zynthian/zynthian-case/Lasercut - PiScreen2/connectors/DIN5-rsonline.pdf

### RS Stock number 490-844

# ENGLISH

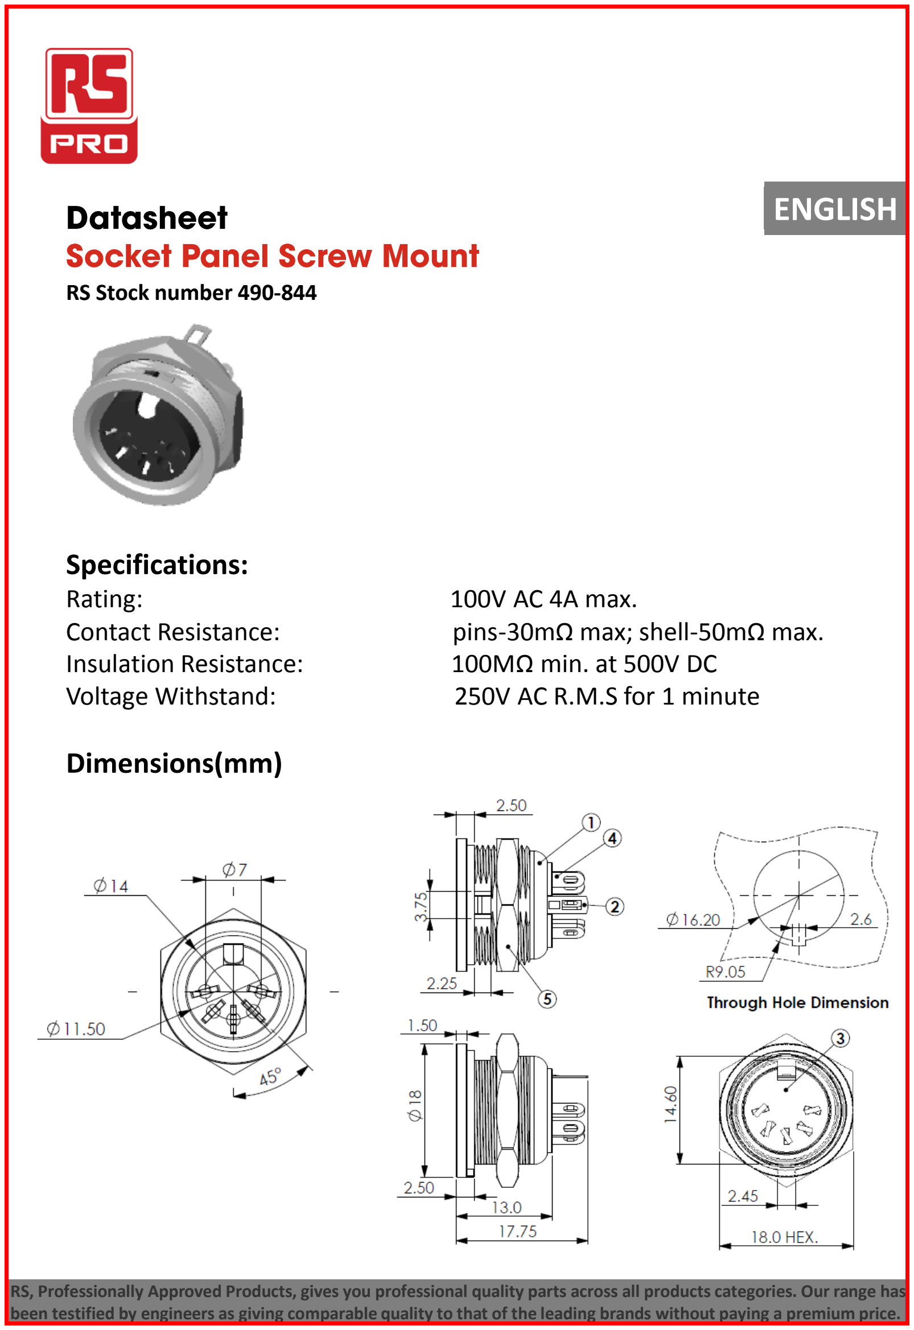
[picture p8: page 1]

## Specifications:

Rating: | 100V AC 4A max.
Contact Resistance: | pins-30mΩ max; shell-50mΩ max.
Insulation Resistance: | 100MΩ min. at 500V DC
Voltage Withstand: | 250V AC R.M.S for 1 minute

## Dimensions(mm)

RS, Professionally Approved Products, gives you professional quality parts across all products categories. Our range has been testified by engineers as giving comparable quality to that of the leading brands without paying a premium price.
