zynthian/zynthian-case/Aluminum - PiTFT28/zynthian_box_aluminum_v03_knobs.pdf

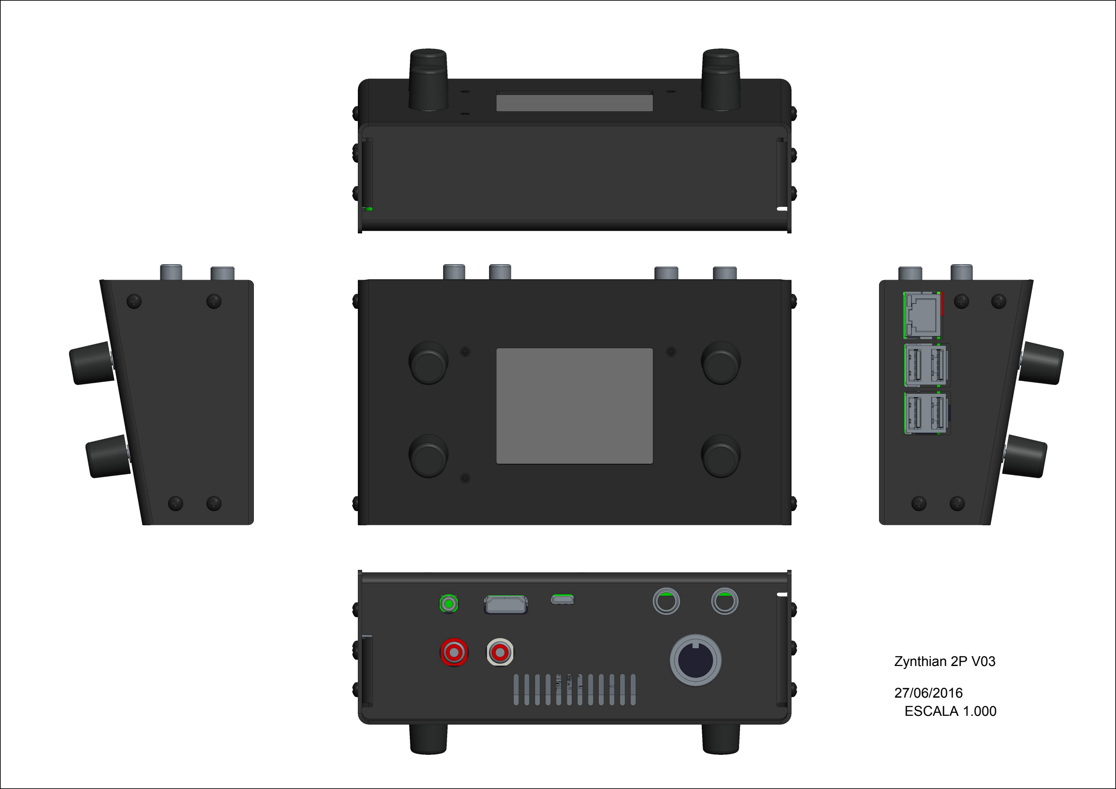
[picture p18: page 1]

Zynthian 2P V03
27/06/2016
ESCALA 1.000

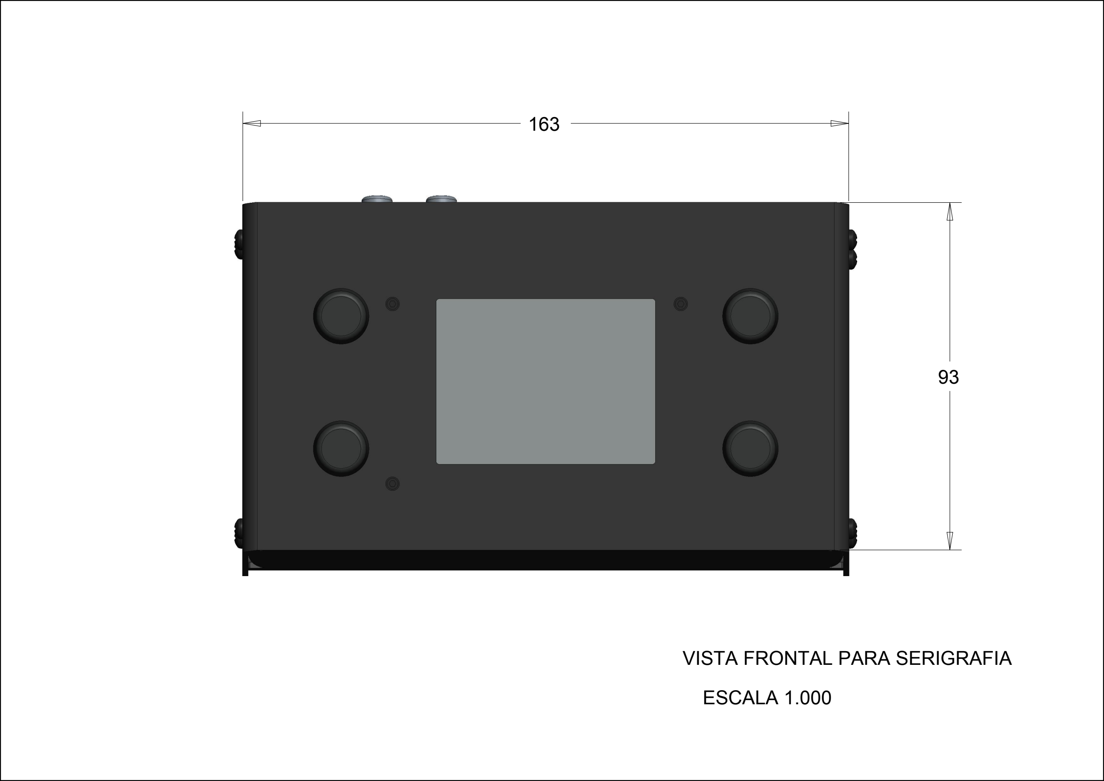
[picture p19: figure]
VISTA FRONTAL PARA SERIGRAFIA; ESCALA 1.000

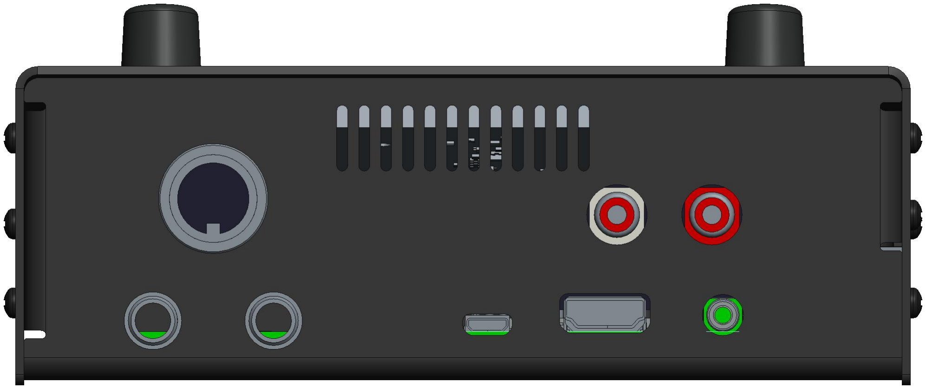
[picture p20: figure]

ESCALA 1.000

ESCALA 1.000

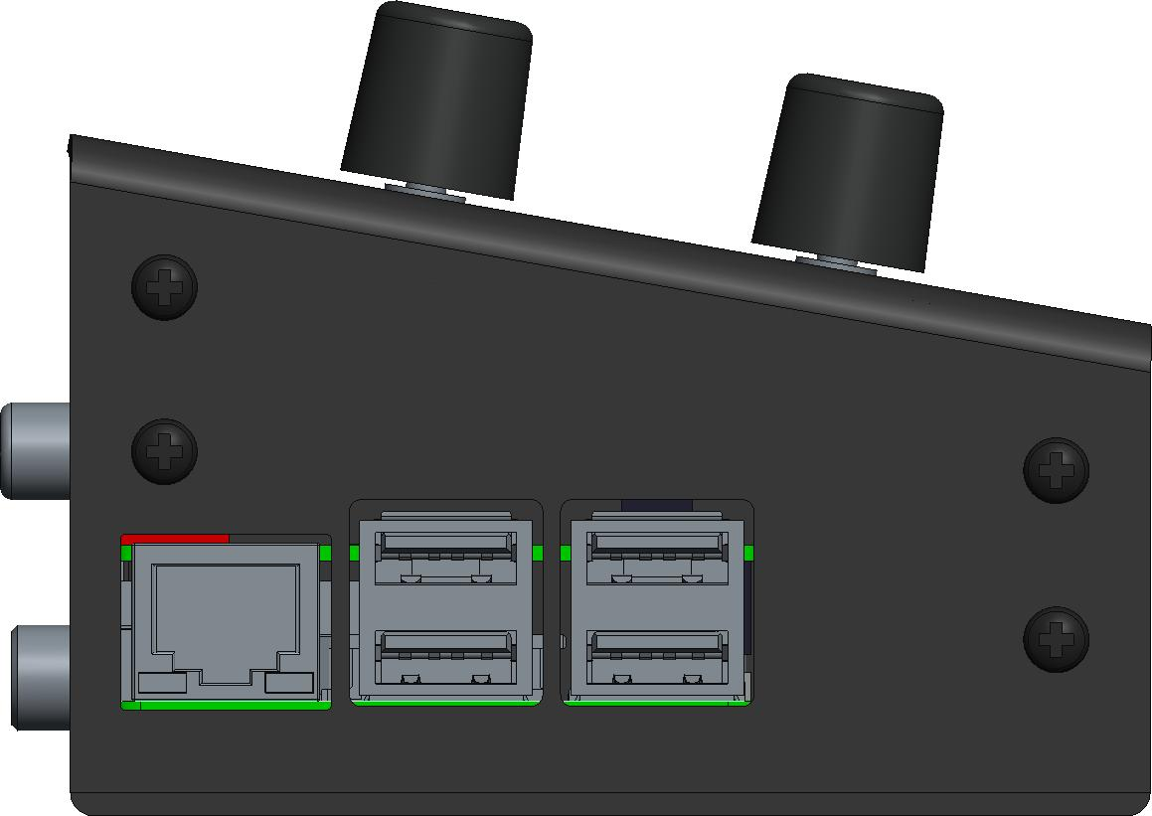
[picture p21: figure]

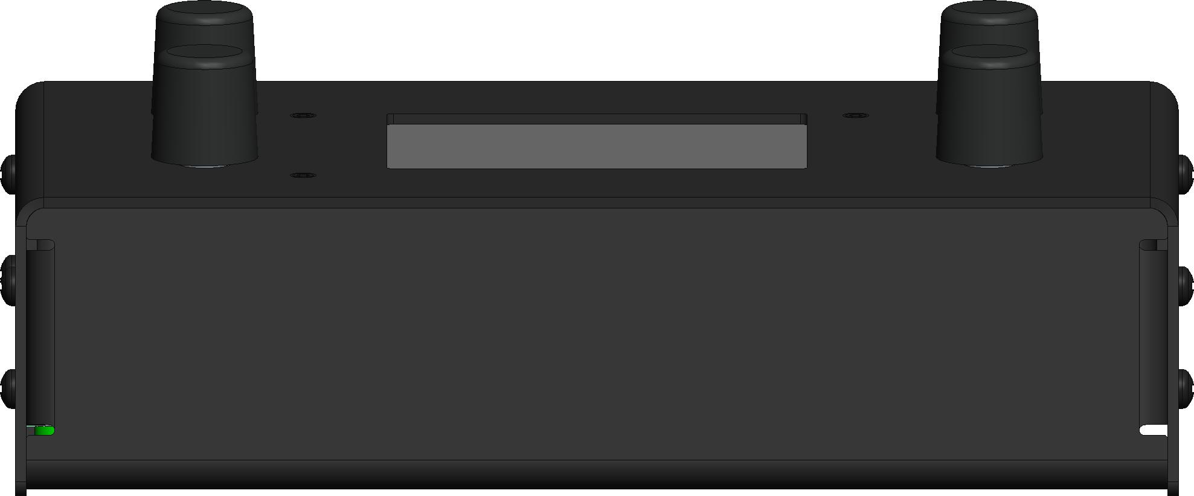
[picture p22: figure]

ESCALA 1.000
