zynthian/zynthian-case/Aluminum - PiTFT28/zynthian_box_aluminum_v03_serig.pdf

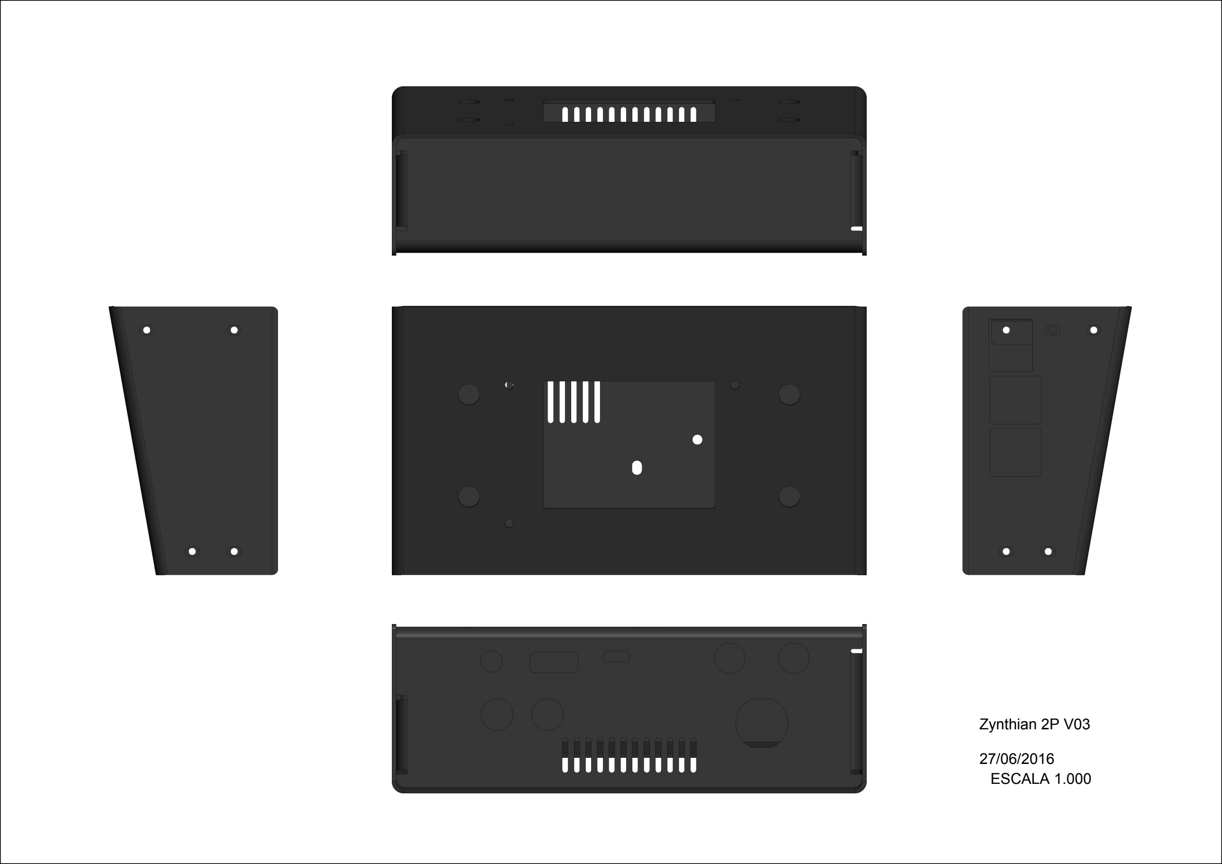
[picture p23: page 1]

Zynthian 2P V03
27/06/2016
ESCALA 1.000

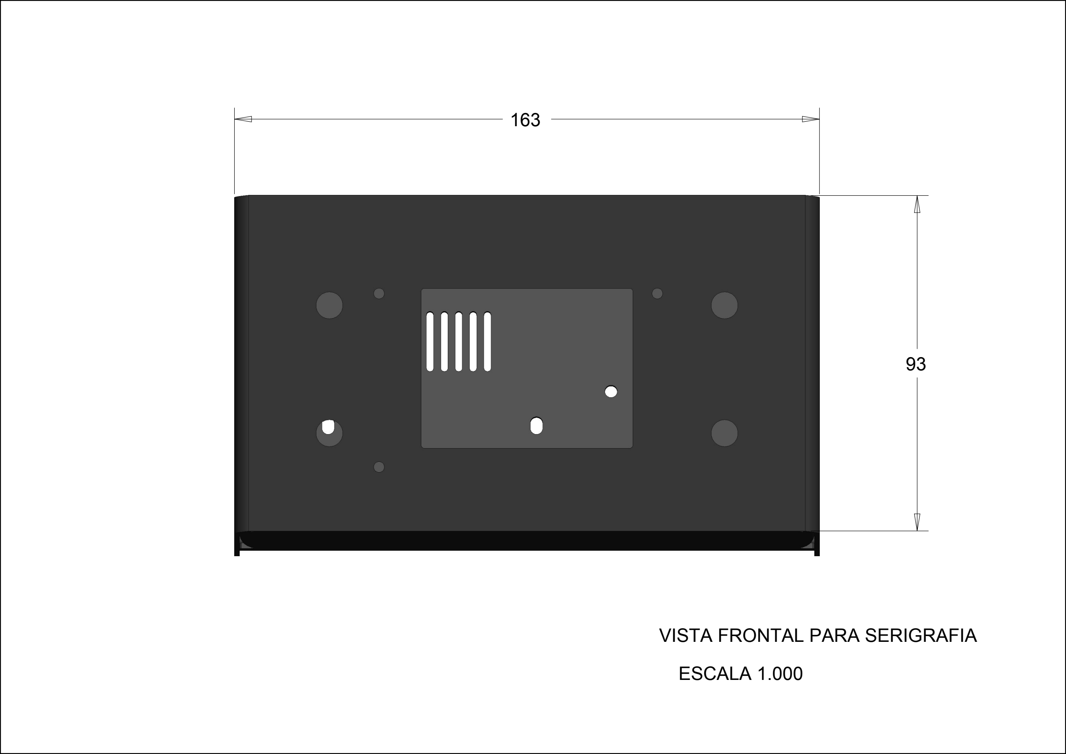
[picture p24: figure]
VISTA FRONTAL PARA SERIGRAFIA; ESCALA 1.000

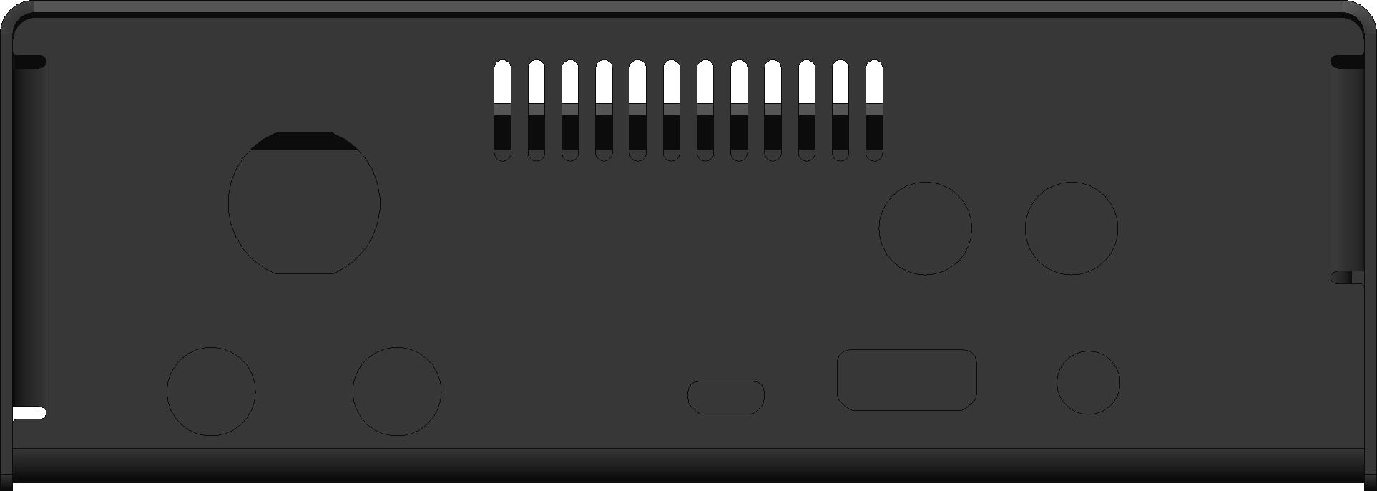
[picture p25: figure]

ESCALA 1.000

ESCALA 1.000

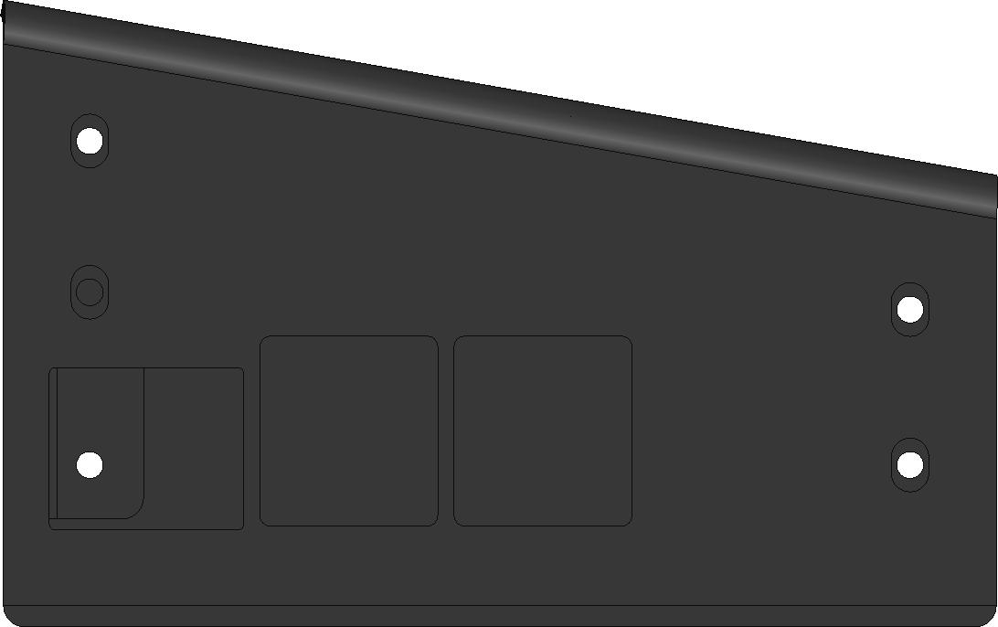
[picture p26: figure]

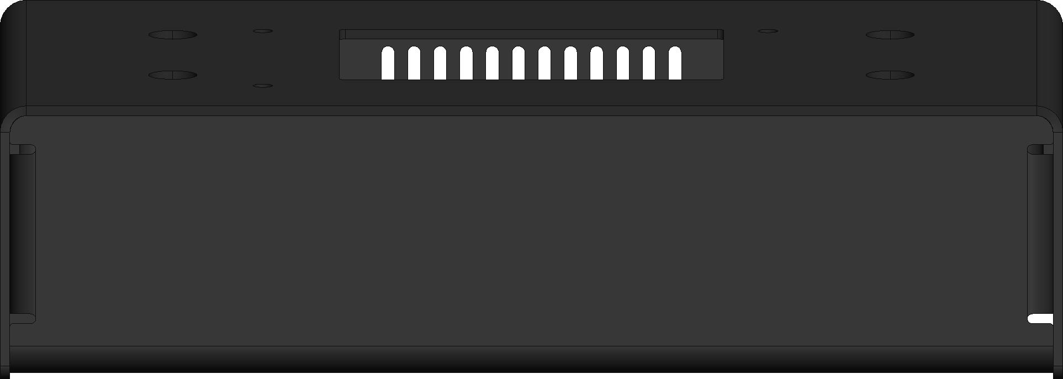
[picture p27: figure]

ESCALA 1.000
