zynthian/zynthian-case/Aluminum - PiTFT28/zynthian_box_aluminum_v04.pdf

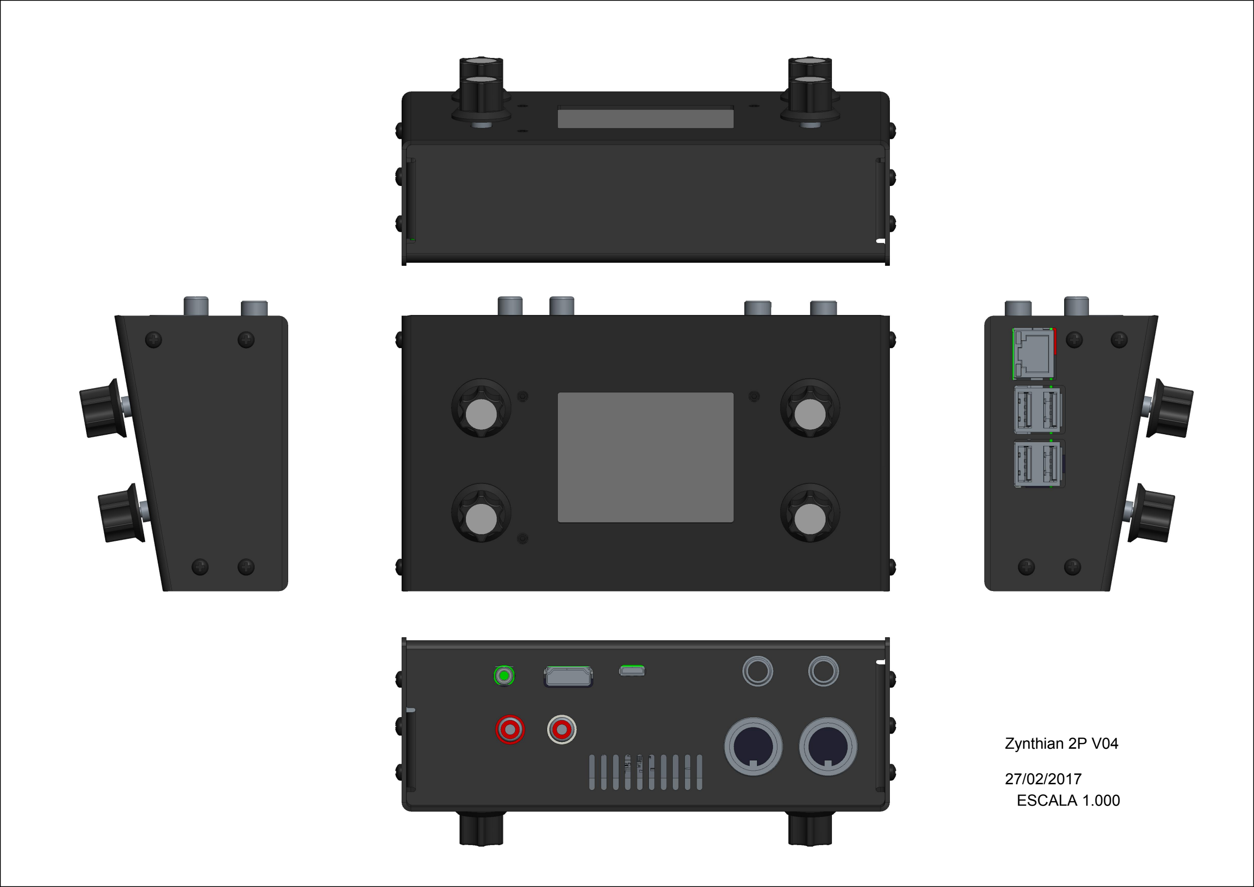
[picture p28: page 1]

Zynthian 2P V04
27/02/2017
ESCALA 1.000

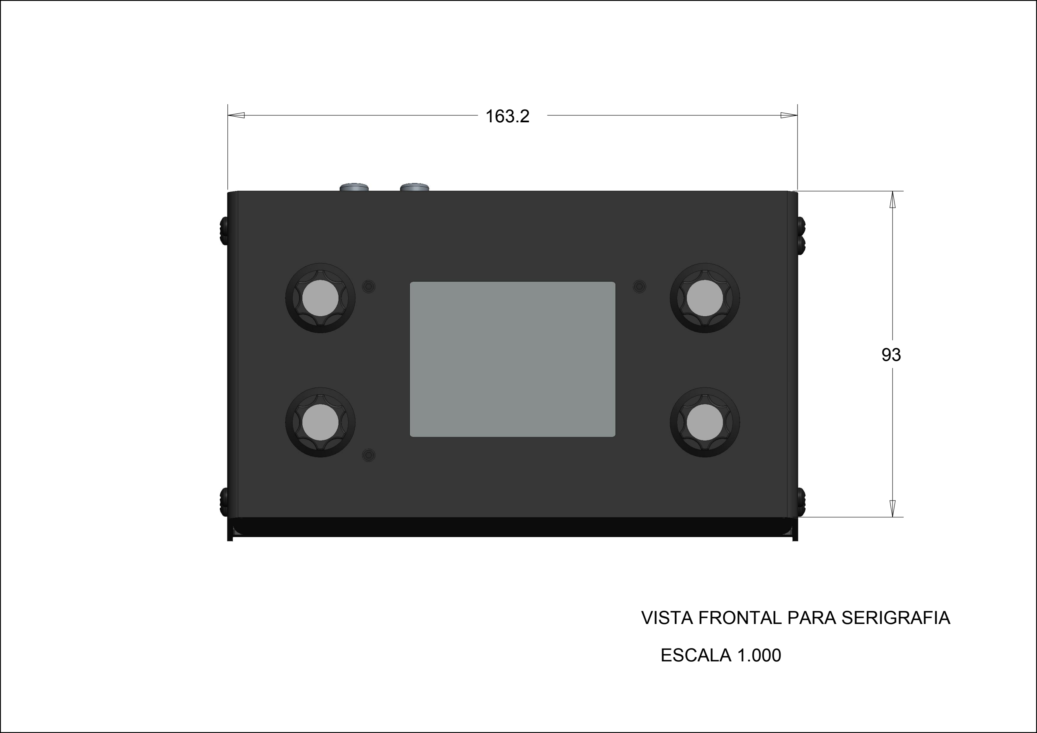
[picture p29: figure]
VISTA FRONTAL PARA SERIGRAFIA; ESCALA 1.000

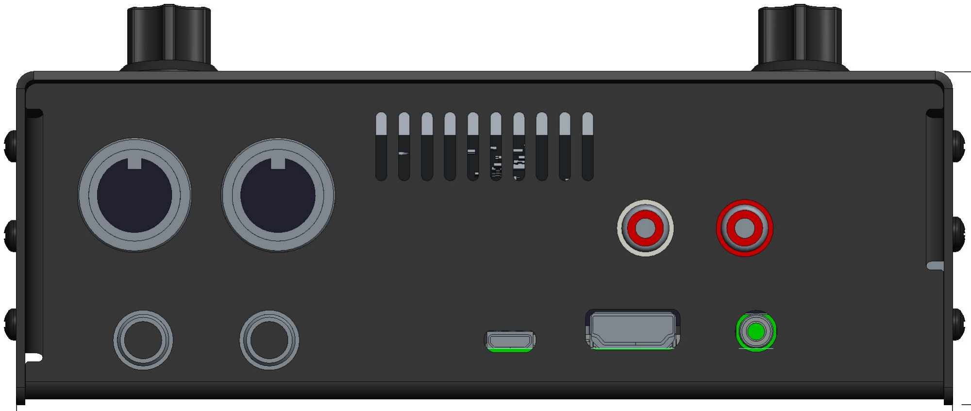
[picture p30: figure]

163.2

58.06

ESCALA 1.000

ESCALA 1.000

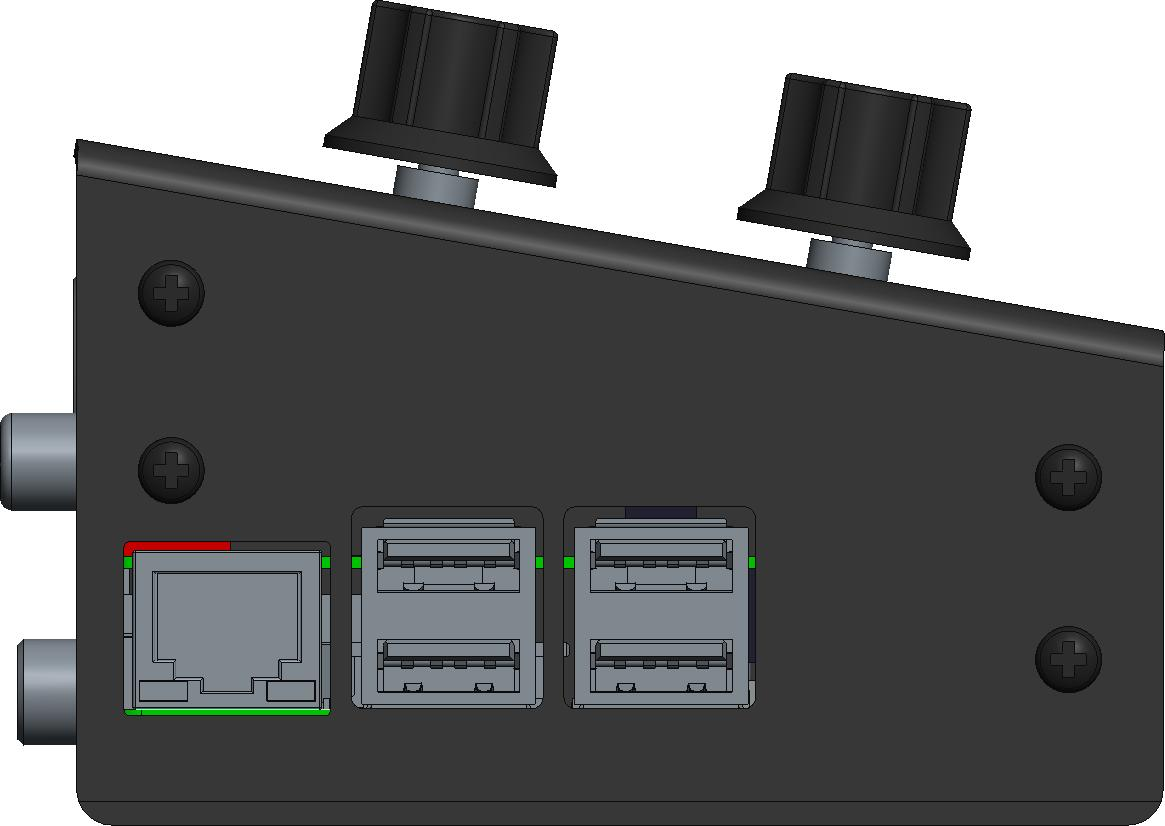
[picture p31: figure]

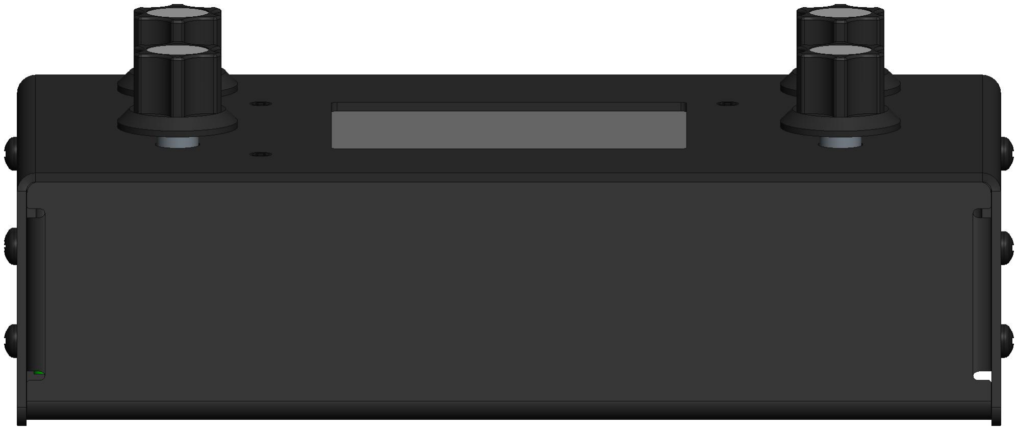
[picture p32: figure]

ESCALA 1.000
