zynthian/zynthian-case/Aluminum - PiTFT28/zynthian_box_aluminum_v04_back.pdf

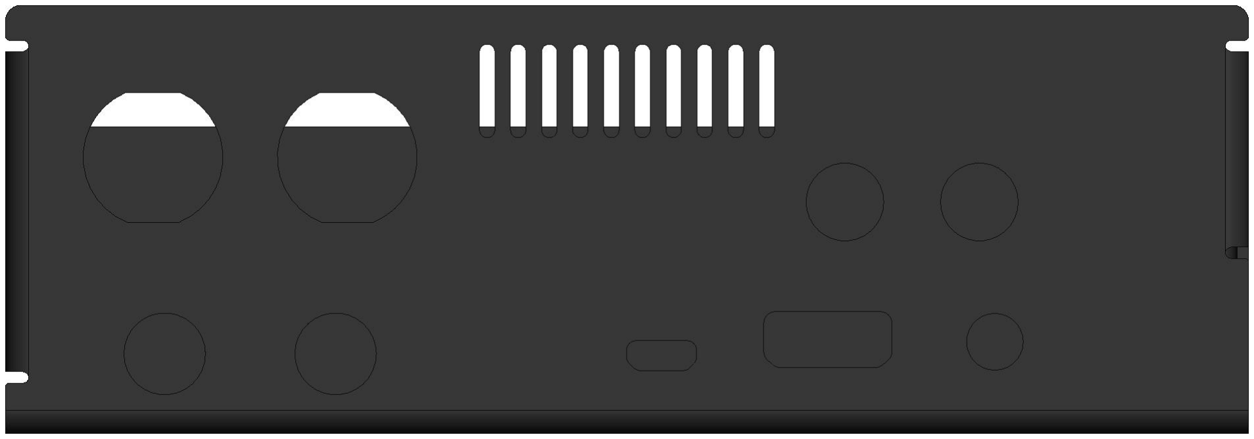
[picture p33: figure]

163.2

58.06

ESCALA 1.000
