zynthian/zynthian-case/Aluminum - PiTFT28/zynthian_box_aluminum_v04_base_desp.pdf

178.21

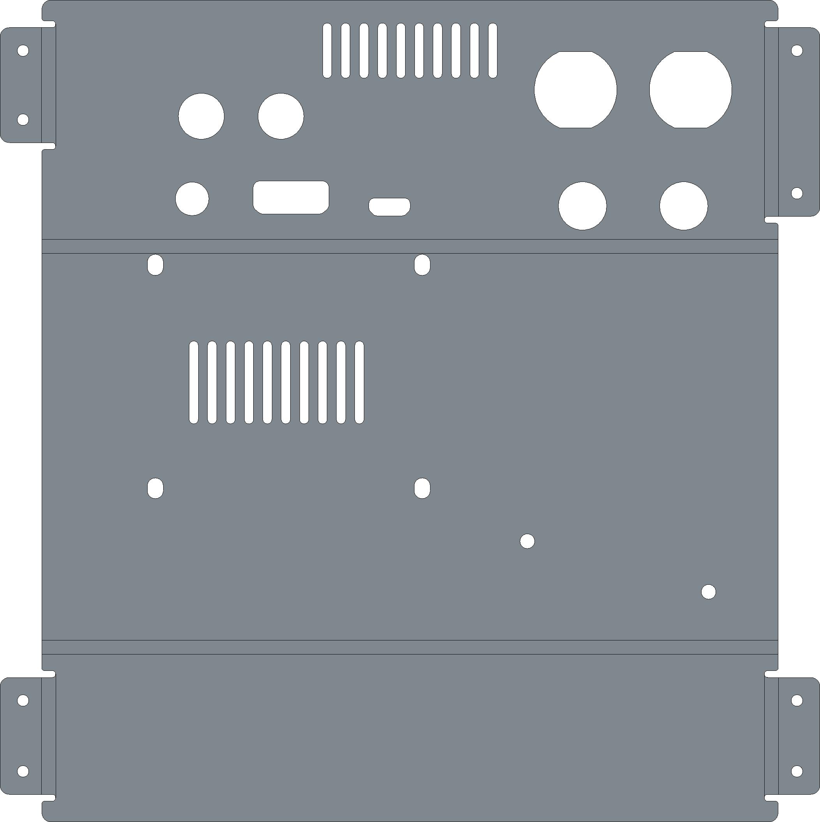
[picture p34: figure]

178.61

ESCALA 1.000
