zynthian/zynthian-case/Aluminum - PiScreen-v2.1/zynthian_box_2p_3midi_v05.pdf

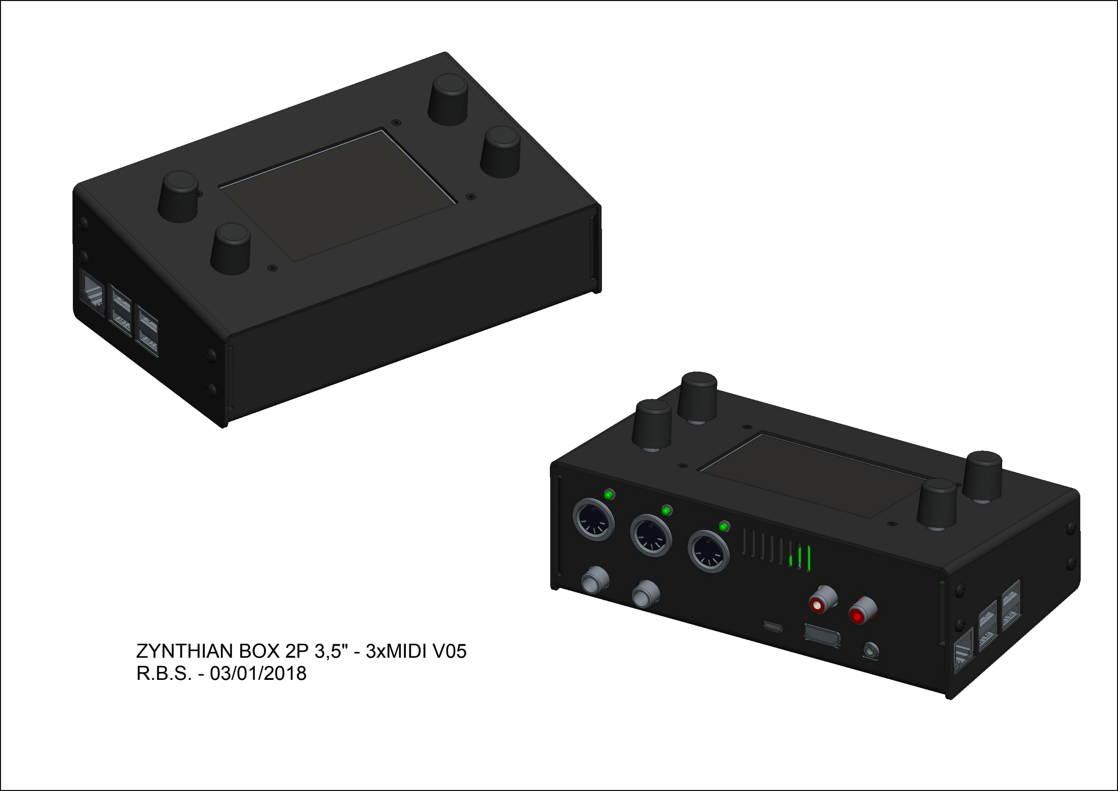
[picture p35: page 1]

ZYNTHIAN BOX 2P 3,5" - 3xMIDI V05 R.B.S. - 03/01/2018

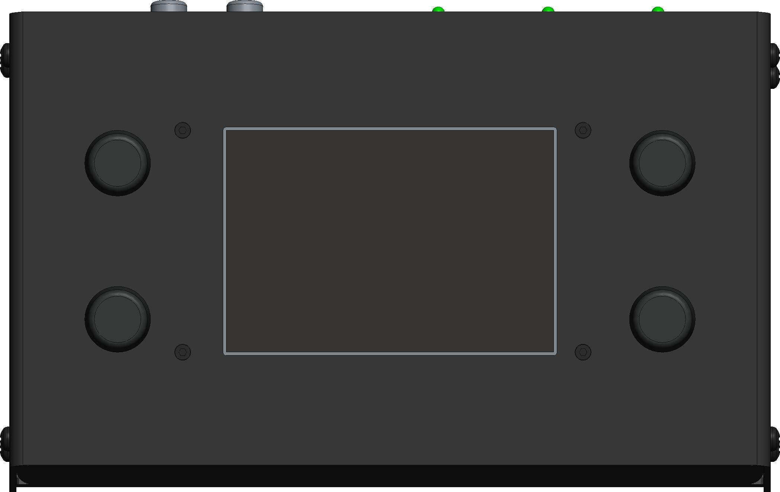
[picture p36: figure]

FRONTAL PARA SERIGRAFIA
ZYNTHIAN BOX 2P 3,5" 3xMIDI V05
ESCALA 1.000 | R.B.S - 03/01/2018

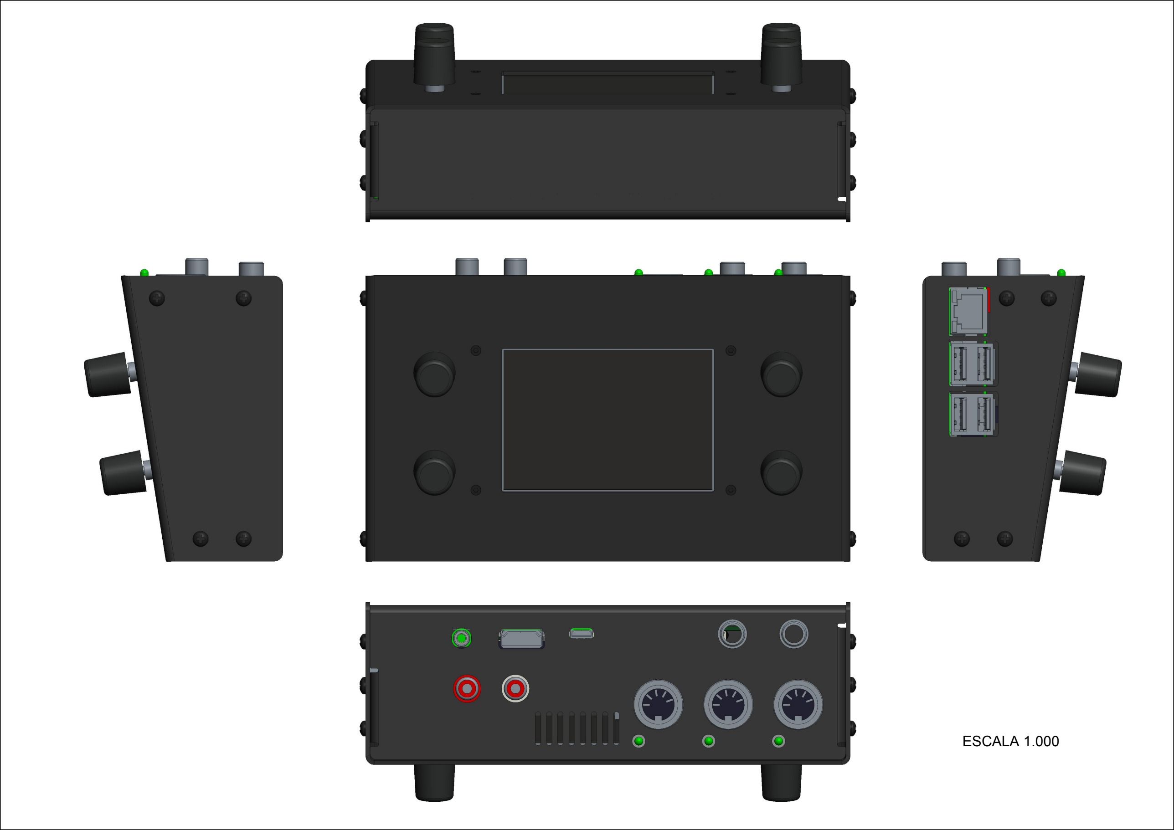
[picture p37: page 3]

ESCALA 1.000

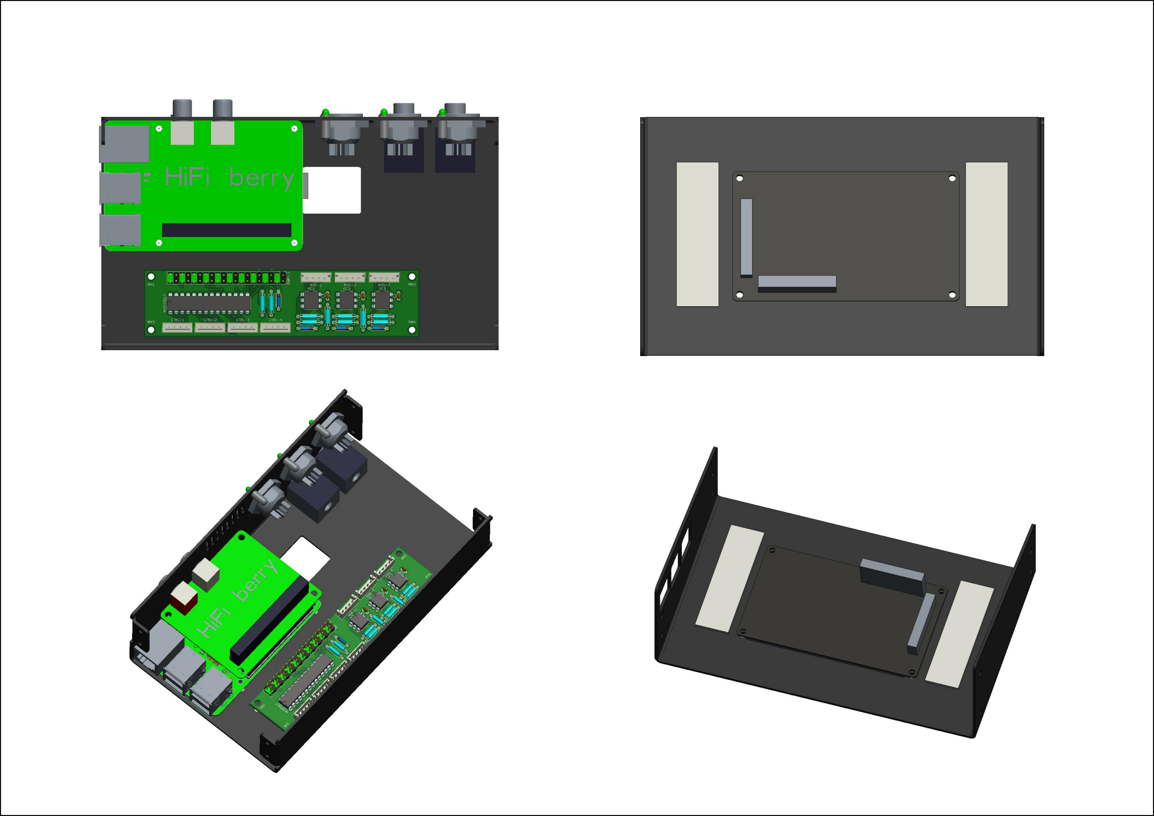
[picture p38: page 4]

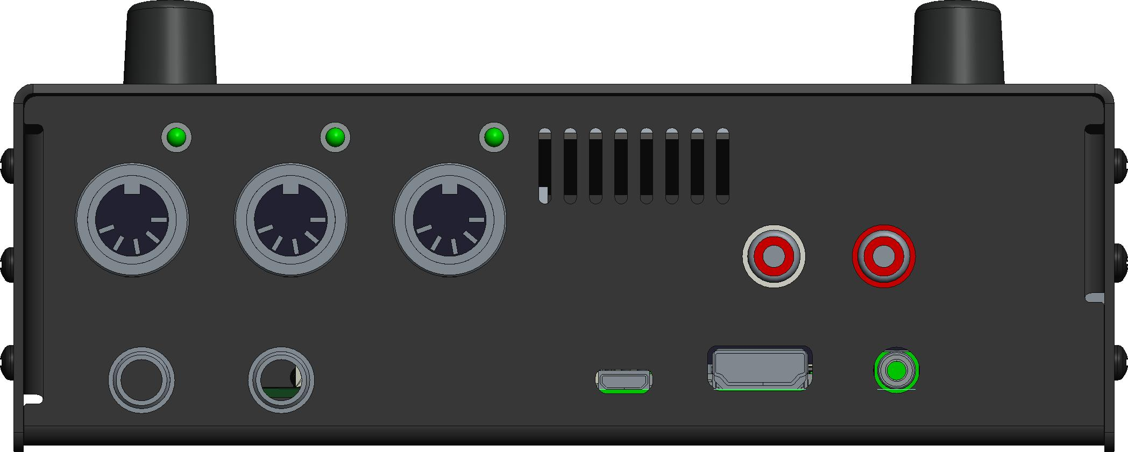
[picture p39: figure]

ESCALA 1.000
