zynthian/zynthian-case/Aluminum - PiScreen-v2/zynthian_box_2p_3_5_v04.pdf

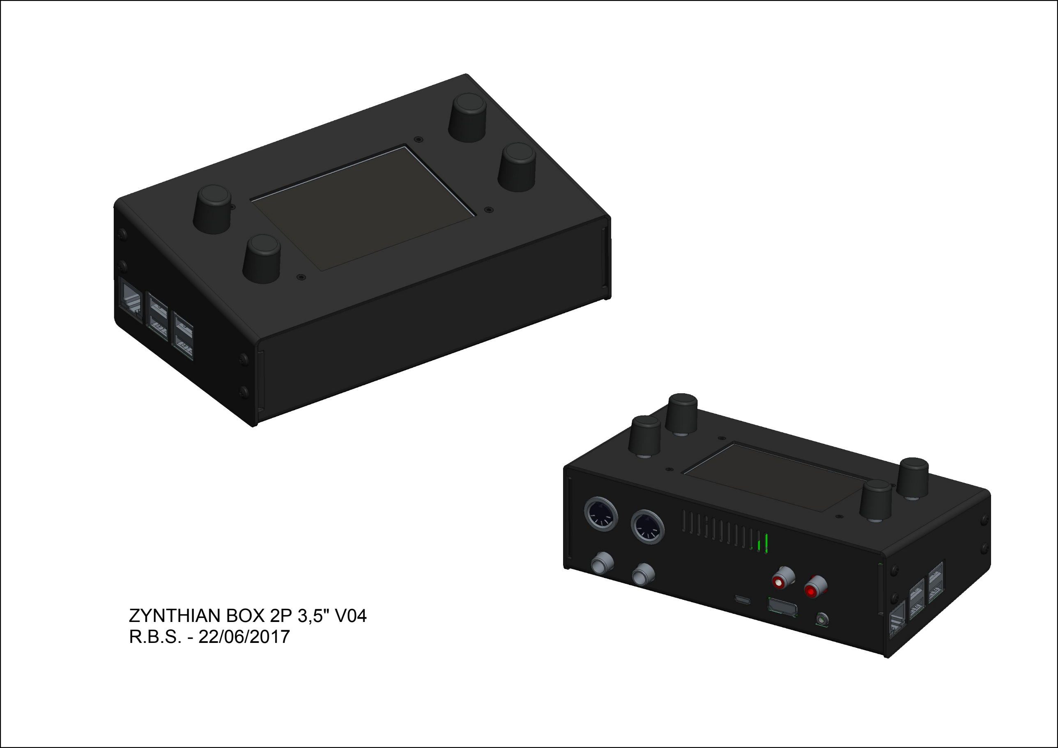
[picture p40: page 1]

ZYNTHIAN BOX 2P 3,5" V04
R.B.S. - 22/06/2017

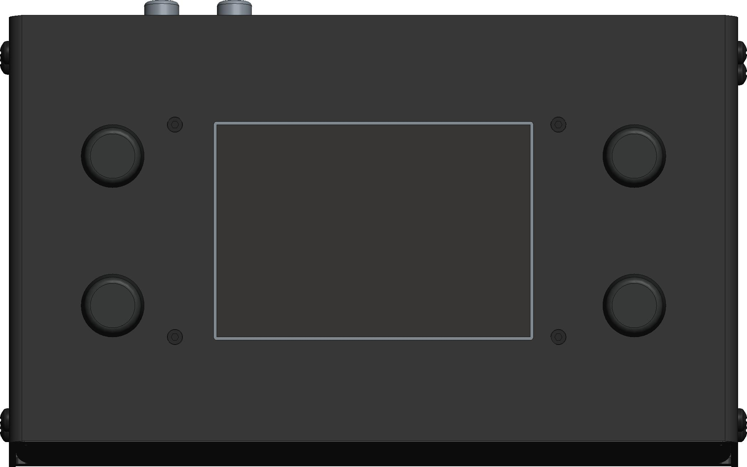
[picture p41: figure]

FRONTAL PARA SERIGRAFIA
ZYNTHIAN BOX 2P 3,5" V04
ESCALA 1.000 | R.B.S - 23/05/2017

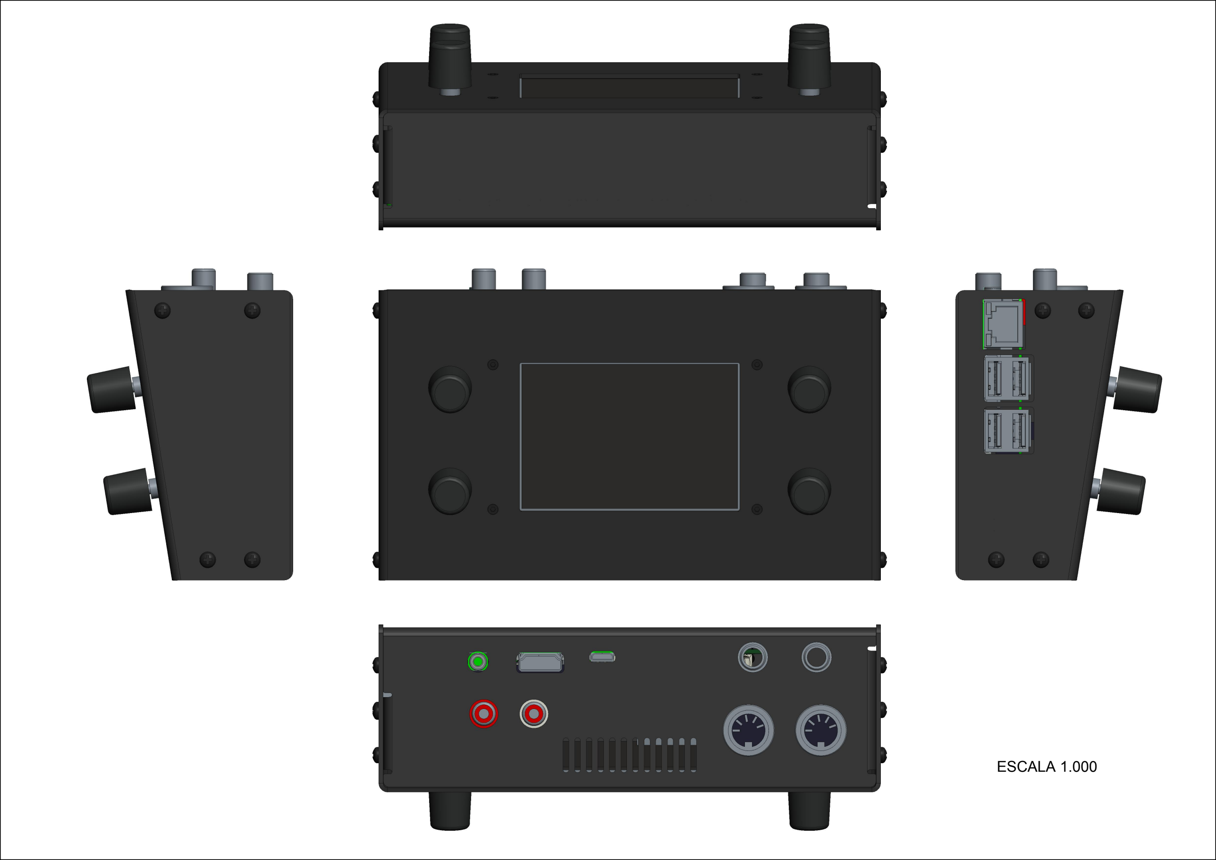
[picture p42: page 3]

ESCALA 1.000

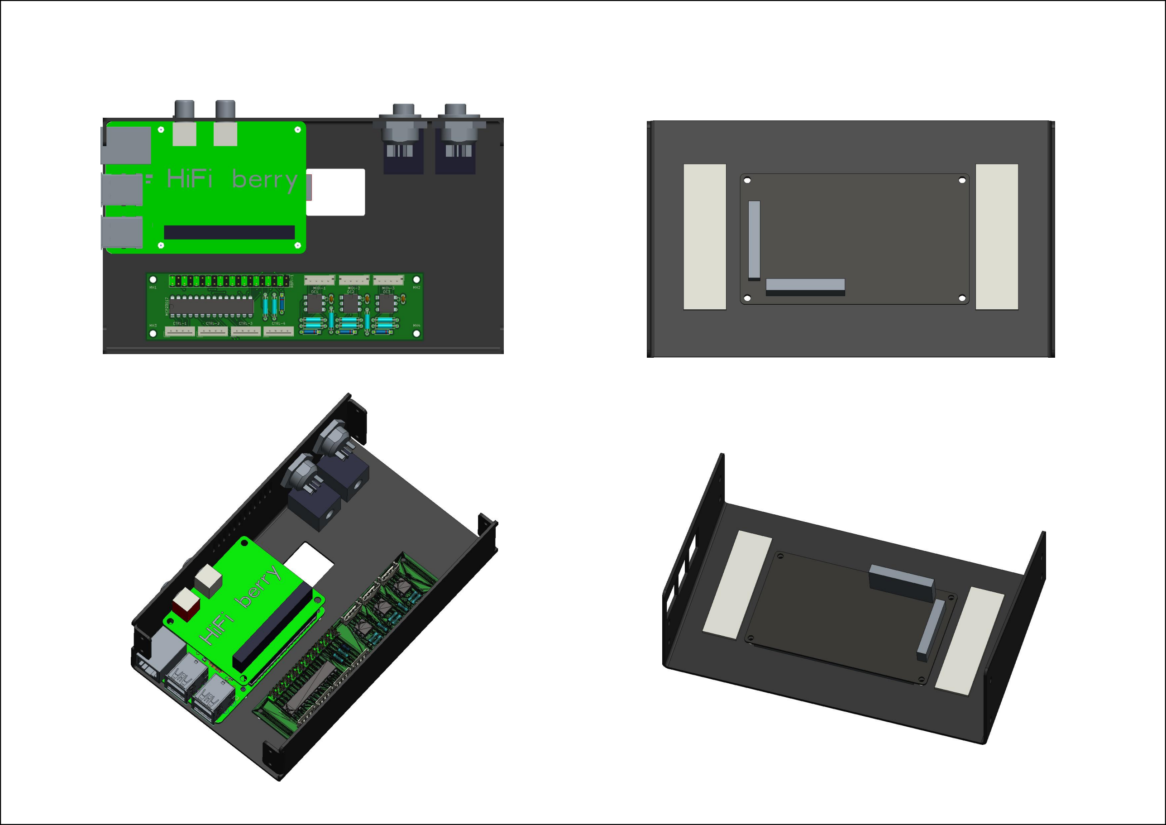
[picture p43: page 4]
