zynthian/zynthian-case/Aluminum - PiScreen-v2.2/old/zynthian_box_2p_v06_mjack.pdf

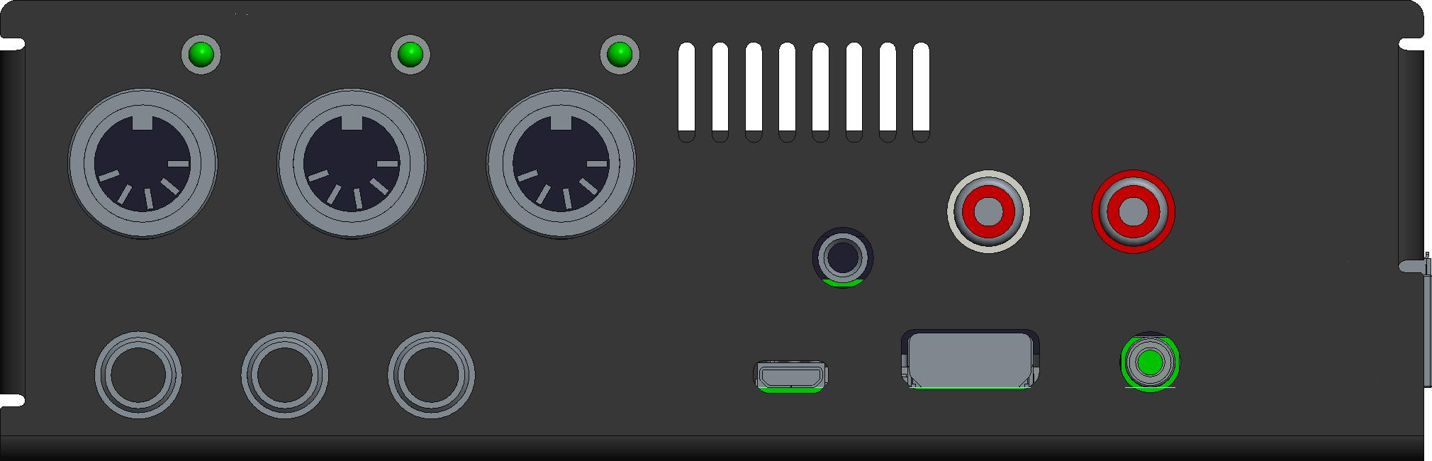
[picture p44: figure]

ESCALA 1.000
