zynthian/zynthian-case/Steel - PiTFT28/old/zynthian_box_V01_29_7_15.pdf

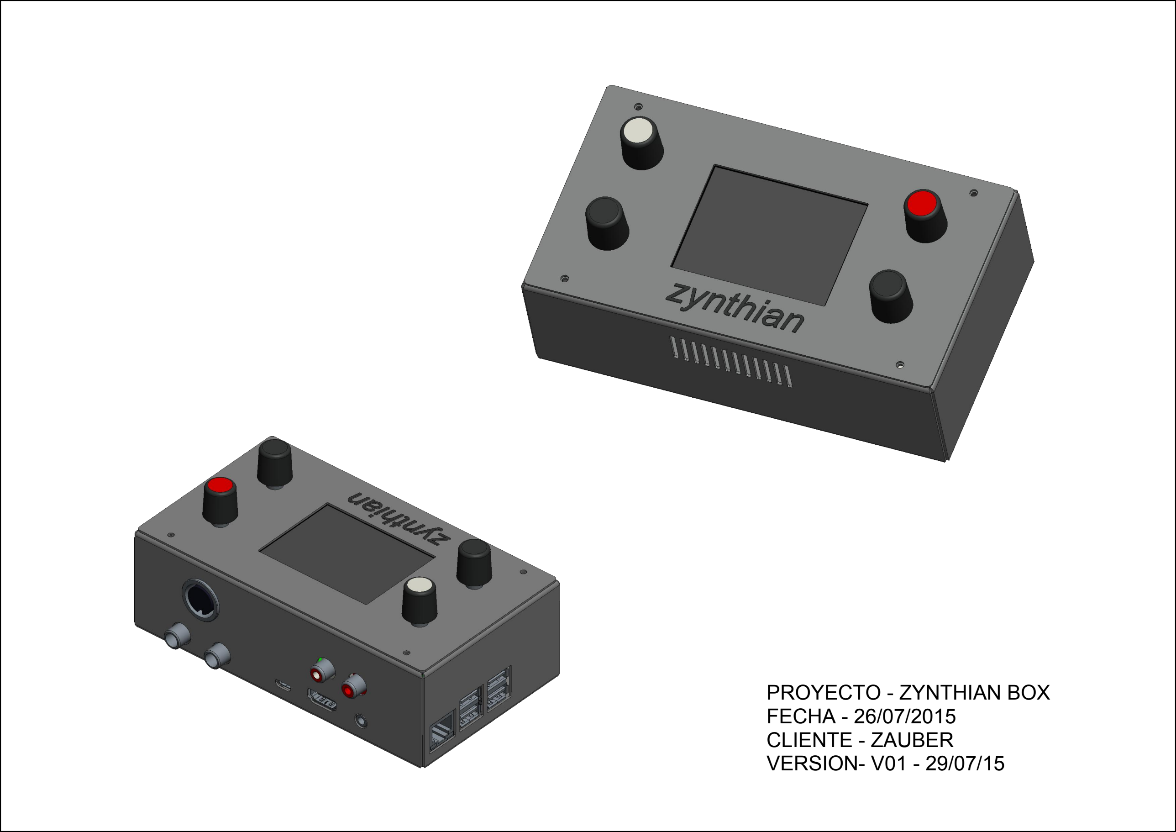
[picture p45: page 1]

PROYECTO - ZYNTHIAN BOX
FECHA - 26/07/2015
CLIENTE - ZAUBER
VERSION- V01 - 29/07/15

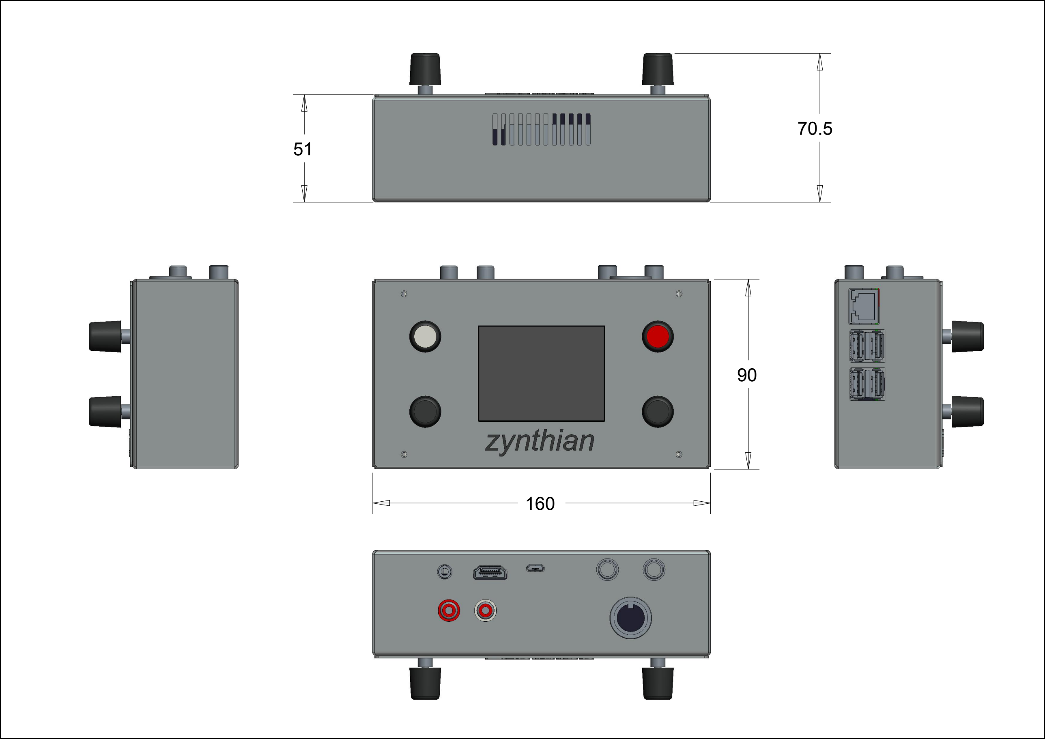
[picture p46: figure]
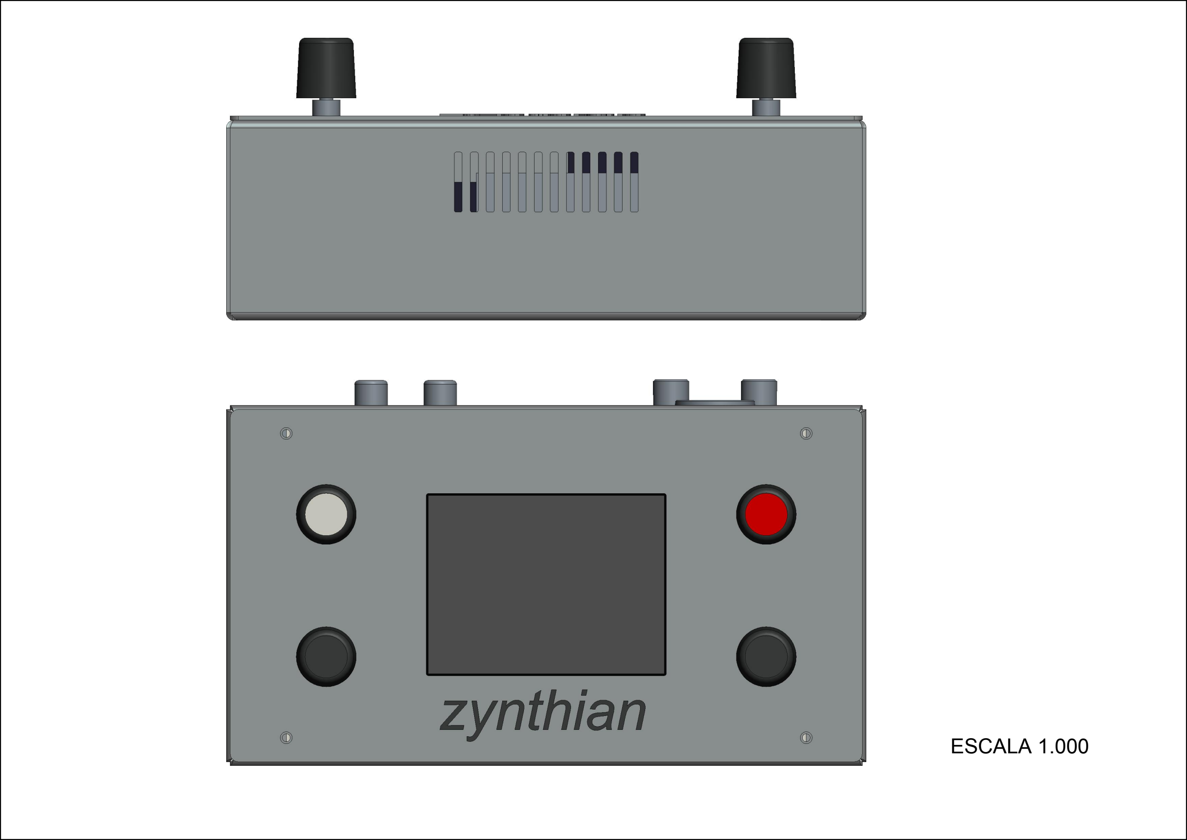
[picture p47: page 3]

ESCALA 1.000

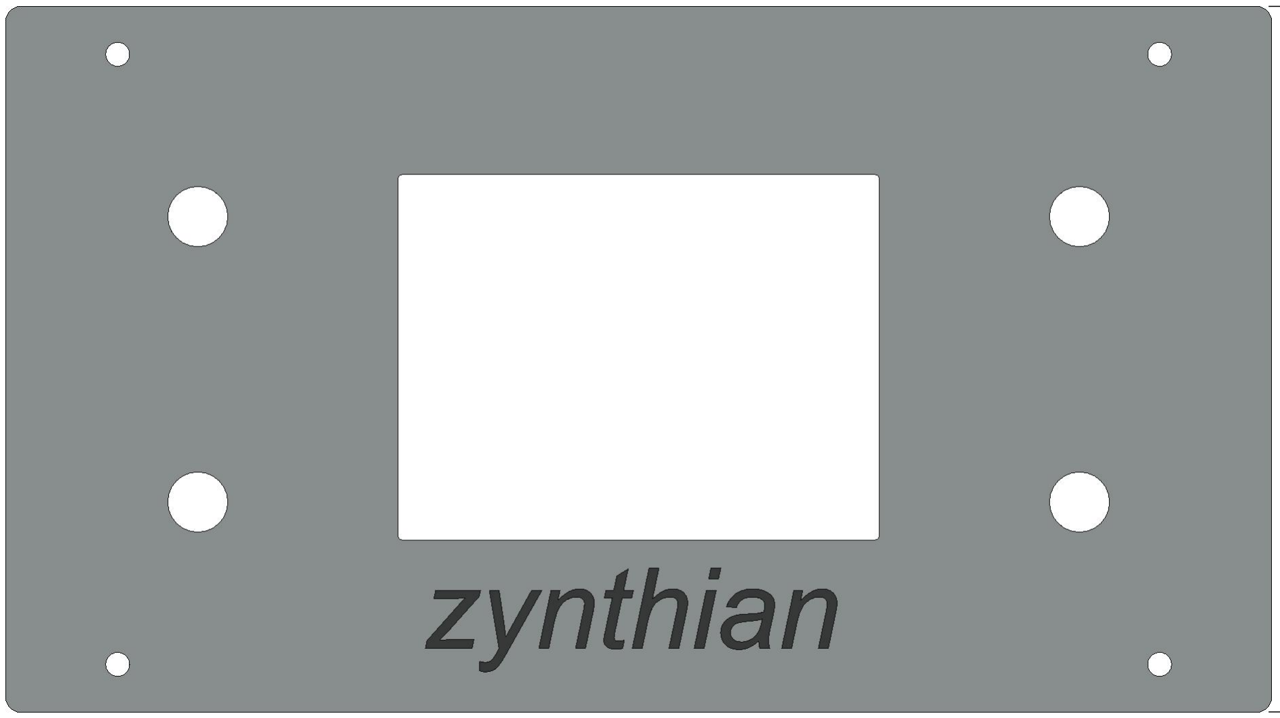
[picture p48: figure]

88

ESCALA 1.000

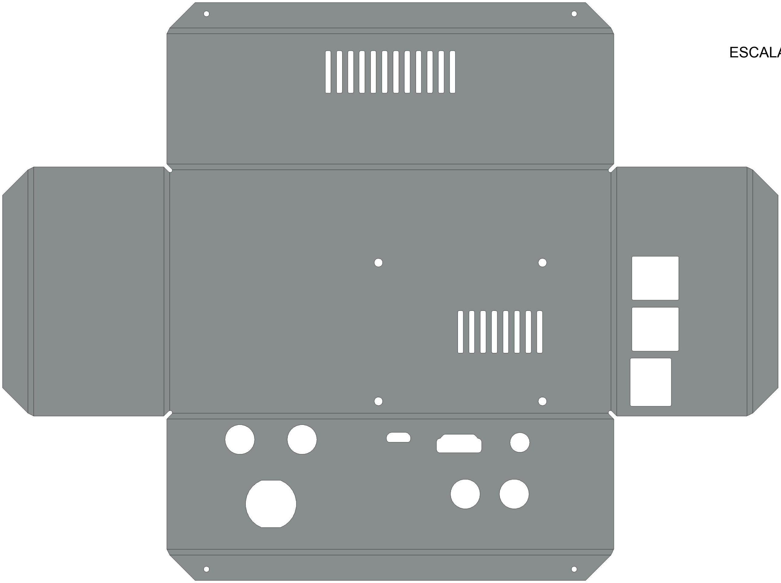
[picture p49: figure]

204.28

274.28

ESCALA 1.000

88

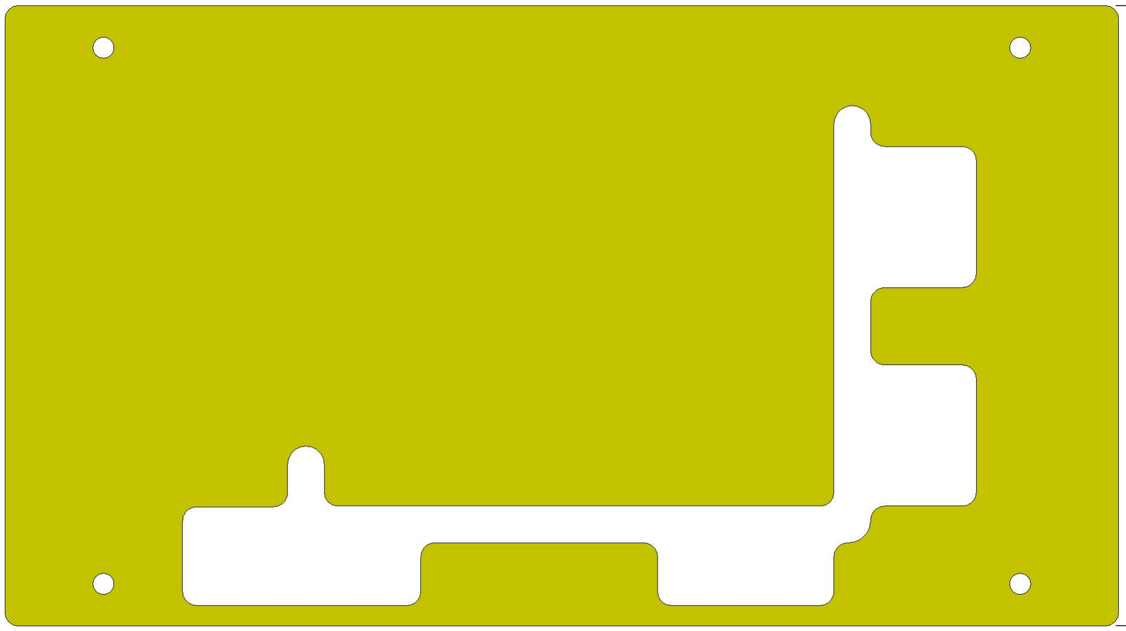
[picture p50: figure]

ESCALA 1.000

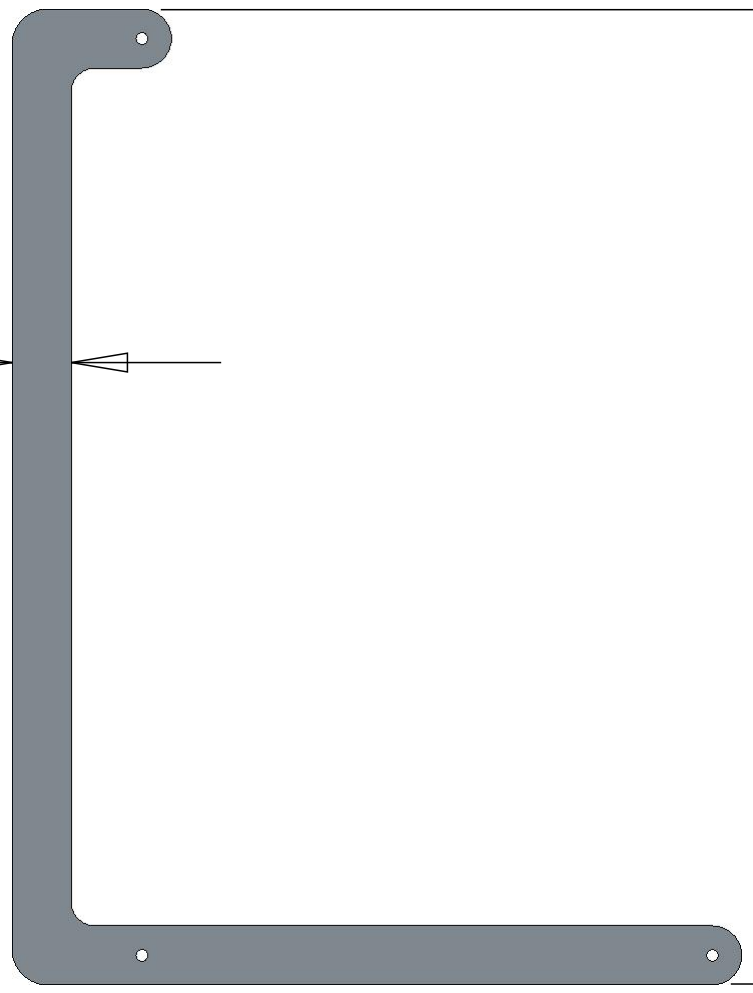
[picture p51: figure]

82.47

5

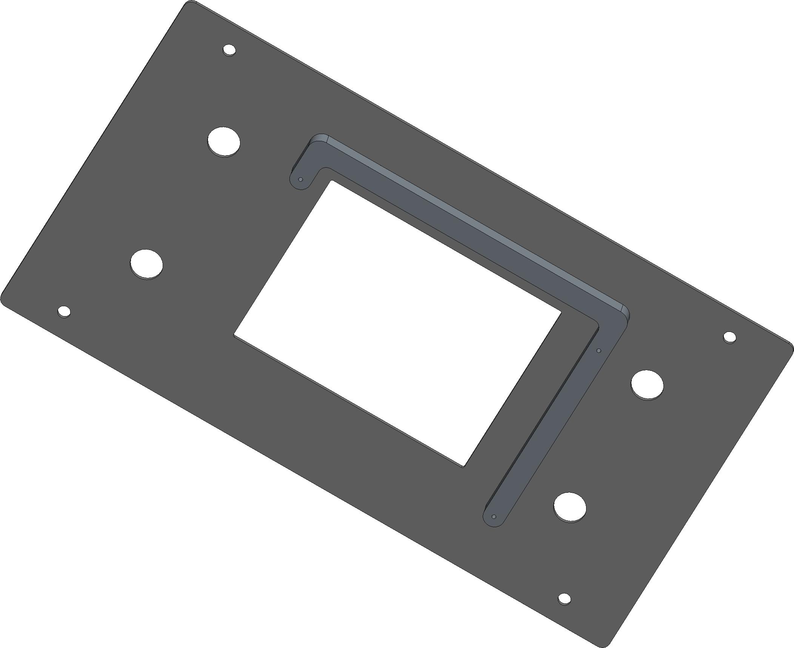
[picture p52: figure]

ESCALA 1.000
