zynthian/zynthian-case/3DPrint - Waveshare35/back_view.jpg

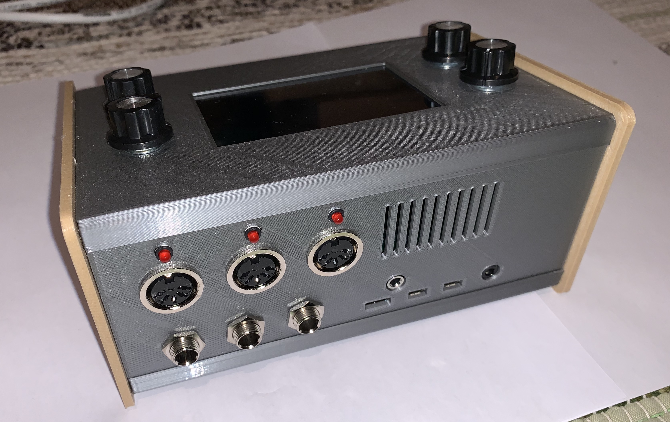
3DPrint - Waveshare35/back_view.jpg
