zynthian/zynthian-case/3DPrint - Waveshare35/boards_mounting.jpg

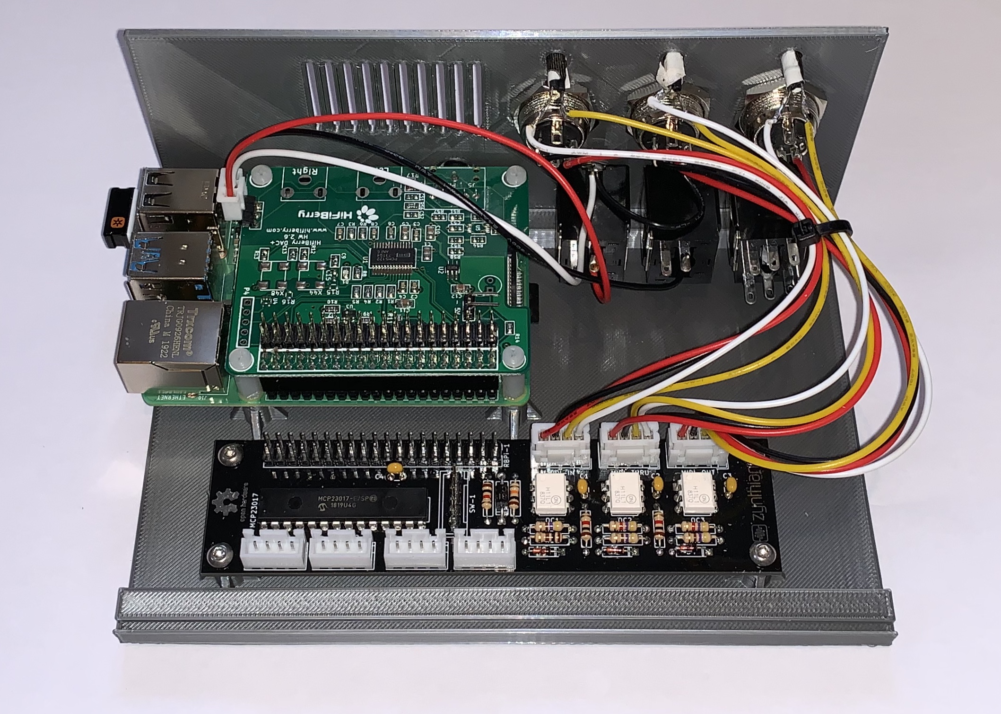
3DPrint - Waveshare35/boards_mounting.jpg
