zynthian/zynthian-case/3DPrint - Waveshare35/display_mounting.jpg

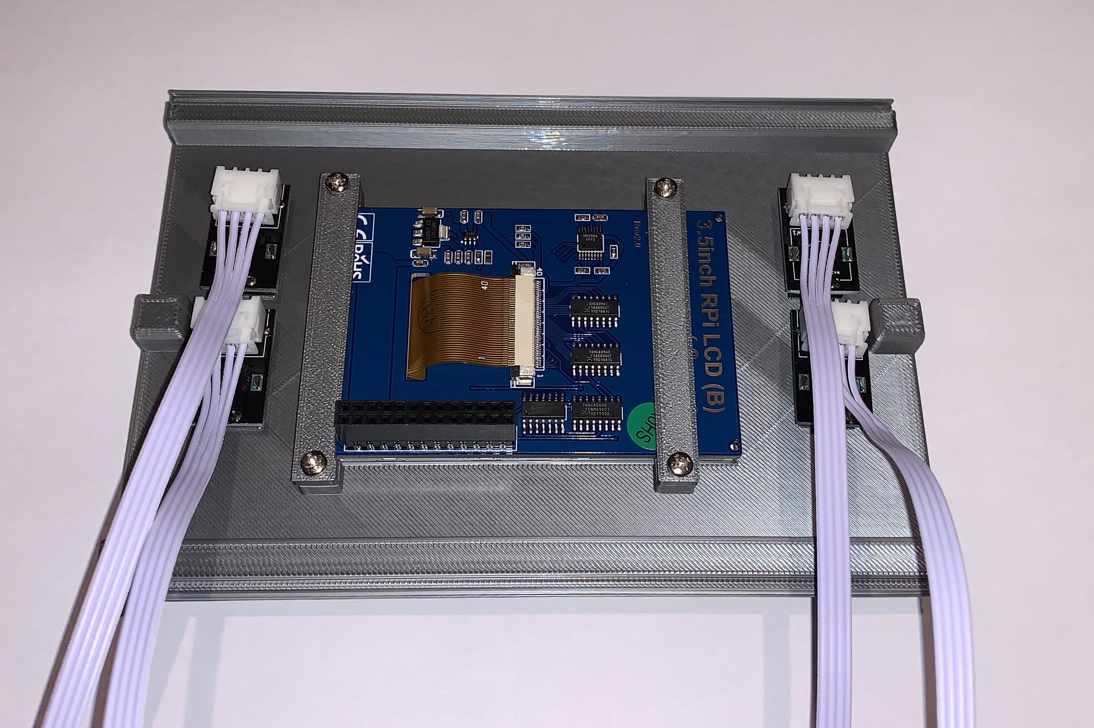
3DPrint - Waveshare35/display_mounting.jpg
