zynthian/zynthian-case/3DPrint - Waveshare35/front_view.jpg

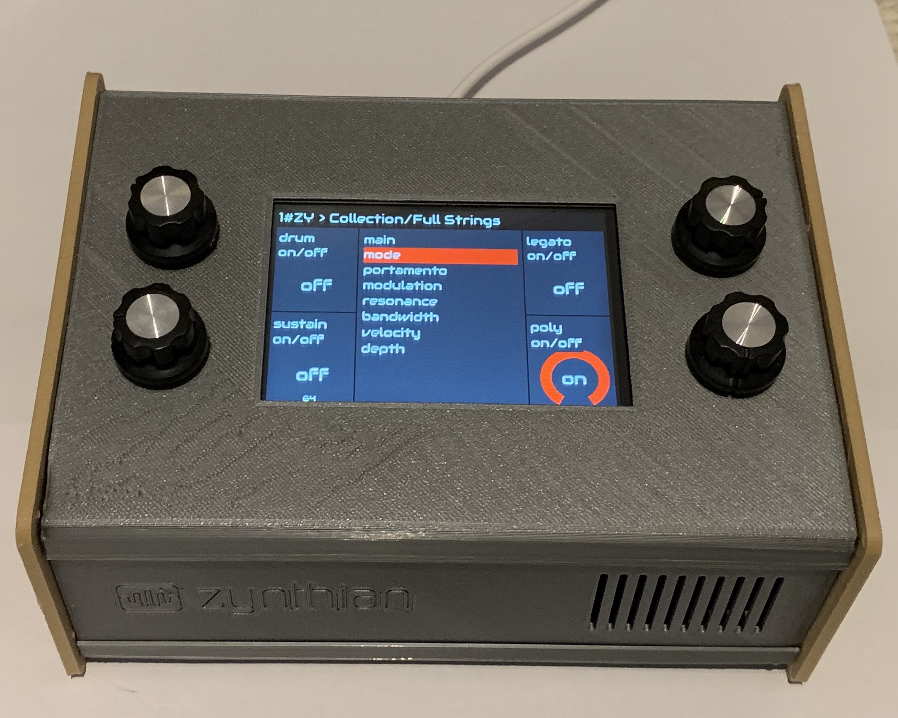
3DPrint - Waveshare35/front_view.jpg
