zynthian/zynthian-case/Aluminum - PiScreen-v2.2/g1220.png

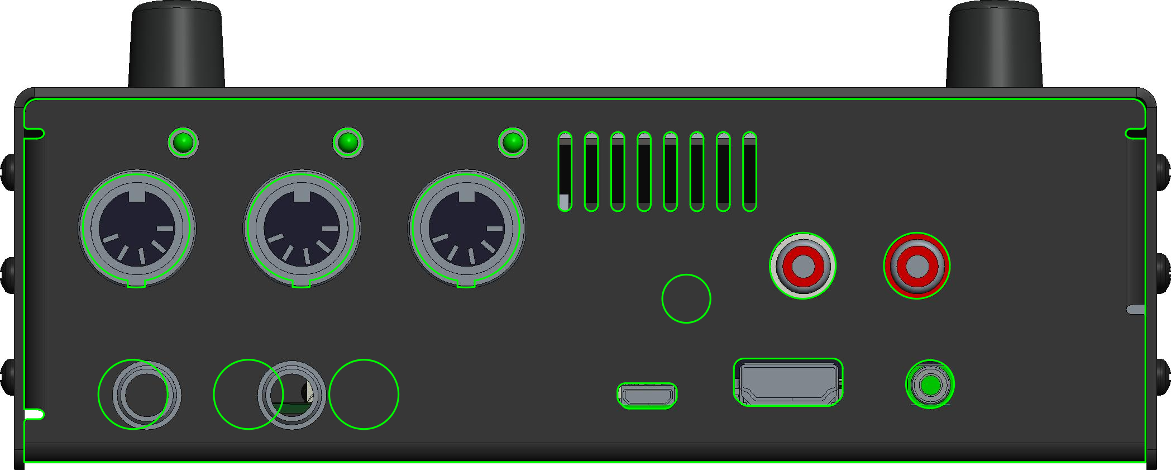
Aluminum - PiScreen-v2.2/g1220.png
