zynthian/zynthian-case/Aluminum - PiScreen-v2.2/image002.jpg

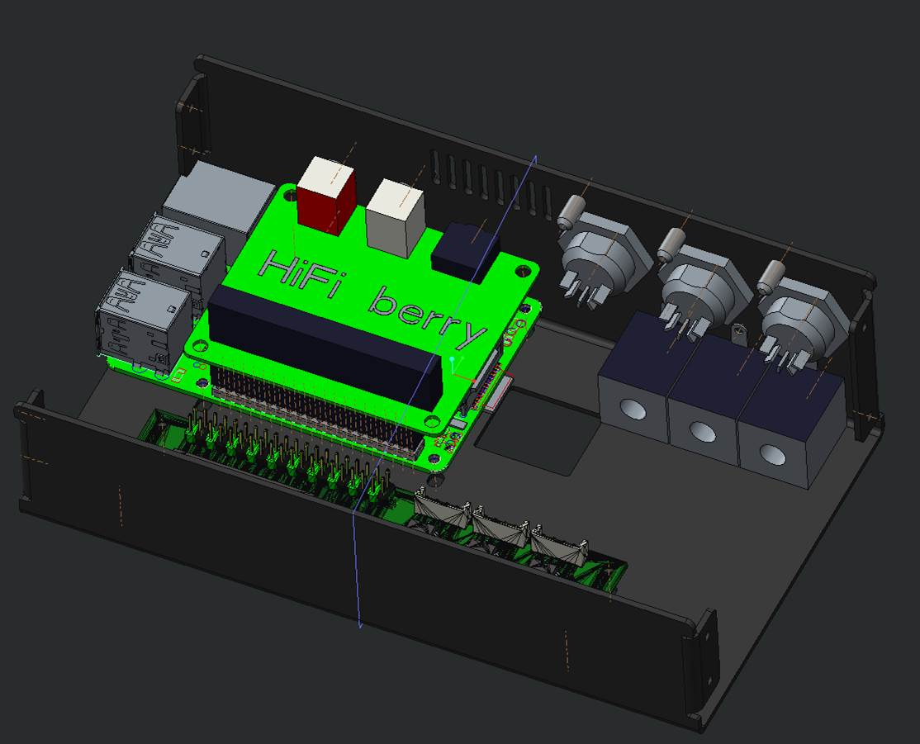
Aluminum - PiScreen-v2.2/image002.jpg
