zynthian/zynthian-case/Aluminum - PiScreen-v2.2/image007.jpg

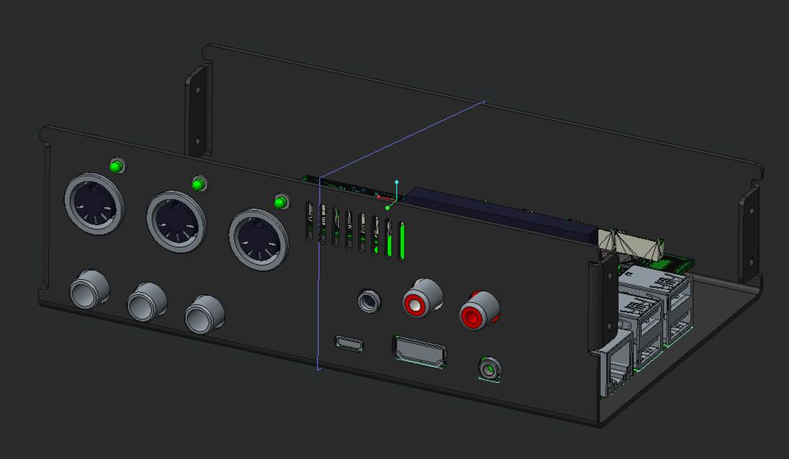
Aluminum - PiScreen-v2.2/image007.jpg
