zynthian/zynthian-case/Aluminum - PiTFT28/zynthian_aluminum_case_kit.jpg

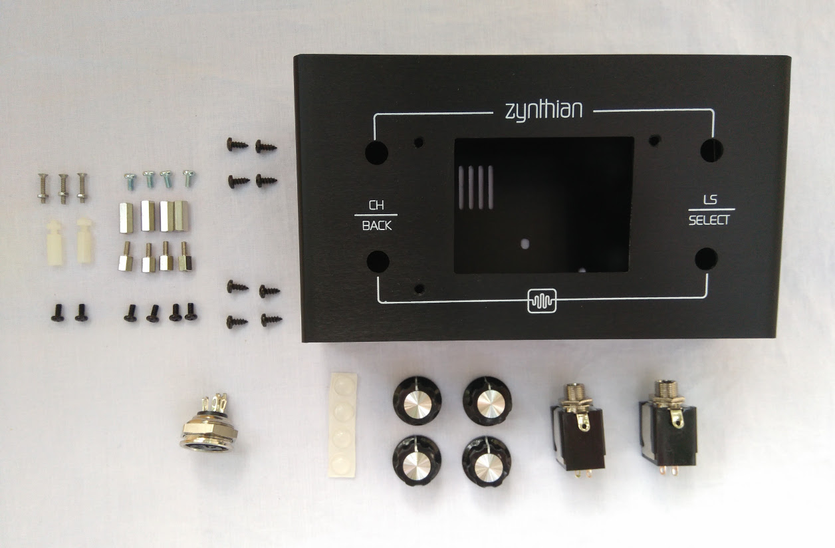
Aluminum - PiTFT28/zynthian_aluminum_case_kit.jpg
