zynthian/zynthian-case/Aluminum - PiTFT28/zynthian_box_alucase_02.jpg

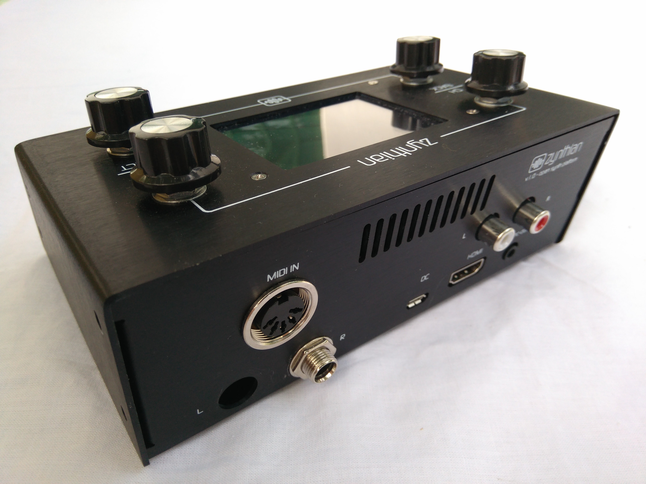
Aluminum - PiTFT28/zynthian_box_alucase_02.jpg
