zynthian/zynthian-case/Aluminum - Zynscreen-v4/knob_a01.png

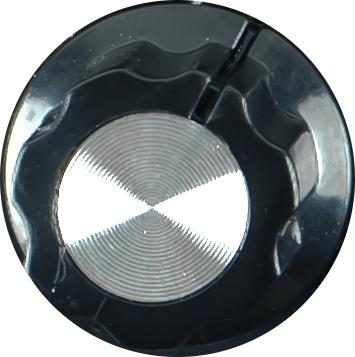
Aluminum - Zynscreen-v4/knob_a01.png
