zynthian/zynthian-case/Aluminum - Zynscreen-v4/knob_a01_txapita.png

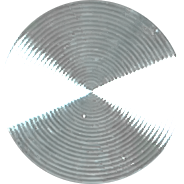
Aluminum - Zynscreen-v4/knob_a01_txapita.png
