zynthian/zynthian-case/Aluminum - Zynscreen-v4/rubber_buttons/zynthian_v4_rubber_buttons.jpg

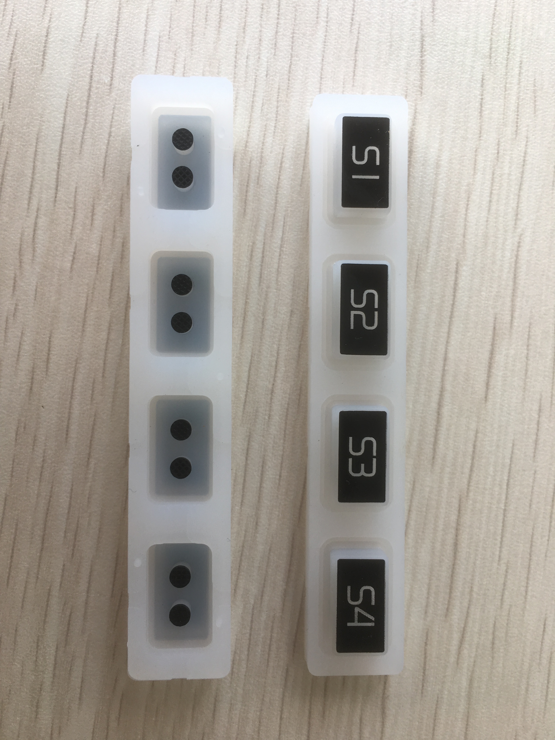
Aluminum - Zynscreen-v4/rubber_buttons/zynthian_v4_rubber_buttons.jpg
