zynthian/zynthian-case/Aluminum - Zynscreen-v4/rubber_buttons/zynthian_v4_rubber_buttons_clean_lr.png

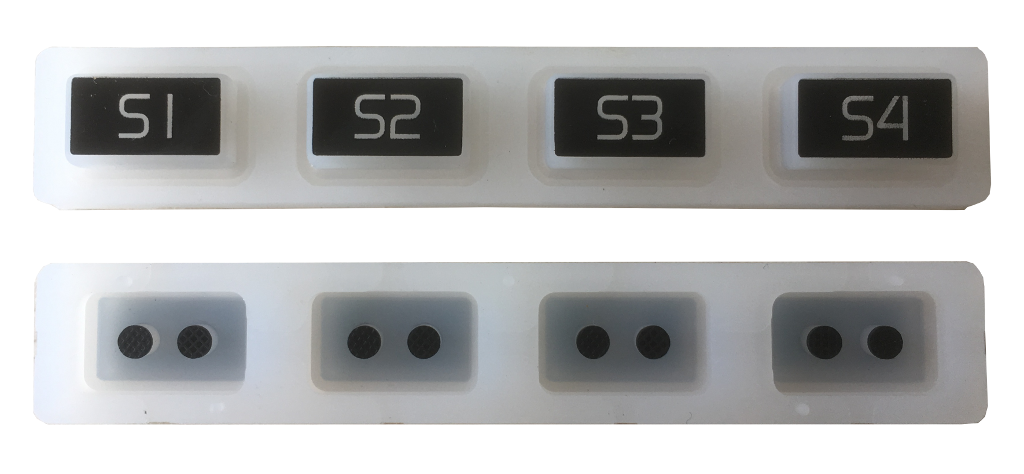
Aluminum - Zynscreen-v4/rubber_buttons/zynthian_v4_rubber_buttons_clean_lr.png
