zynthian/zynthian-case/Aluminum - Zynscreen-v4/v4_render_zenital_mixer_tide.jpg

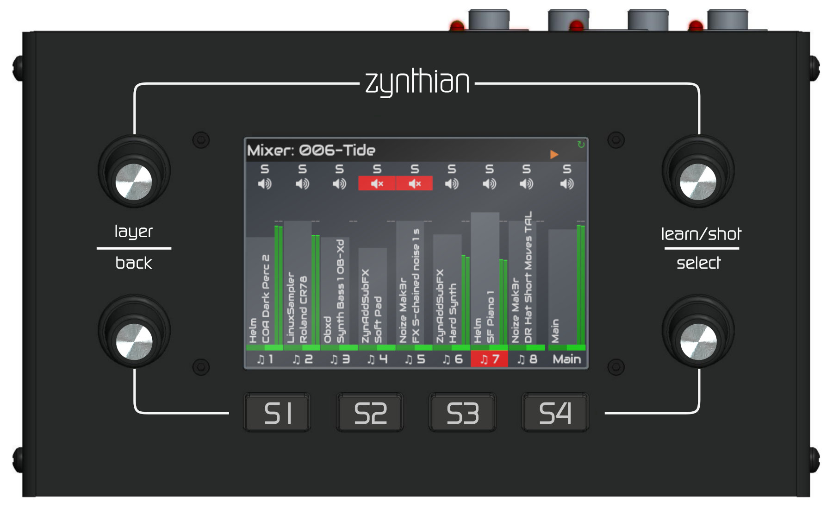
Aluminum - Zynscreen-v4/v4_render_zenital_mixer_tide.jpg
