zynthian/zynthian-case/Aluminum - Zynscreen-v4/zynthian_box_botones.png

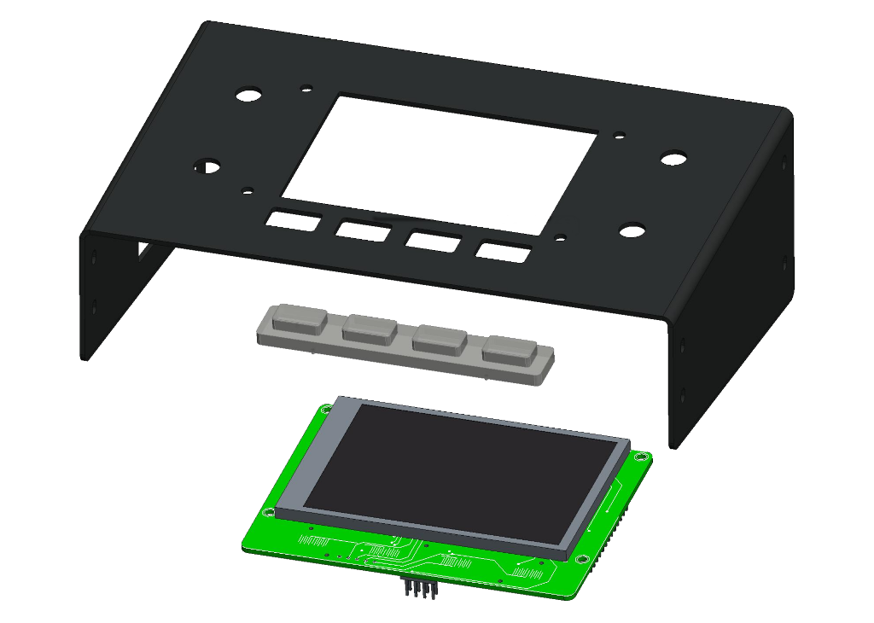
Aluminum - Zynscreen-v4/zynthian_box_botones.png
