zynthian/zynthian-case/Aluminum - Zynscreen-v4/zynthian_v4_alzado_planta_hr.png

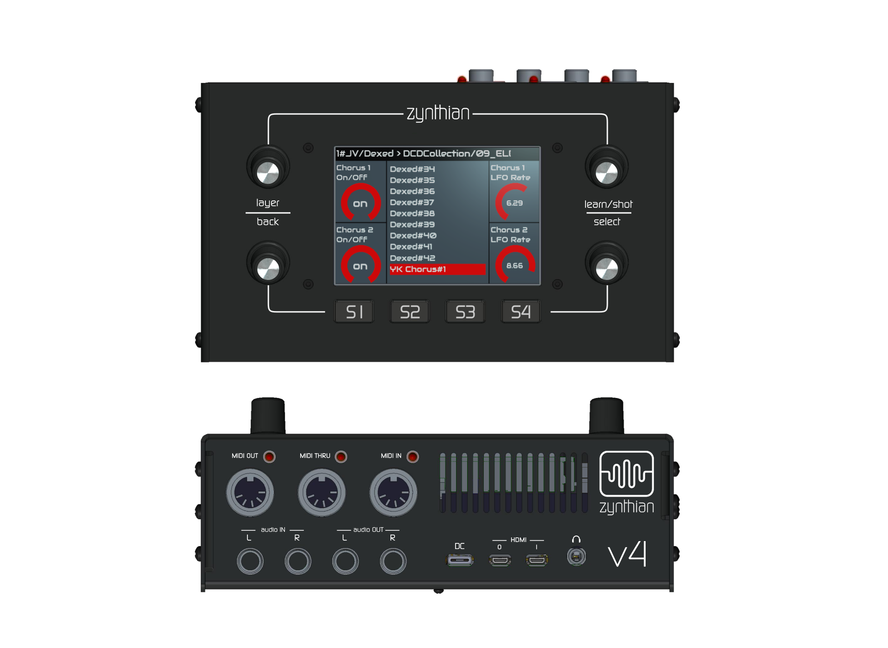
Aluminum - Zynscreen-v4/zynthian_v4_alzado_planta_hr.png
