zynthian/zynthian-case/Aluminum - Zynscreen-v4/zynthian_v4_desarrollo.png

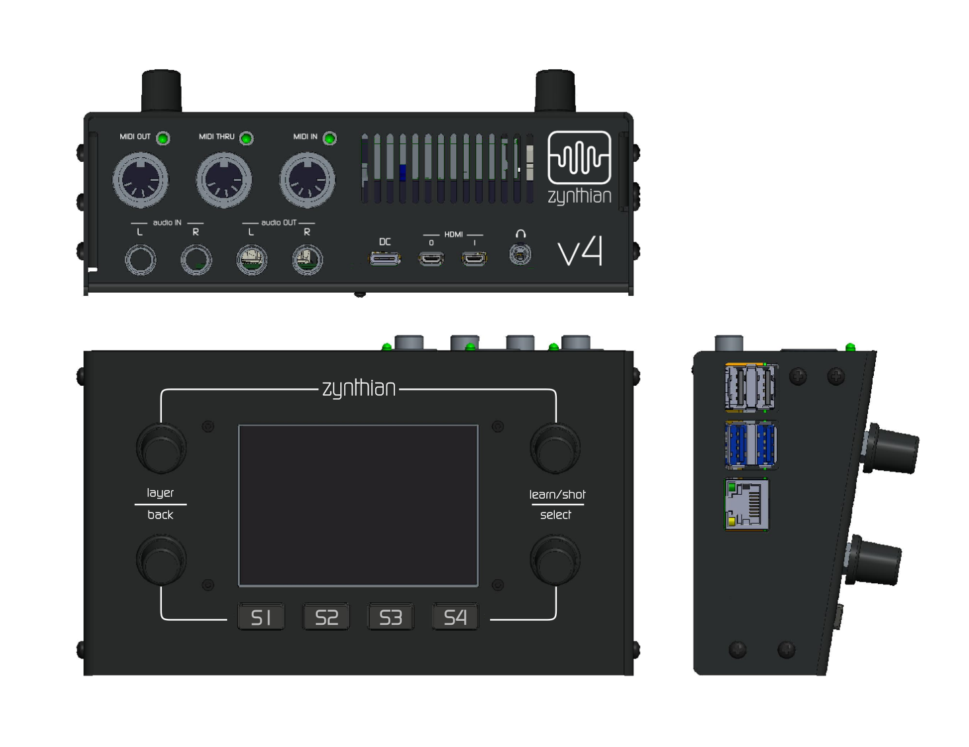
Aluminum - Zynscreen-v4/zynthian_v4_desarrollo.png
