zynthian/zynthian-case/Aluminum - Zynscreen-v4/zynthian_v4_desarrollo_hr.png

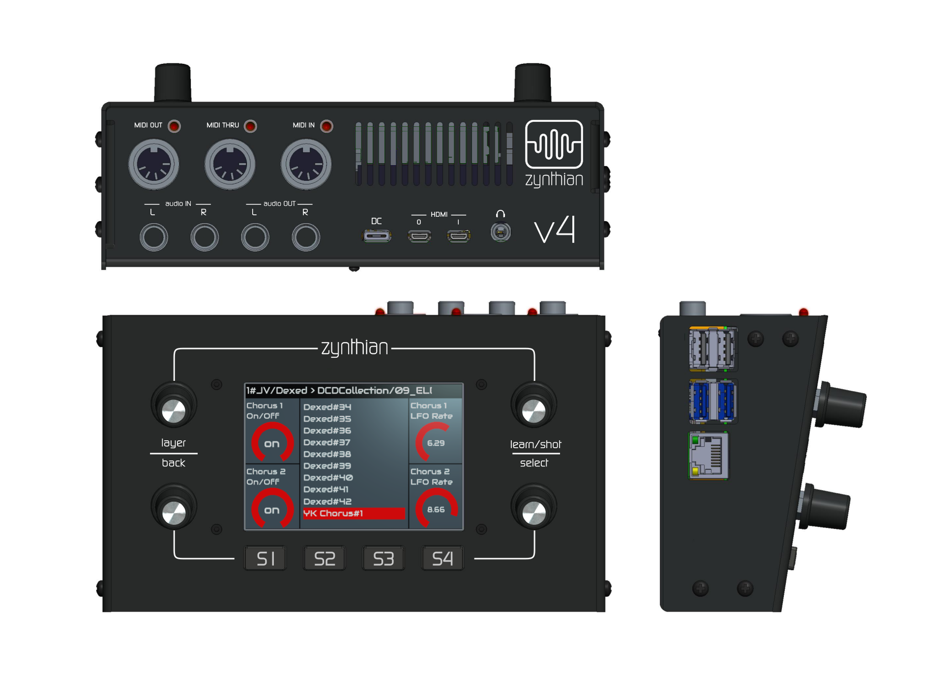
Aluminum - Zynscreen-v4/zynthian_v4_desarrollo_hr.png
