zynthian/zynthian-case/V5 - Aluminum/img/v5_aluminum_case_bottom.jpg

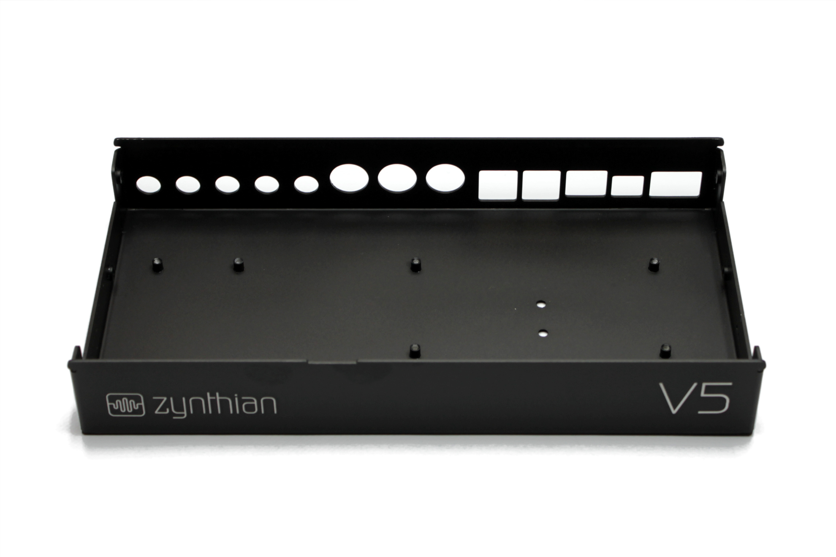
V5 - Aluminum/img/v5_aluminum_case_bottom.jpg
