zynthian/zynthian-case/V5 - Aluminum/img/v5_aluminum_case_top.jpg

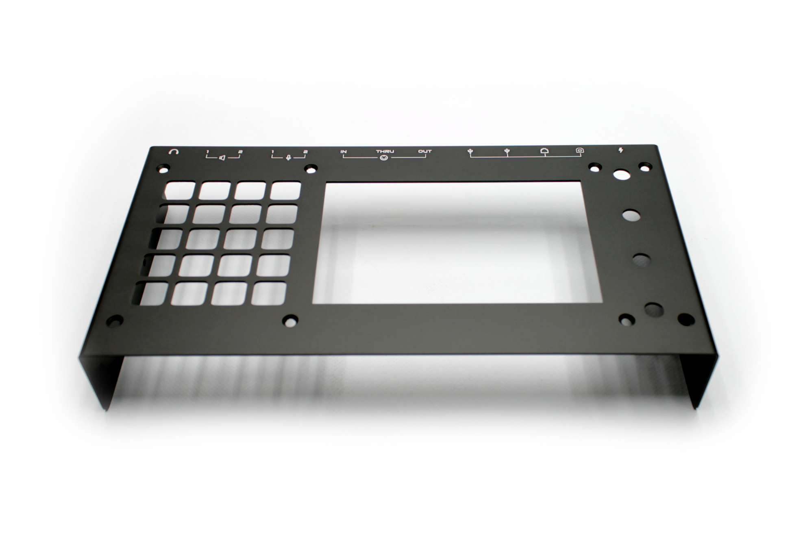
V5 - Aluminum/img/v5_aluminum_case_top.jpg
