zynthian/zynthian-case/V5 - Aluminum/img/V5_internals.png

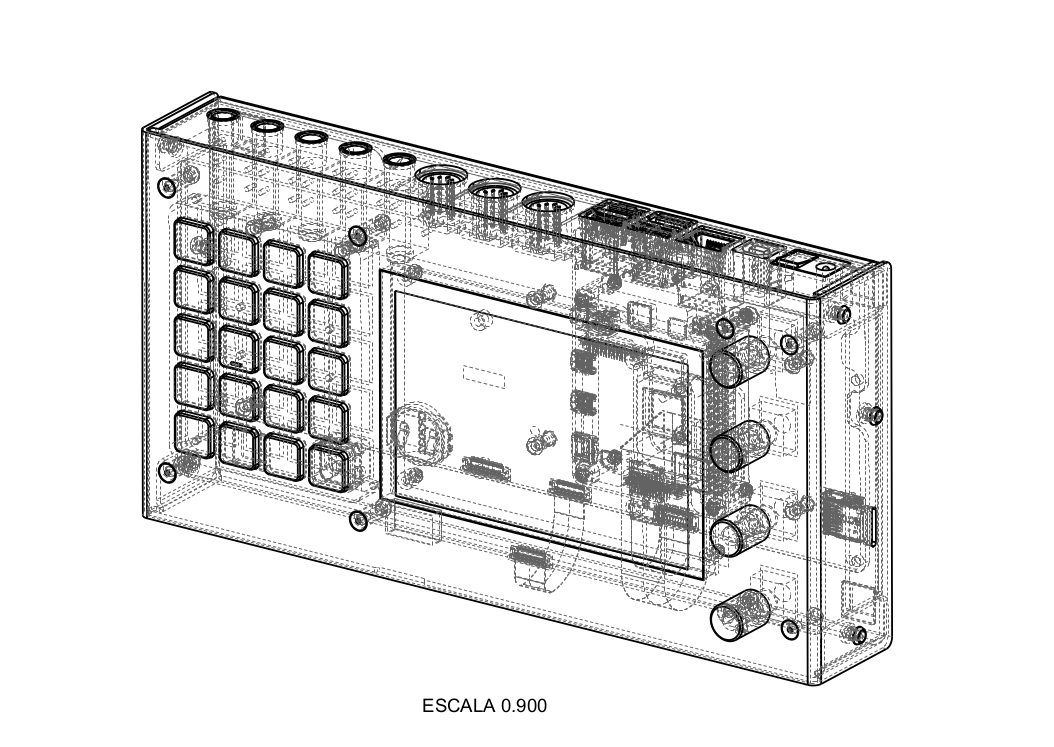
V5 - Aluminum/img/V5_internals.png
