zynthian/zynthian-case/V5 - Aluminum/img/v5_render_dramatico_mixer_leds_medium.jpg

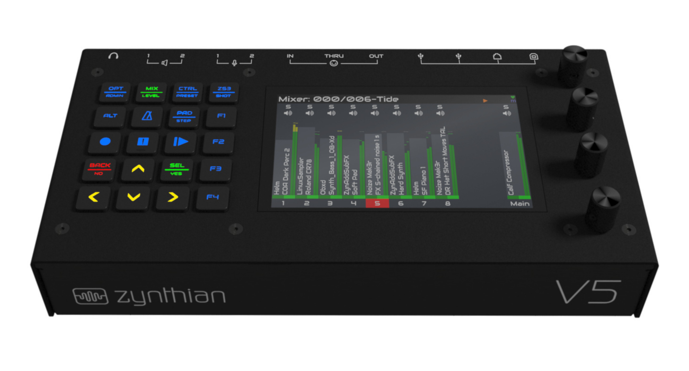
V5 - Aluminum/img/v5_render_dramatico_mixer_leds_medium.jpg
