zynthian/zynthian-case/V5 - Aluminum/img/v5_render_zenital_zynstep_leds_medium.jpg

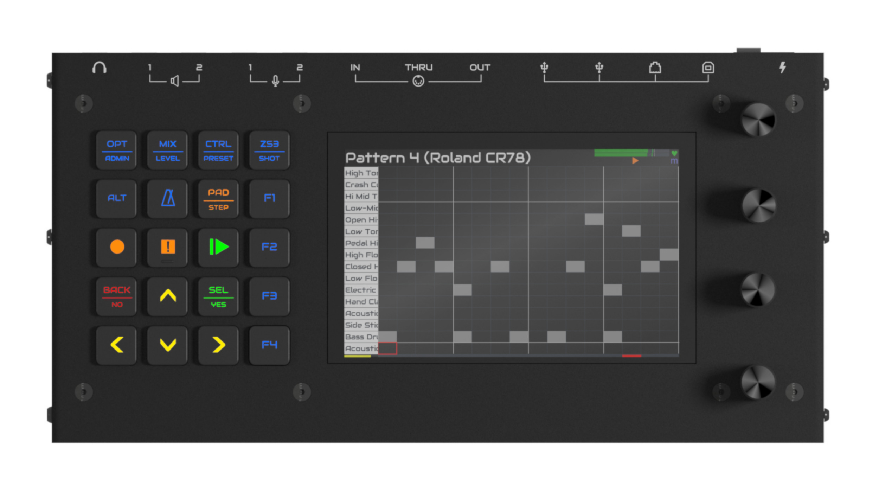
V5 - Aluminum/img/v5_render_zenital_zynstep_leds_medium.jpg
