zynthian/zynthian-case/3D Print - Mini V2/resources/case-assembly-parts.png

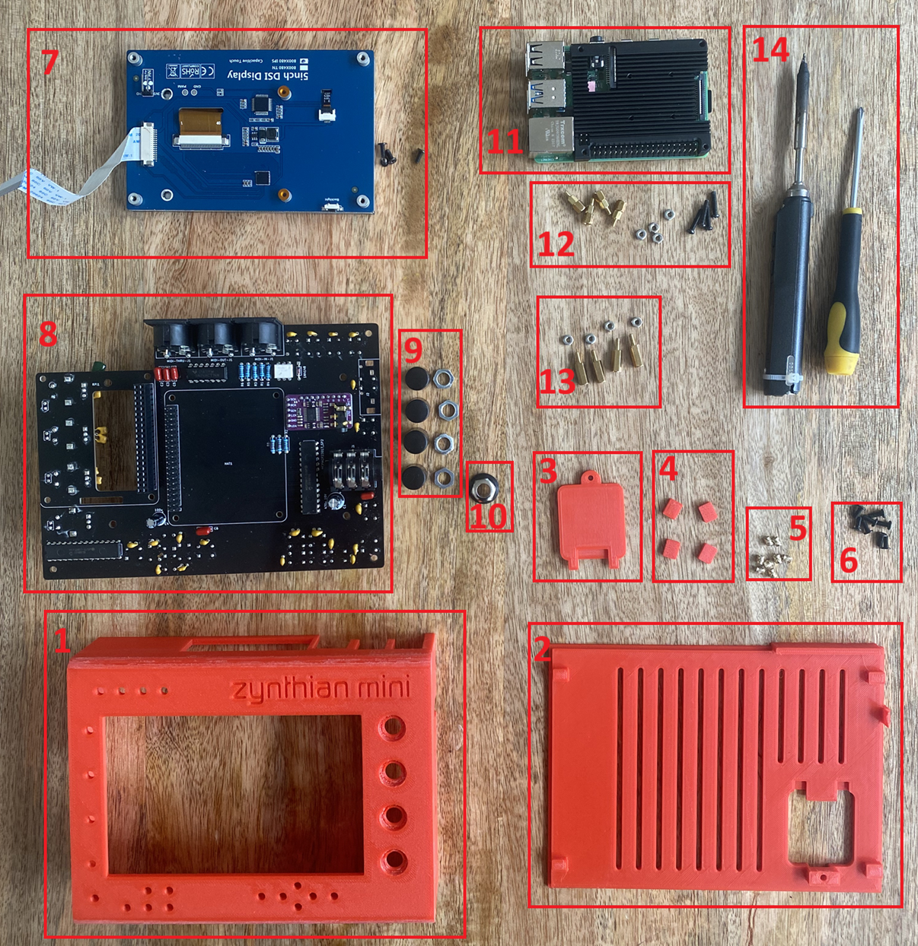
3D Print - Mini V2/resources/case-assembly-parts.png
