zynthian/zynthian-case/3D Print - Parts models/hifiberry-dac-1.snapshot.1/Hifiberry_DAC+_04.png

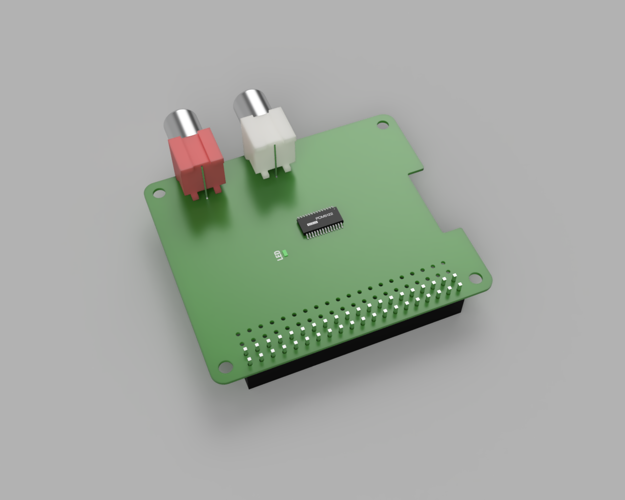
3D Print - Parts models/hifiberry-dac-1.snapshot.1/Hifiberry_DAC+_04.png
