zynthian/zynthian-case/Aluminum - Zynscreen-v4/rubber_buttons/ZYNT3.IGS

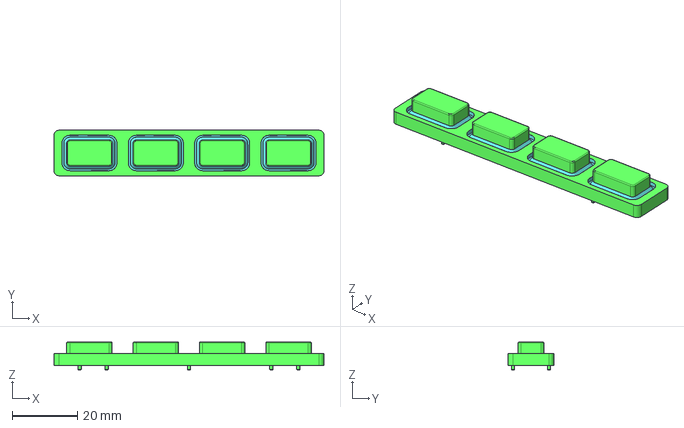
[picture p99: CAD file, 2020-08-05]
Aluminum - Zynscreen-v4/rubber_buttons/ZYNT3.IGS
83.0 x 14.0 x 8.60 mm
