zynthian/zynthian-case/laser-cutter-audioinjector/slopes/zynthian_box_lasser_cutter_all.dxf

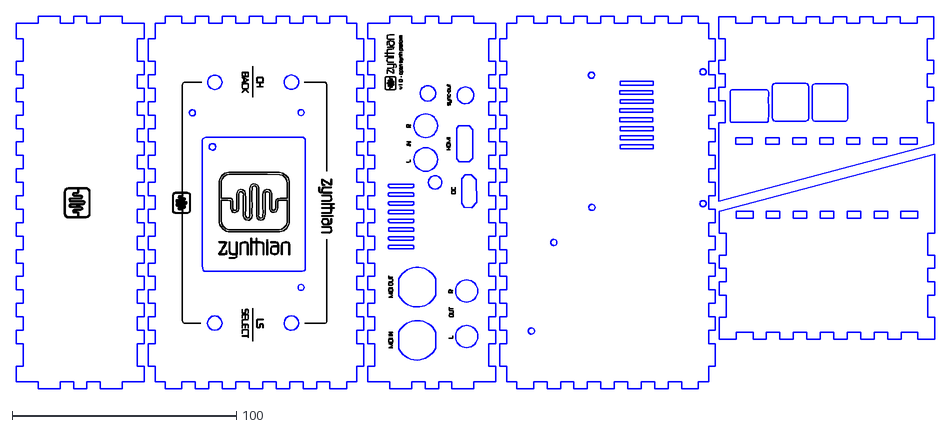
[picture p100: CAD file, 2017-05-02]
laser-cutter-audioinjector/slopes/zynthian_box_lasser_cutter_all.dxf
409.5 x 166.0
