zynthian/zynthian-case/laser-cutter-audioinjector/zynthian_box_lasser_cutter_all.dxf

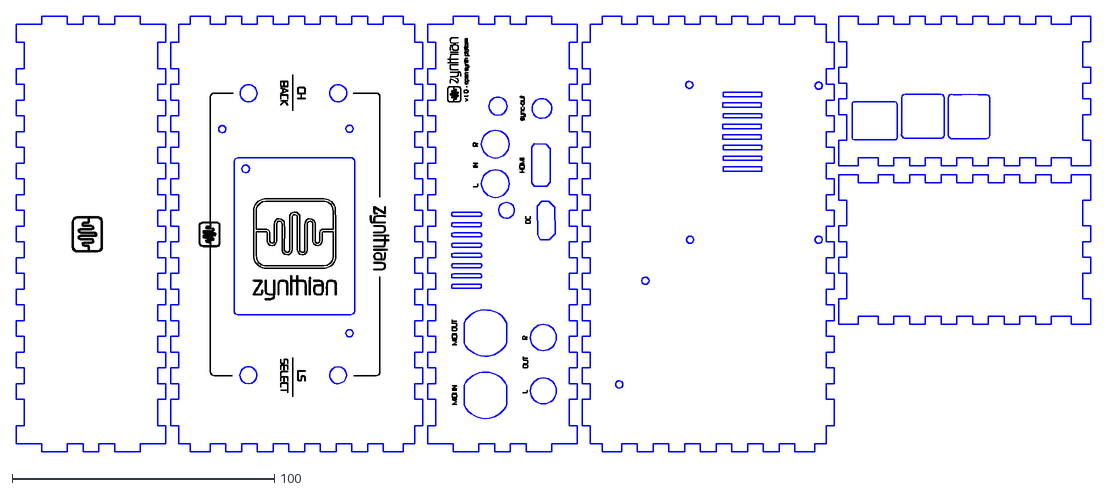
[picture p101: CAD file, 2017-04-04]
laser-cutter-audioinjector/zynthian_box_lasser_cutter_all.dxf
409.4 x 166.0
