zynthian/zynthian-case/laser-cutter/slopes/zynthian_box_lasser_cutter_all.dxf

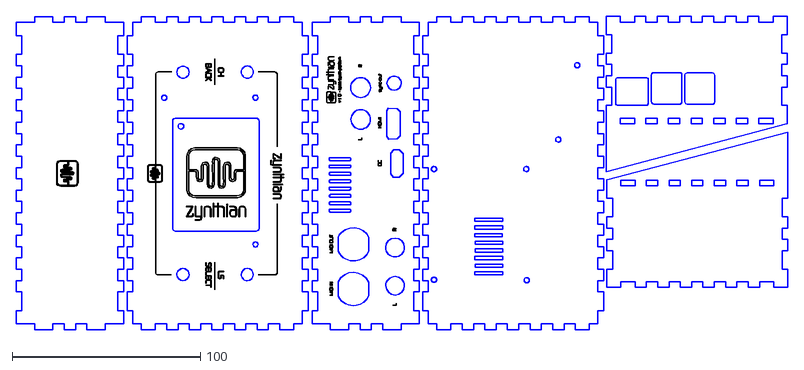
[picture p102: CAD file, 2017-05-02]
laser-cutter/slopes/zynthian_box_lasser_cutter_all.dxf
409.4 x 166.2
