zynthian/zynthian-case/Lasercut - Custom RBPi4 + Zynscreen/Pi4_case_face.dxf

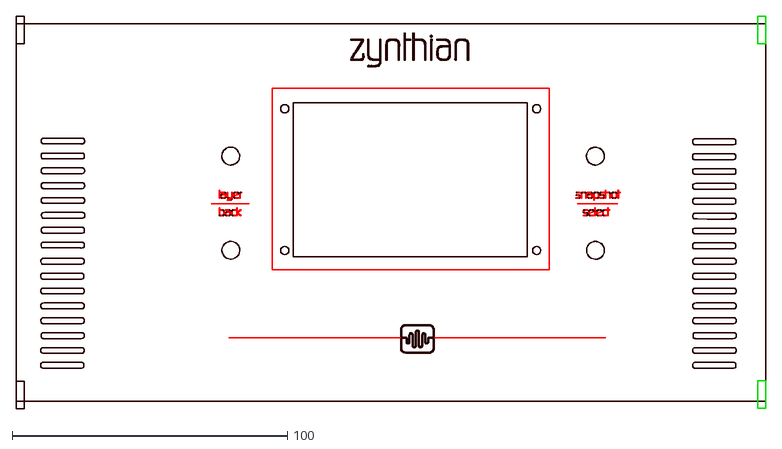
[picture p103: CAD file, 2020-01-10]
Lasercut - Custom RBPi4 + Zynscreen/Pi4_case_face.dxf
272.4 x 142.7
