zynthian/zynthian-case/Lasercut - PiTFT28/new_MIDI_connector/connectors/MIDI-hole2.dxf

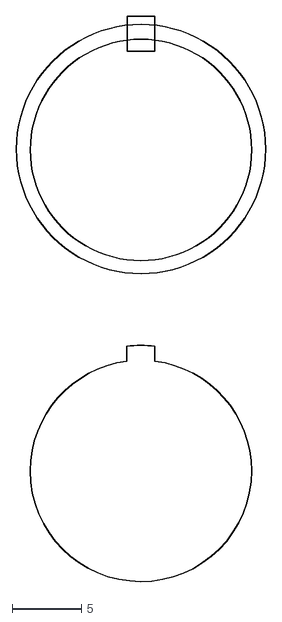
[picture p104: CAD file, 2017-09-29]
Lasercut - PiTFT28/new_MIDI_connector/connectors/MIDI-hole2.dxf
18.0 x 40.8
