zynthian/zynthian-case/Lasercut - PiTFT28/new_MIDI_connector/zynthian_box_hifiberry.dxf

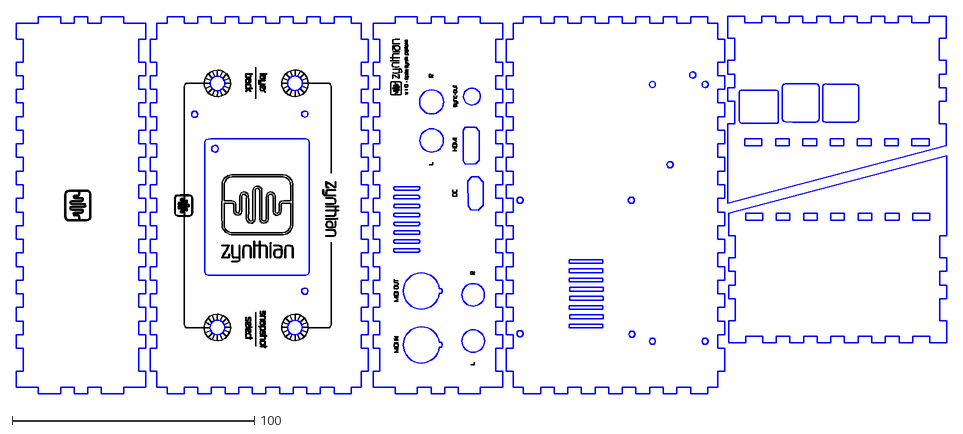
[picture p105: CAD file, 2019-09-04]
Lasercut - PiTFT28/new_MIDI_connector/zynthian_box_hifiberry.dxf
383.8 x 155.8
