zynthian/zynthian-case/Steel - PiTFT28/PaulFaldutoBox-CNC-rev.1.dxf

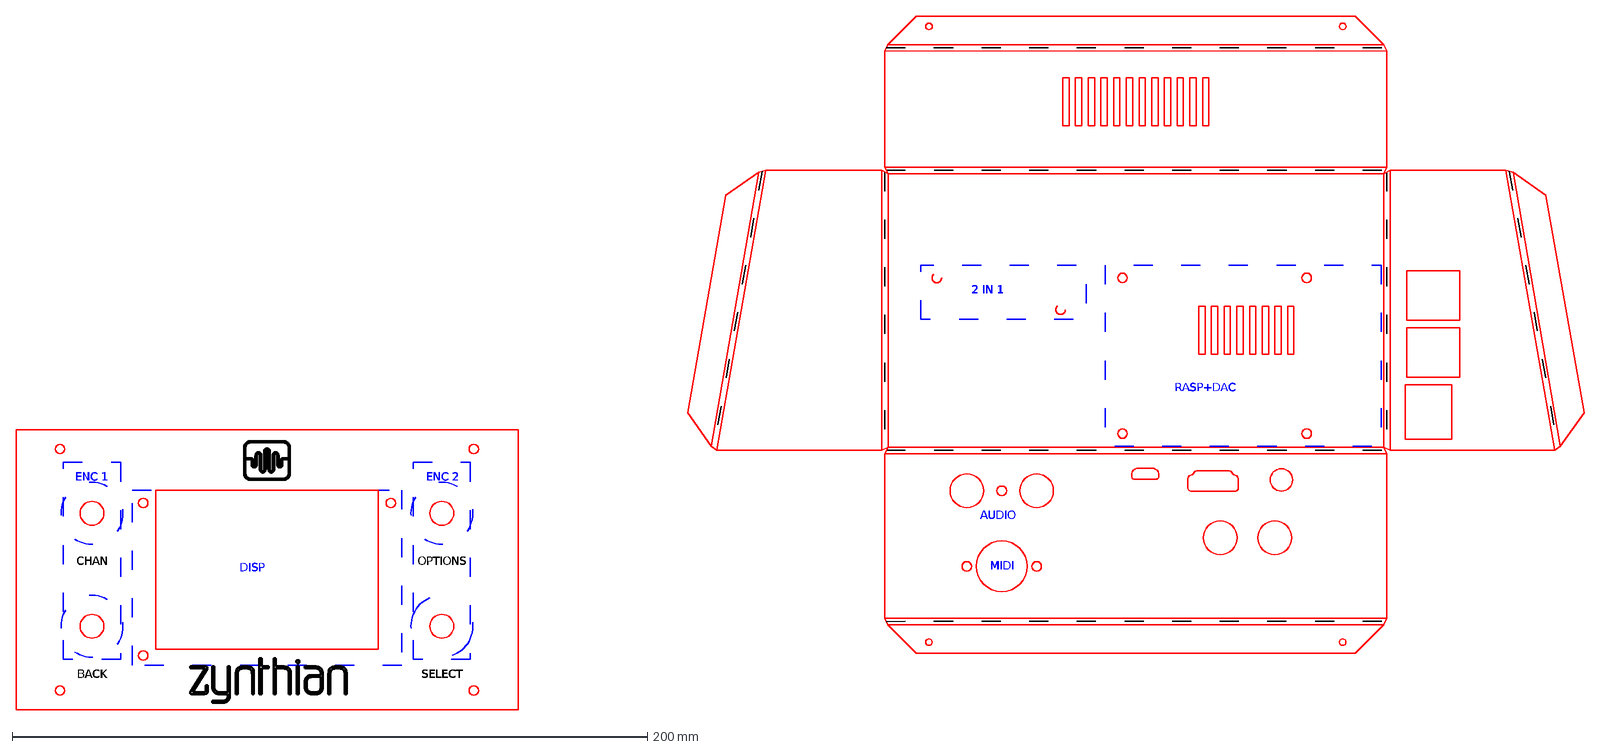
[picture p106: CAD file, 2016-09-21]
Steel - PiTFT28/PaulFaldutoBox-CNC-rev.1.dxf
ENC 1
ENC 2
DISP
RASP+DAC
2 IN 1
CHAN
BACK
OPTIONS
SELECT
AUDIO
MIDI
