zynthian/zynthian-case/Suitcase/suitcase.foam/ZynthianTop.stl

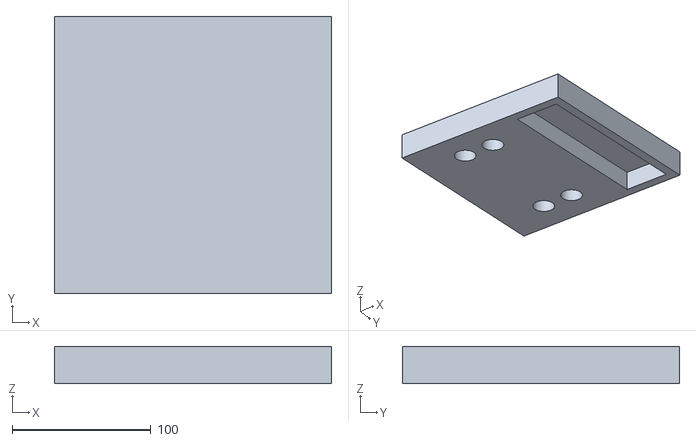
[picture p107: CAD file, 2019-09-04]
Suitcase/suitcase.foam/ZynthianTop.stl
200.0 x 200.0 x 27.0
