zynthian/zynthian-case/Suitcase/zynthianbottom.stl

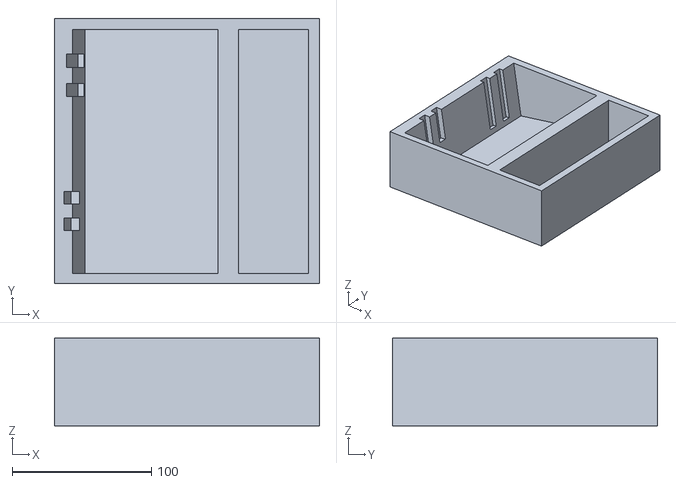
[picture p108: CAD file, 2020-08-05]
Suitcase/zynthianbottom.stl
190.0 x 190.0 x 63.0
