zynthian/zynthian-case/V5 - Aluminum/Zynthian_V5_BENDED_TOP_INSERTS-230508.stp

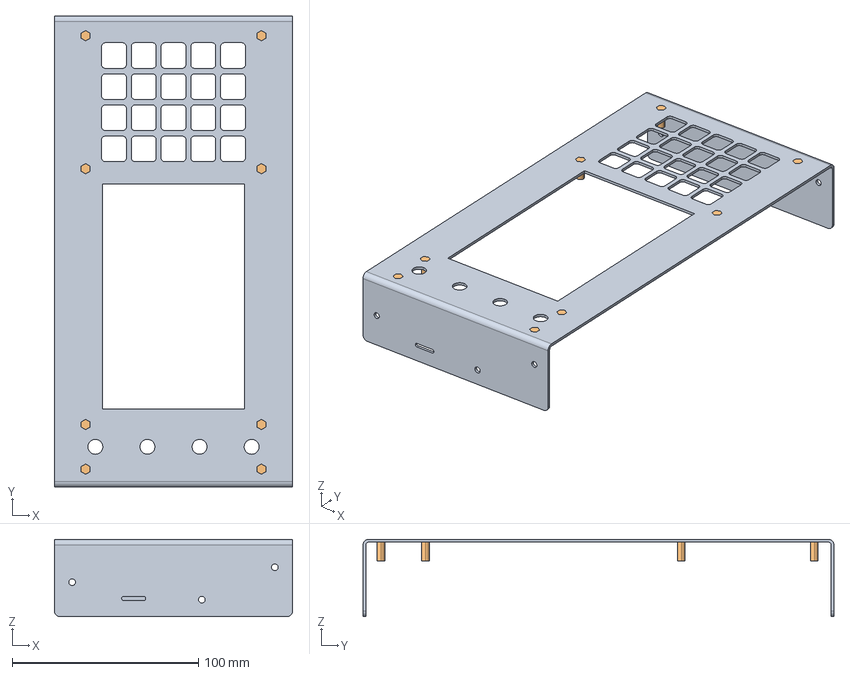
[picture p109: CAD file, 2023-07-19]
V5 - Aluminum/Zynthian_V5_BENDED_TOP_INSERTS-230508.stp
128.0 x 253.2 x 41.5 mm
Z2_LITTLECASE_BEND_COV_INSERTOS
FIXI_15CFBSOSM3_11_5 x 8
