zynthian/zynthian-case/3D Print - Big/Rpi SUPPORT.stl

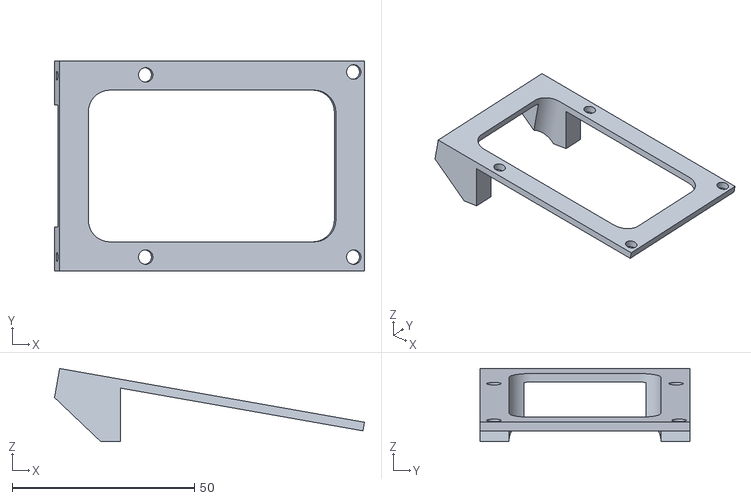
[picture p110: CAD file, 2017-04-04]
3D Print - Big/Rpi SUPPORT.stl
85.1 x 57.6 x 20.0
