zynthian/zynthian-case/3D Print - Lafranco/Fianco SX.stl

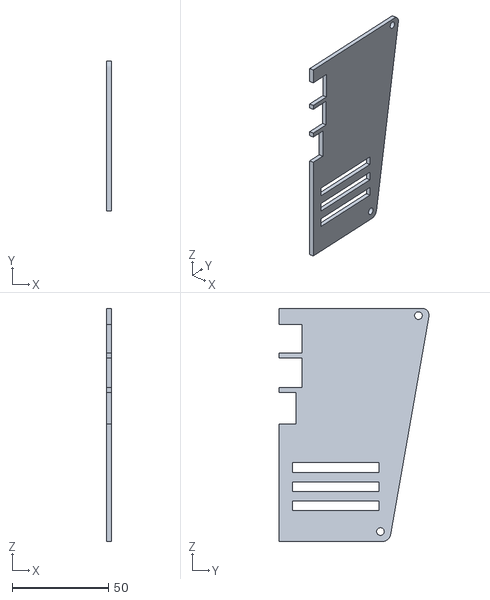
[picture p111: CAD file, 2023-07-19]
3D Print - Lafranco/Fianco SX.stl
2.60 x 78.0 x 121.2
