zynthian/zynthian-case/3D Print - Mini V2/leg.stl

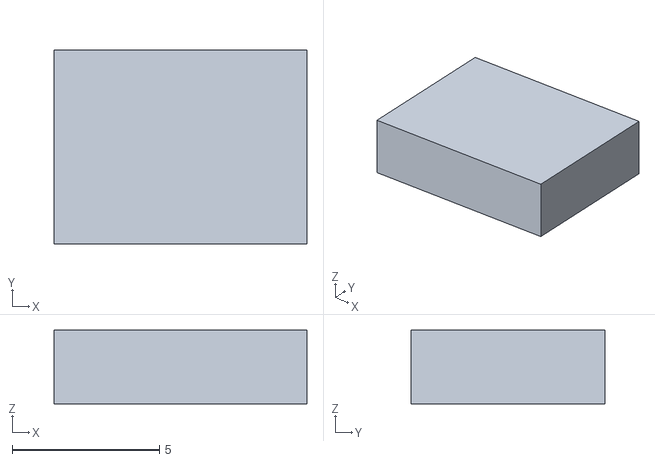
[picture p112: CAD file, 2024-05-14]
3D Print - Mini V2/leg.stl
8.60 x 6.60 x 2.50
