zynthian/zynthian-case/3D Print - Parts models/raspberry-pi-4-model-b-1.snapshot.3/Female USB Type C Connector, RPi4ModelB.SLDPRT

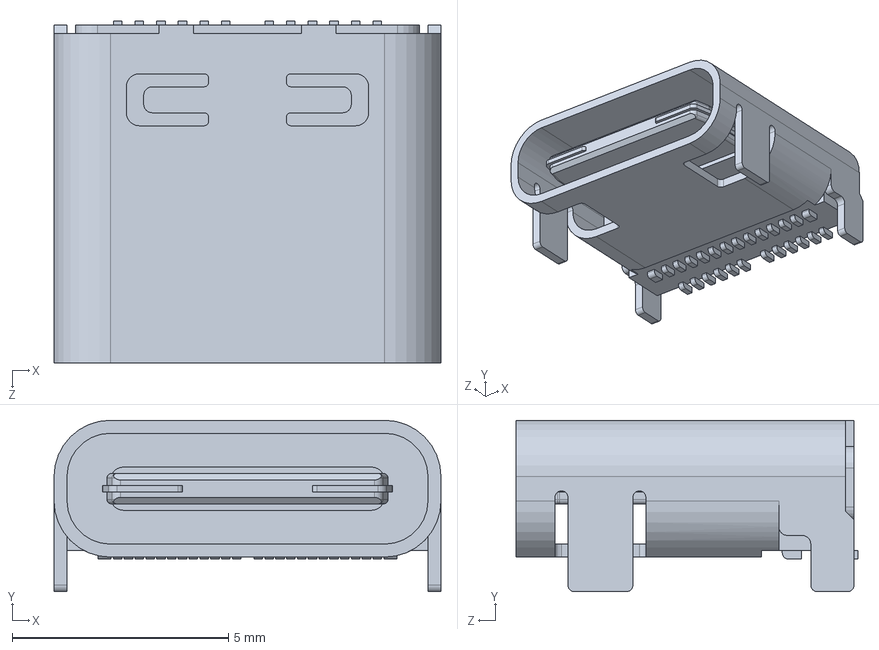
[picture p113: CAD file, 2019-09-04]
3D Print - Parts models/raspberry-pi-4-model-b-1.snapshot.3/Female USB Type C Connector, RPi4ModelB.SLDPRT
8.94 x 3.96 x 7.90 mm
