zynthian/zynthian-case/3D Print - PiScreen2 + 3xMIDI/zynthian_case_botton.FCStd

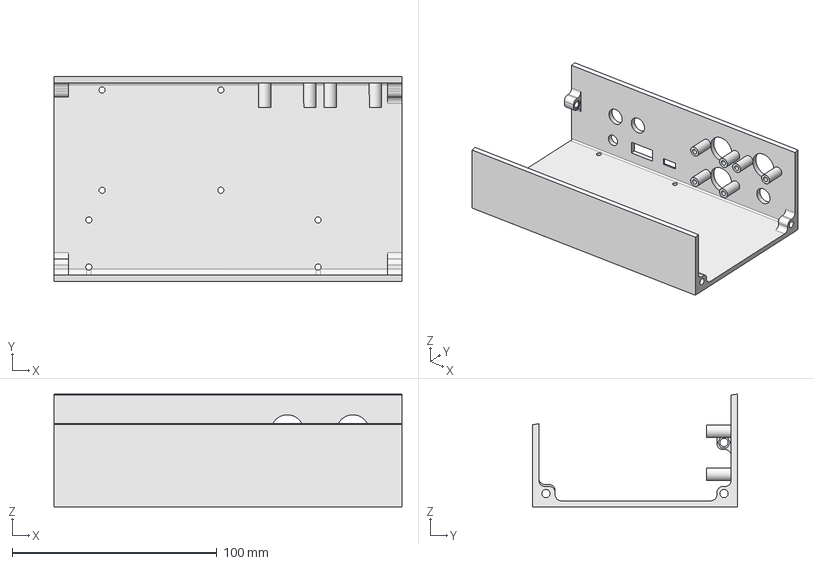
[picture p114: CAD file, 2019-09-04]
3D Print - PiScreen2 + 3xMIDI/zynthian_case_botton.FCStd
170.0 x 100.0 x 55.1 mm
