zynthian/zynthian-case/3D Print - Zynscreen 1.5 (V4)/STL files/Zynthian case back RPI4 HFB DAC+ADC.stl

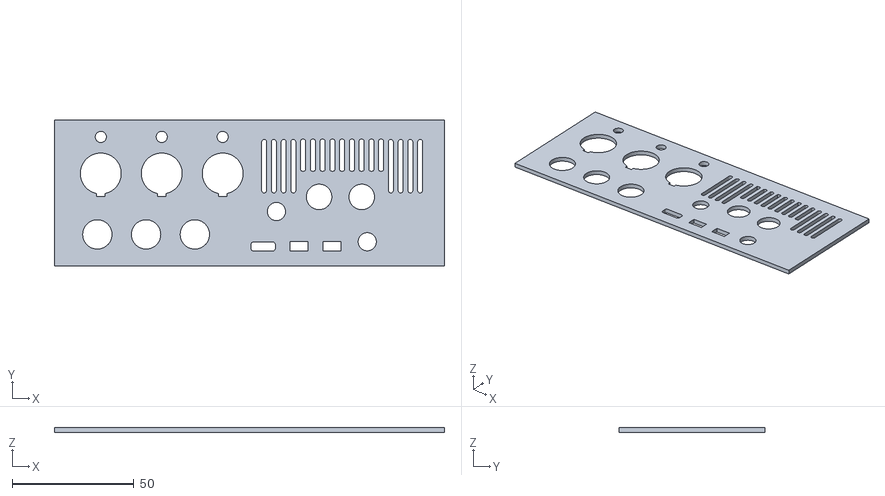
[picture p115: CAD file, 2023-07-19]
3D Print - Zynscreen 1.5 (V4)/STL files/Zynthian case back RPI4 HFB DAC+ADC.stl
160.0 x 60.0 x 2.00
