zynthian/zynthian-case/3D Print - Zynthian 4.3/File stl Case Zynthian/Fondo.stl

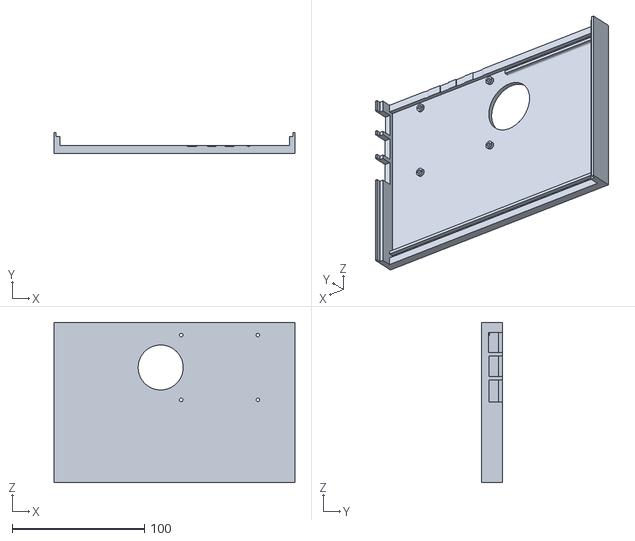
[picture p116: CAD file, 2023-07-19]
3D Print - Zynthian 4.3/File stl Case Zynthian/Fondo.stl
182.1 x 16.0 x 120.9
