zynthian/zynthian-case/3DPrint - PiScreen2/top-box.stl

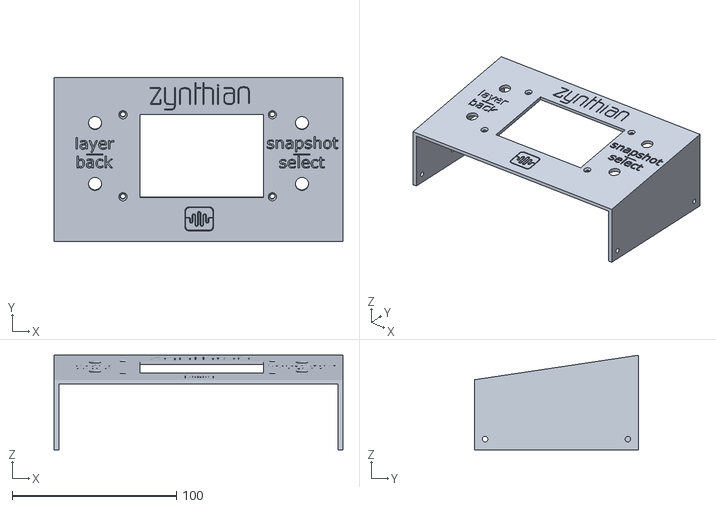
[picture p117: CAD file, 2018-02-07]
3DPrint - PiScreen2/top-box.stl
176.0 x 100.0 x 57.6
