zynthian/zynthian-case/3DPrint - Waveshare35/Zynthian_Front_v1.stl

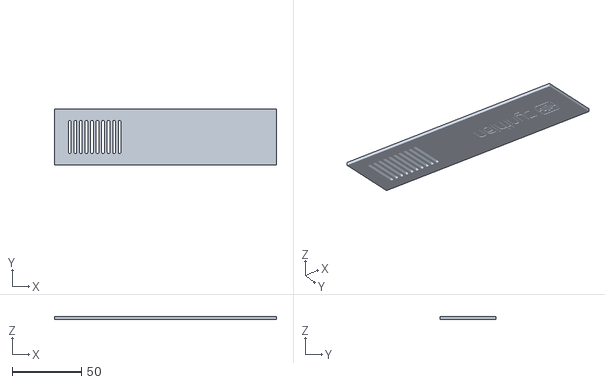
[picture p118: CAD file, 2020-08-05]
3DPrint - Waveshare35/Zynthian_Front_v1.stl
160.0 x 40.0 x 2.00
