zynthian/zynthian-case/3DPrint/zyn_box_down.stl

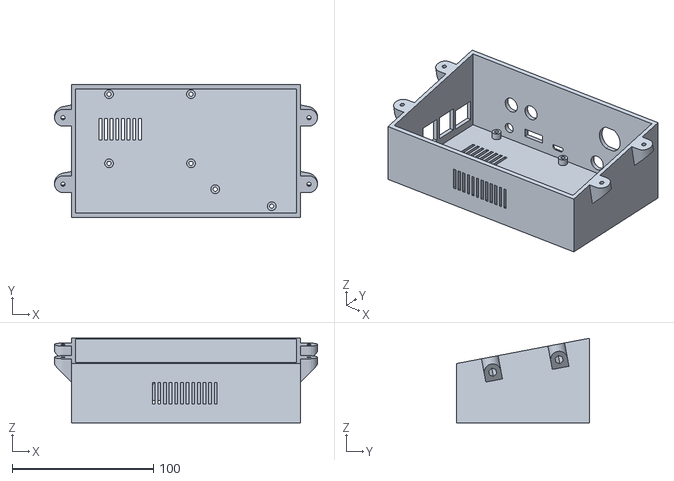
[picture p119: CAD file, 2016-10-03]
3DPrint/zyn_box_down.stl
186.3 x 94.2 x 59.9
