zynthian/zynthian-case/Aluminum - PiScreen-v2.2/zynthian_box_2p_v06.2_back_cutter.dxf

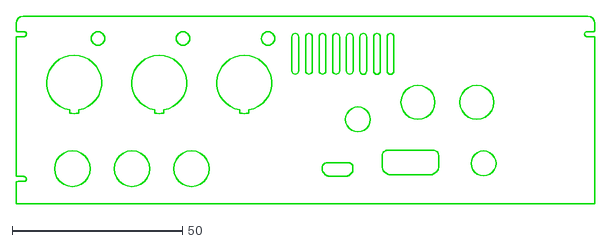
[picture p120: CAD file, 2019-09-04]
Aluminum - PiScreen-v2.2/zynthian_box_2p_v06.2_back_cutter.dxf
170.0 x 55.0
