zynthian/zynthian-case/Aluminum - Zynscreen-v4/rubber_buttons/zintian_box_FRONTAL_BOTONES_110520.stp

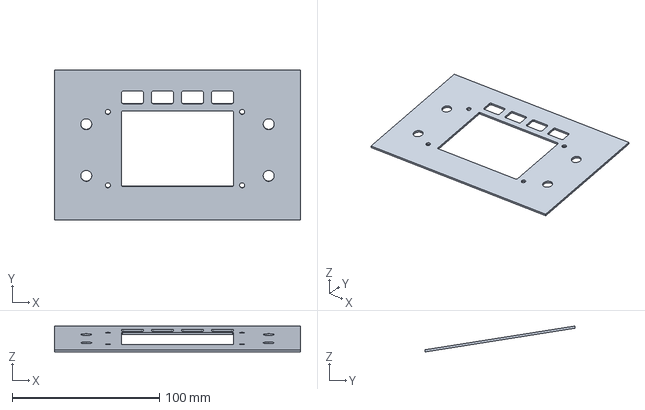
[picture p121: CAD file, 2020-08-05]
Aluminum - Zynscreen-v4/rubber_buttons/zintian_box_FRONTAL_BOTONES_110520.stp
167.2 x 102.2 x 17.6 mm
