zynthian/zynthian-case/laser-cutter-audioinjector/zynthian_box_lasser_cutter_partial1.dxf

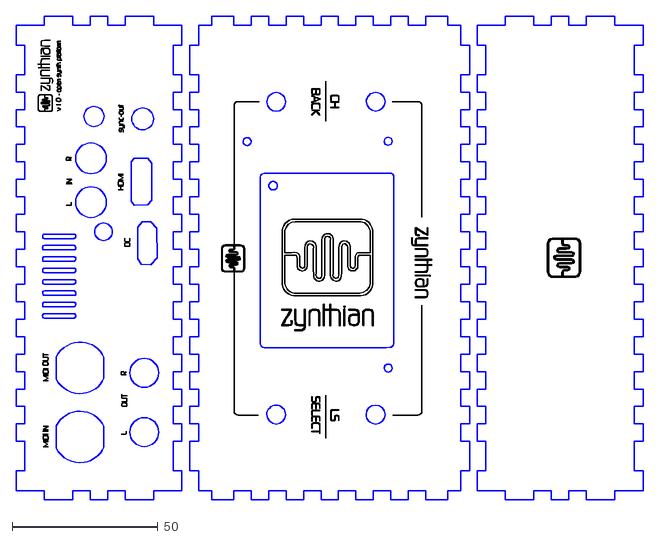
[picture p122: CAD file, 2017-04-04]
laser-cutter-audioinjector/zynthian_box_lasser_cutter_partial1.dxf
215.3 x 166.0
