zynthian/zynthian-case/laser-cutter/slopes/slopes.dxf

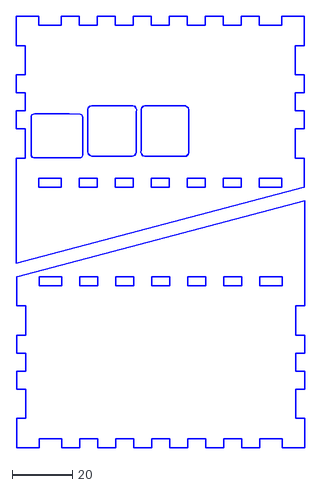
[picture p123: CAD file, 2017-05-02]
laser-cutter/slopes/slopes.dxf
96.3 x 143.8
