zynthian/zynthian-case/Lasercut - Custom RBPi4 + Zynscreen/Pi4_case_magnet_holders.stl

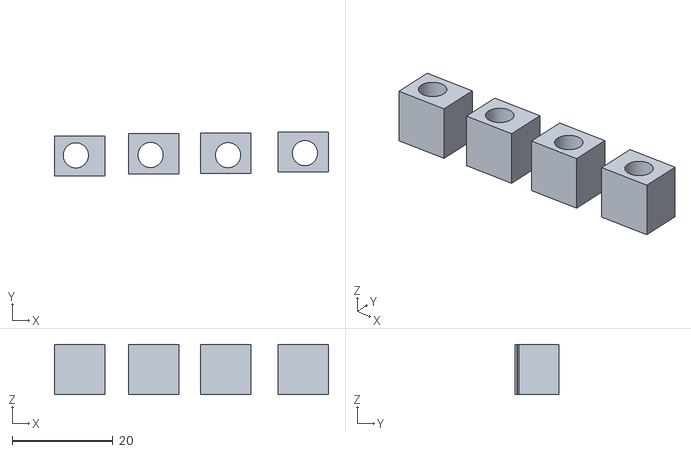
[picture p124: CAD file, 2020-01-10]
Lasercut - Custom RBPi4 + Zynscreen/Pi4_case_magnet_holders.stl
54.4 x 8.78 x 10.0
