zynthian/zynthian-case/Lasercut - PiTFT28/new_MIDI_connector/connectors/MIDI-hole.dxf

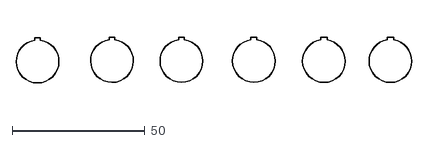
[picture p125: CAD file, 2017-09-29]
Lasercut - PiTFT28/new_MIDI_connector/connectors/MIDI-hole.dxf
149.0 x 17.3
