zynthian/zynthian-case/Lasercut - PiTFT28/new_MIDI_connector/zynthian_box_audioinjector.dxf

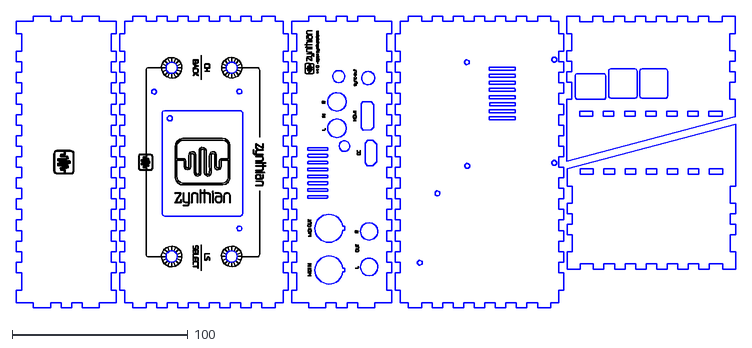
[picture p126: CAD file, 2017-12-11]
Lasercut - PiTFT28/new_MIDI_connector/zynthian_box_audioinjector.dxf
409.3 x 165.9
