zynthian/zynthian-case/Suitcase/suitcase.foam/ZynthianBottom.stl

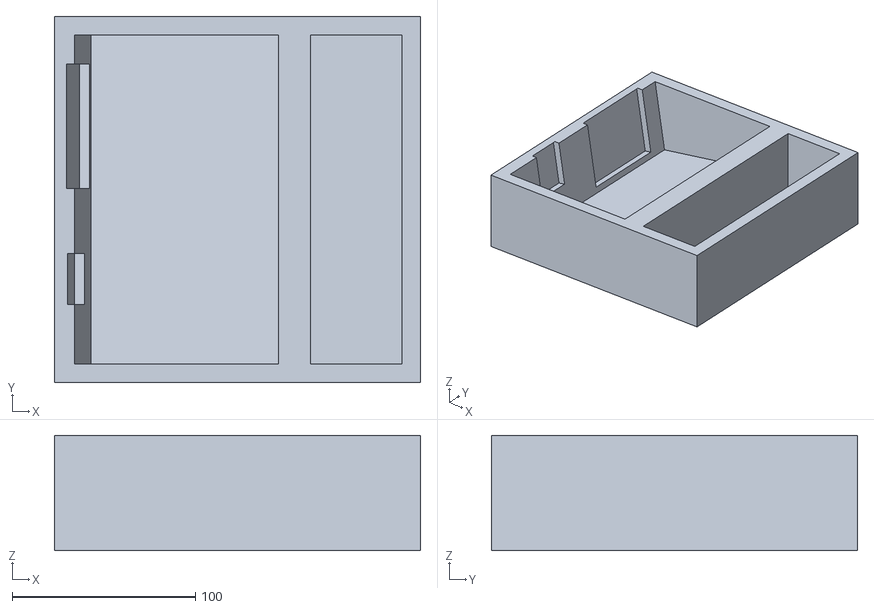
[picture p127: CAD file, 2019-09-04]
Suitcase/suitcase.foam/ZynthianBottom.stl
200.0 x 200.0 x 63.0
