zynthian/zynthian-case/Suitcase/ZynthianFOAM - Final.fcstd

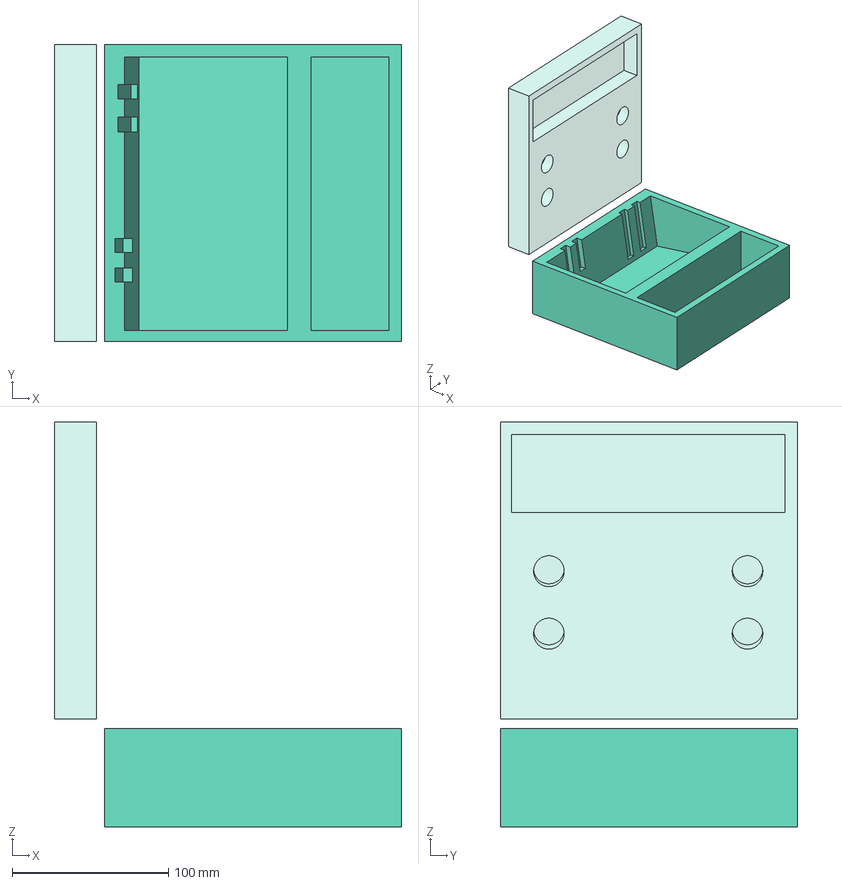
[picture p128: CAD file, 2020-08-05]
Suitcase/ZynthianFOAM - Final.fcstd
222.0 x 190.0 x 259.0 mm
FoamTOP
FoamBOTTOM001
DWire
