zynthian/zynthian-case/V5 - Aluminum/Zynthian_V5_BENDED_CASE-230313.stp

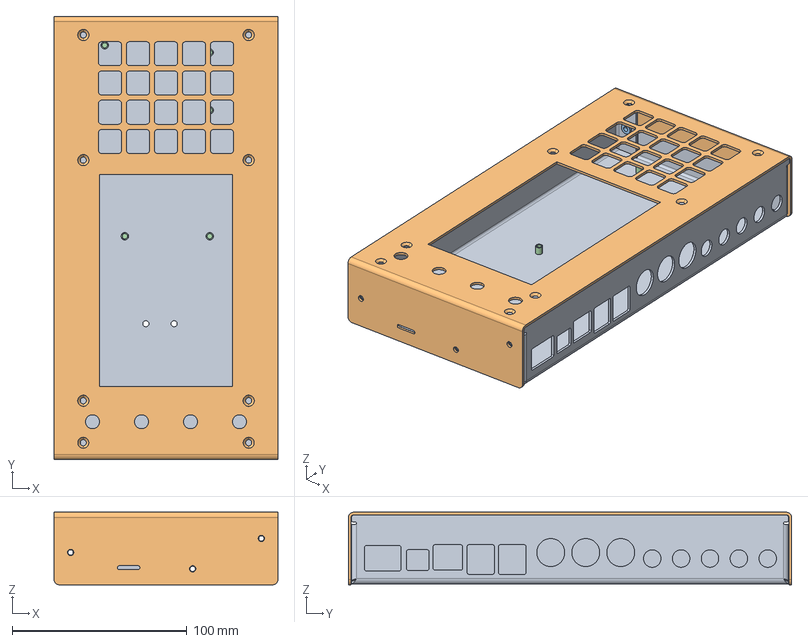
[picture p129: CAD file, 2023-07-19]
V5 - Aluminum/Zynthian_V5_BENDED_CASE-230313.stp
128.0 x 253.2 x 41.5 mm
Z2_LITTLECASE_BEND_BASE
Z2_LITTLECASE_BEND_COVER
BOLLHOFF_562_33_330_201 x 6
FIXI_15CFBSOSM3_06 x 7
