zynthian/zynthian-case/3D Print - Big/Foot L.stl

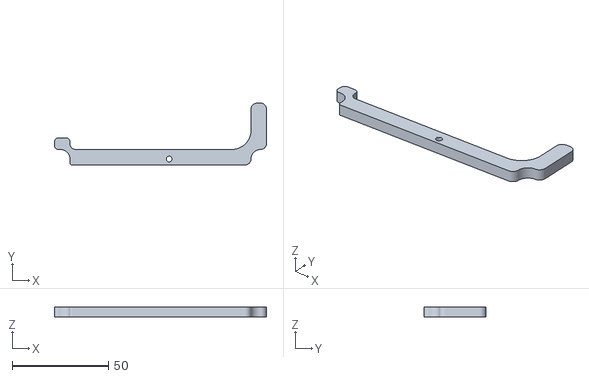
[picture p130: CAD file, 2017-04-04]
3D Print - Big/Foot L.stl
109.9 x 32.0 x 5.00
