zynthian/zynthian-case/3D Print - Lafranco/Frontale 4.3.stl

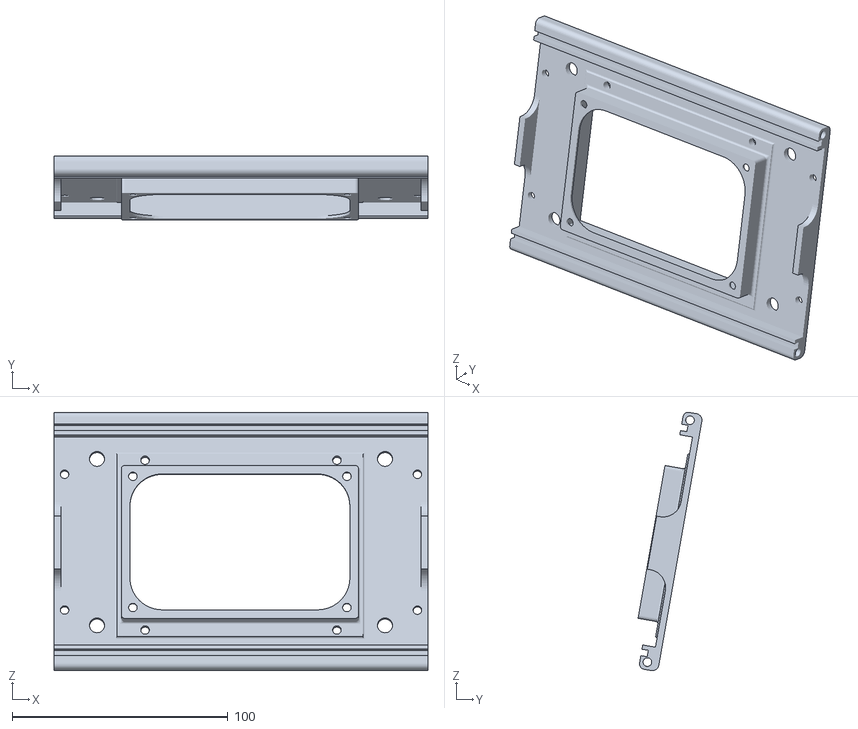
[picture p131: CAD file, 2023-07-19]
3D Print - Lafranco/Frontale 4.3.stl
173.5 x 29.7 x 119.8
