zynthian/zynthian-case/3D Print - Mini V2/bottom.stl

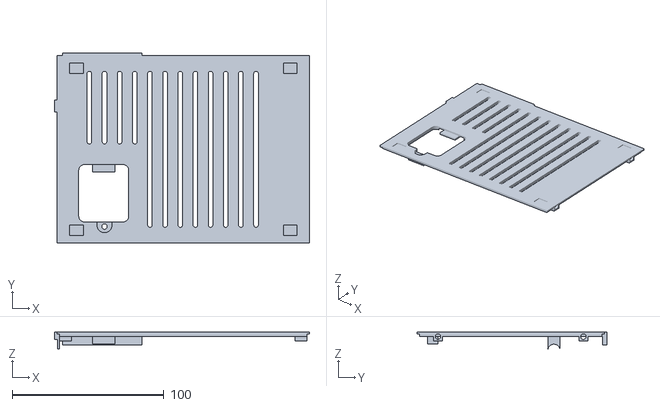
[picture p132: CAD file, 2024-05-14]
3D Print - Mini V2/bottom.stl
168.3 x 125.3 x 11.1
