zynthian/zynthian-case/3D Print - Parts models/raspberry-pi-4-model-b-1.snapshot.3/2.54 mm DUPONT MALE PIN HEADER, POE, 2X2, RPi4ModelB.SLDPRT

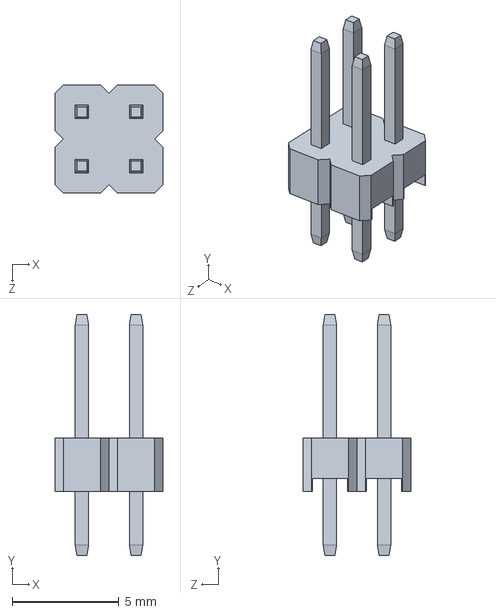
[picture p133: CAD file, 2019-09-04]
3D Print - Parts models/raspberry-pi-4-model-b-1.snapshot.3/2.54 mm DUPONT MALE PIN HEADER, POE, 2X2, RPi4ModelB.SLDPRT
5.08 x 11.3 x 5.08 mm
