zynthian/zynthian-case/3DPrint - Waveshare35/Zynthian_Bottom_v1.stl

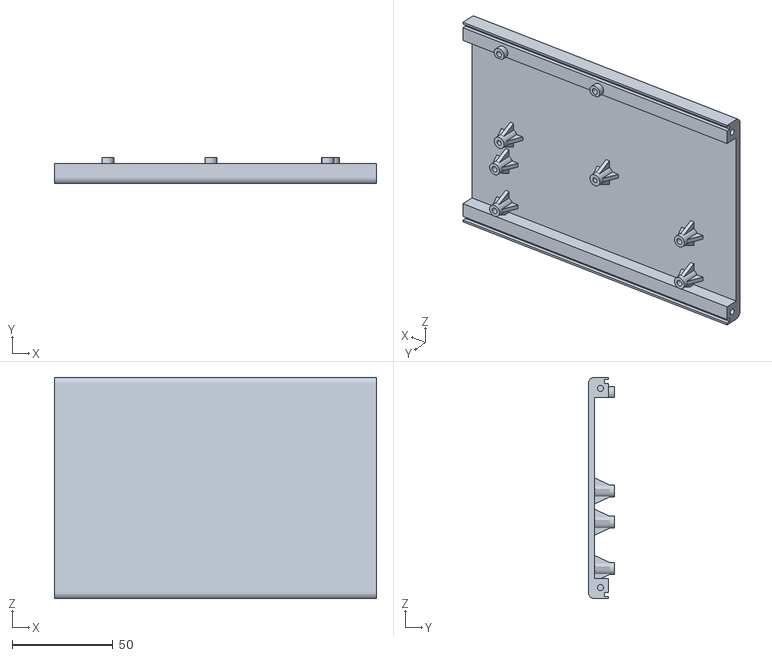
[picture p134: CAD file, 2020-08-05]
3DPrint - Waveshare35/Zynthian_Bottom_v1.stl
160.0 x 13.0 x 110.0
