zynthian/zynthian-case/3DPrint/moog_style_knob.stl

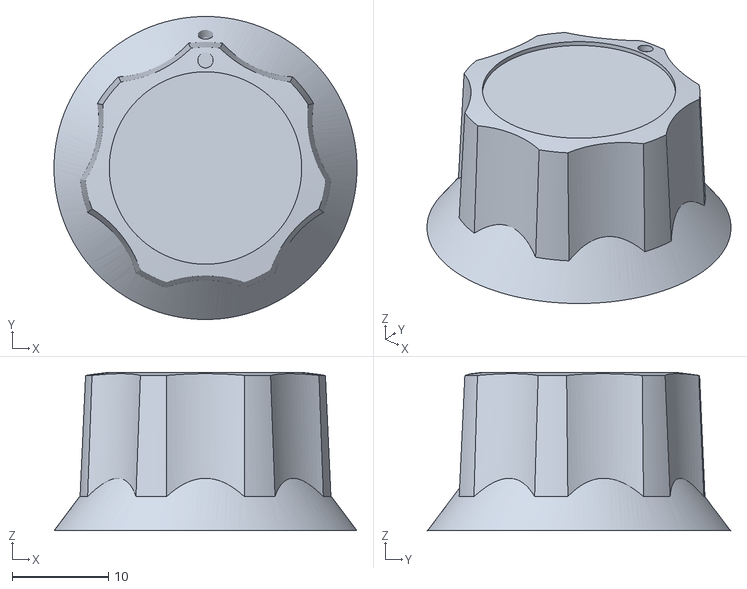
[picture p135: CAD file, 2016-09-21]
3DPrint/moog_style_knob.stl
31.5 x 31.5 x 16.5
