zynthian/zynthian-case/Aluminum - PiScreen-v2.2/zintian_box_base_v6.2.stl

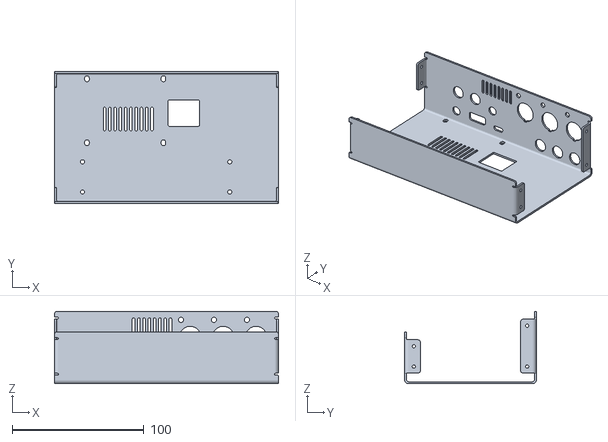
[picture p136: CAD file, 2019-09-04]
Aluminum - PiScreen-v2.2/zintian_box_base_v6.2.stl
170.0 x 100.0 x 55.0
