zynthian/zynthian-case/Aluminum - Zynscreen-v4/rubber_buttons/zynscreen_v1_5_110520.stp

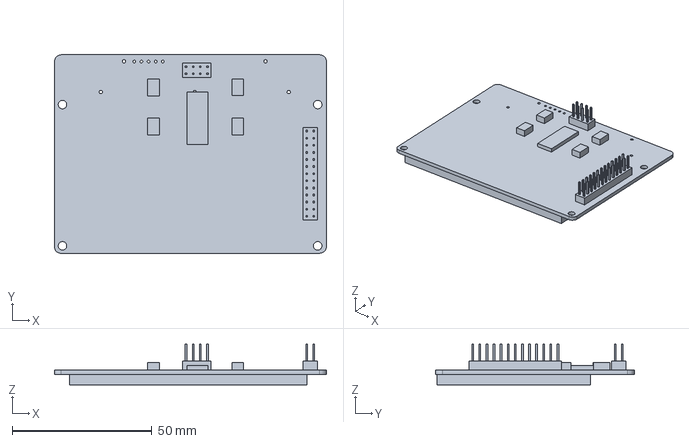
[picture p137: CAD file, 2020-08-05]
Aluminum - Zynscreen-v4/rubber_buttons/zynscreen_v1_5_110520.stp
97.2 x 71.0 x 14.7 mm
