zynthian/zynthian-case/laser-cutter-audioinjector/zynthian_box_lasser_back.dxf

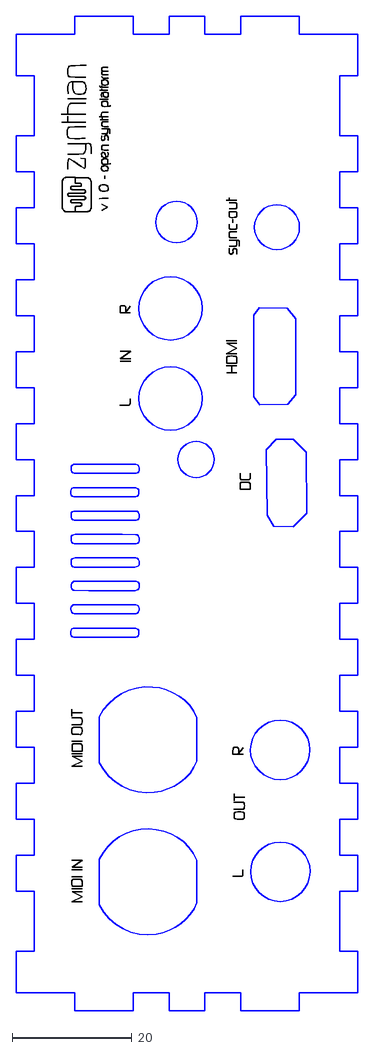
[picture p138: CAD file, 2017-04-04]
laser-cutter-audioinjector/zynthian_box_lasser_back.dxf
57.0 x 166.0
