zynthian/zynthian-case/Lasercut - Custom RBPi4 + Zynscreen/Pi4_side_right_outer.dxf

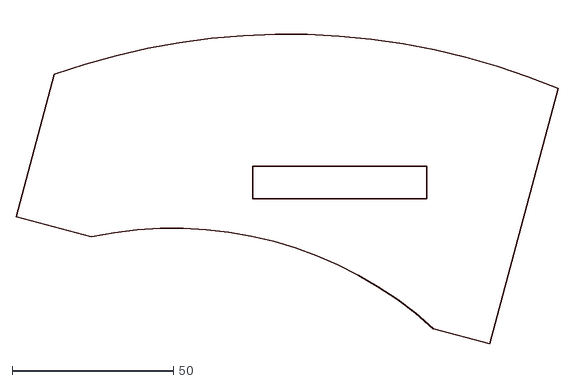
[picture p139: CAD file, 2020-01-10]
Lasercut - Custom RBPi4 + Zynscreen/Pi4_side_right_outer.dxf
168.0 x 101.5
