zynthian/zynthian-case/Suitcase/zynthiantop.stl

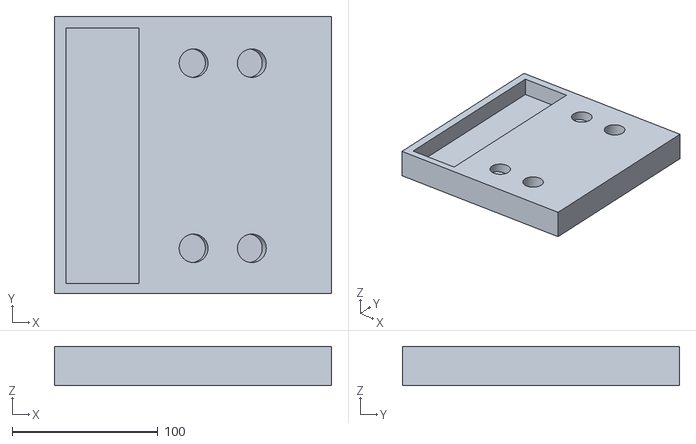
[picture p140: CAD file, 2020-08-05]
Suitcase/zynthiantop.stl
190.0 x 190.0 x 27.0
