zynthian/zynthian-case/V5 - Aluminum/Zynthian_V5_BENDED_BOTTOM-230313.stp

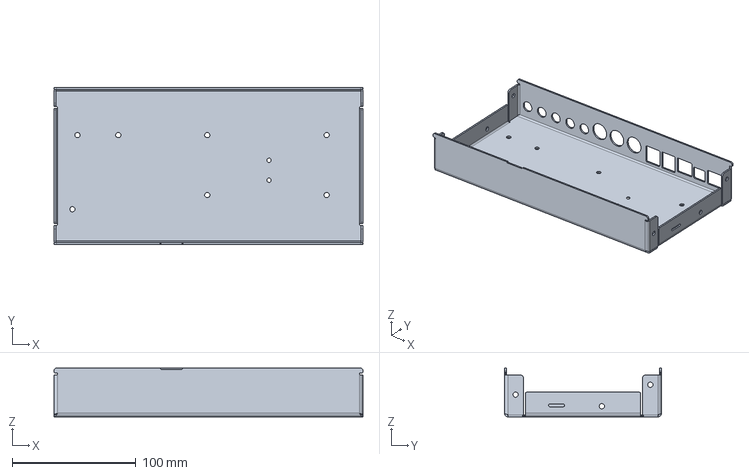
[picture p141: CAD file, 2023-07-19]
V5 - Aluminum/Zynthian_V5_BENDED_BOTTOM-230313.stp
250.0 x 127.0 x 39.5 mm
