zynthian/zynthian-case/3D Print - Big/Button.stl

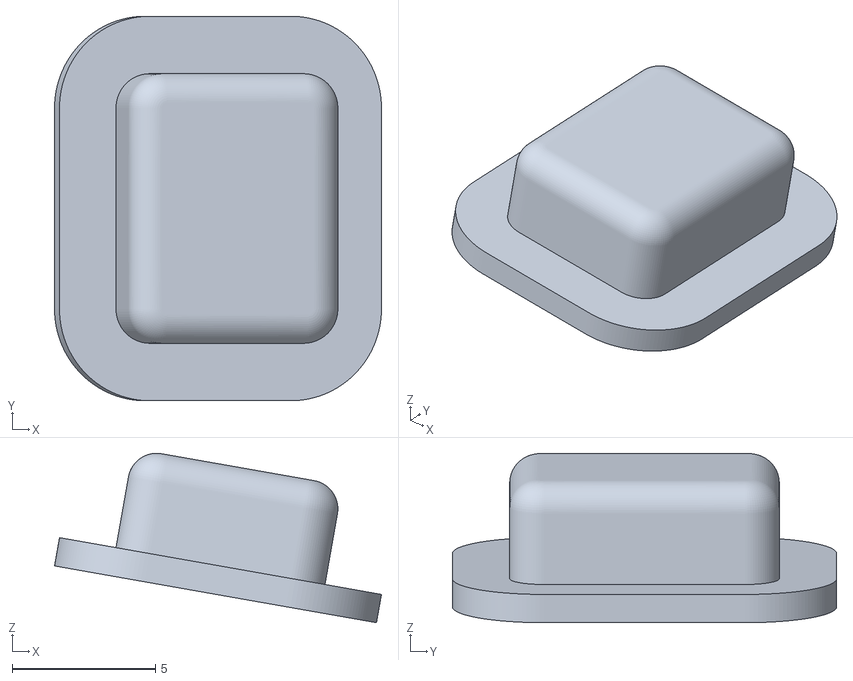
[picture p142: CAD file, 2017-04-04]
3D Print - Big/Button.stl
11.4 x 13.4 x 5.91
