zynthian/zynthian-case/3D Print - Parts models/raspberry-pi-4-model-b-1.snapshot.3/Female Micro HDMI Connector, RPi4ModelB.SLDPRT

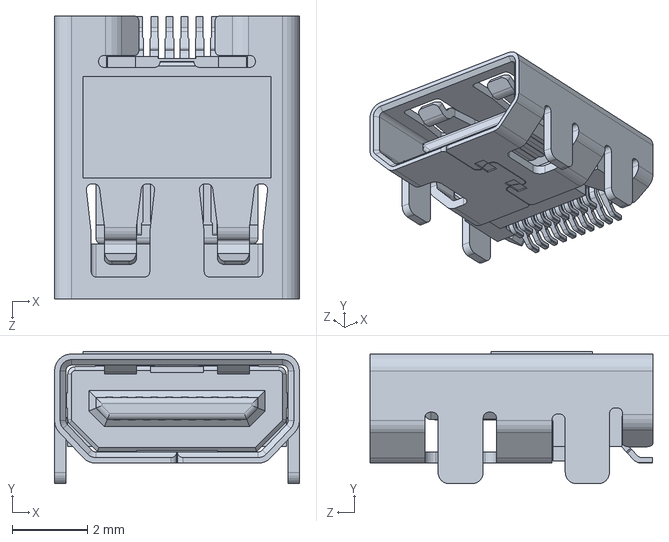
[picture p143: CAD file, 2019-09-04]
3D Print - Parts models/raspberry-pi-4-model-b-1.snapshot.3/Female Micro HDMI Connector, RPi4ModelB.SLDPRT
6.50 x 3.52 x 7.50 mm
