zynthian/zynthian-case/laser-cutter-audioinjector/zynthian_box_lasser_cutter_partial2.dxf

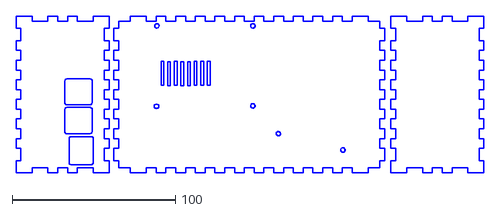
[picture p145: CAD file, 2017-03-06]
laser-cutter-audioinjector/zynthian_box_lasser_cutter_partial2.dxf
286.4 x 96.0
