zynthian/zynthian-case/Lasercut - Custom RBPi4 + Zynscreen/Pi4_case_bottom_v2.dxf

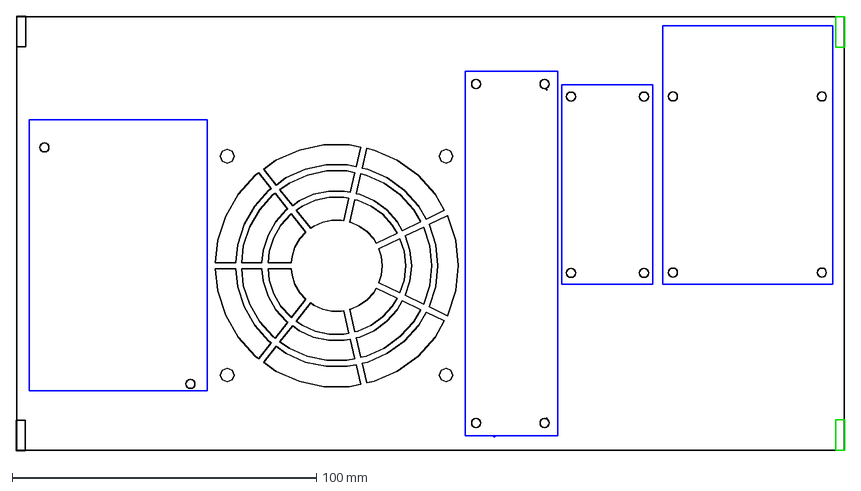
[picture p146: CAD file, 2020-01-10]
Lasercut - Custom RBPi4 + Zynscreen/Pi4_case_bottom_v2.dxf
272.6 x 142.8 mm
