zynthian/zynthian-case/V5 - Aluminum/Zynthian_V5_BENDED_TOP-230313.stp

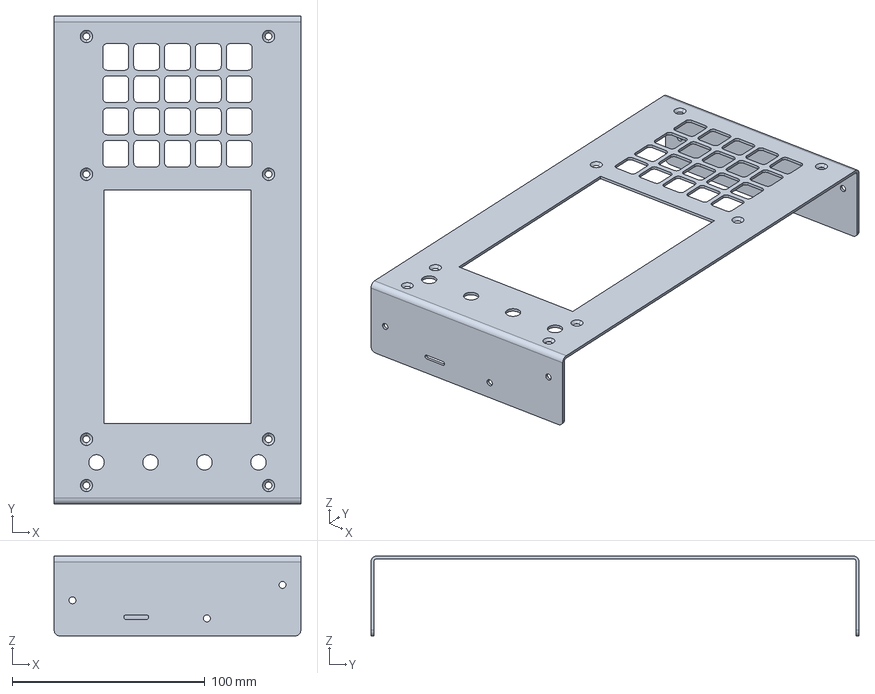
[picture p147: CAD file, 2023-07-19]
V5 - Aluminum/Zynthian_V5_BENDED_TOP-230313.stp
128.0 x 253.2 x 41.5 mm
