zynthian/zynthian-case/3D Print - Big/Top Back.stl

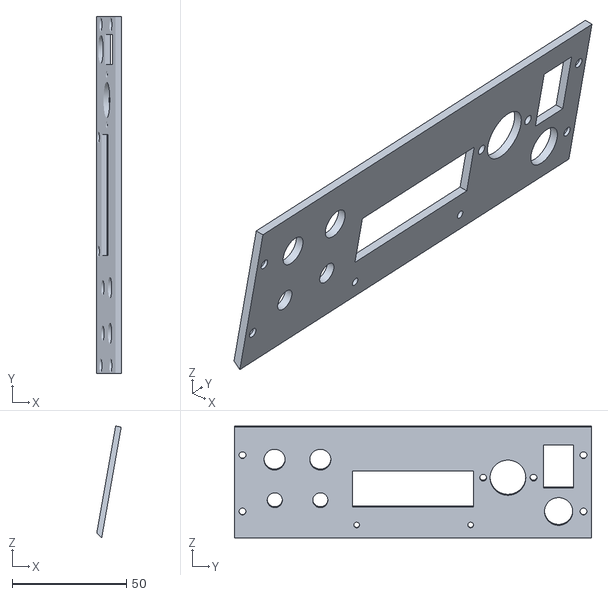
[picture p148: CAD file, 2017-04-04]
3D Print - Big/Top Back.stl
10.7 x 156.0 x 48.9
