zynthian/zynthian-case/3D Print - Mini V2/orca-slicer-project-01.3mf

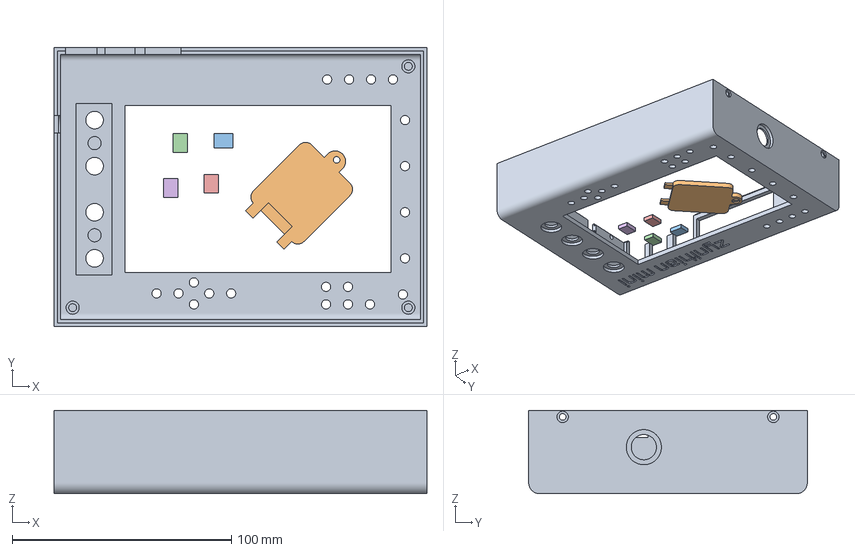
[picture p149: CAD file, 2024-05-14]
3D Print - Mini V2/orca-slicer-project-01.3mf
170.0 x 127.0 x 38.0 mm
top.stl
sd-card-door.stl
leg.stl x 4
