zynthian/zynthian-case/3D Print - Parts models/raspberry-pi-4-model-b-1.snapshot.3/Microphone Plug, RPi4ModelB.SLDPRT

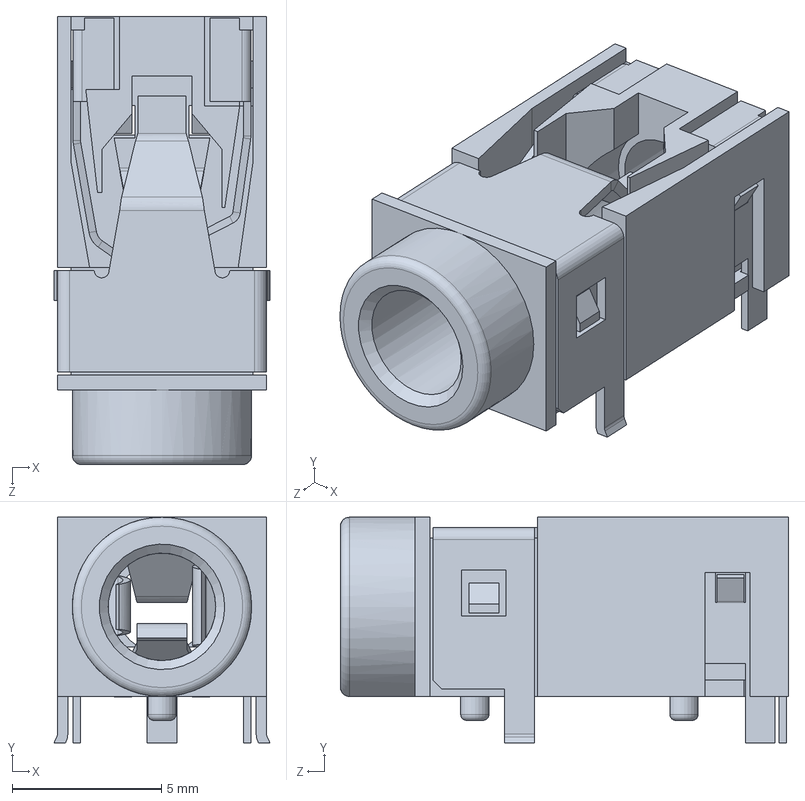
[picture p150: CAD file, 2019-09-04]
3D Print - Parts models/raspberry-pi-4-model-b-1.snapshot.3/Microphone Plug, RPi4ModelB.SLDPRT
7.23 x 7.55 x 15.0 mm
