zynthian/zynthian-case/3D Print - Zynscreen 1.5 (V4)/STL files/Zynthian_left_side.stl

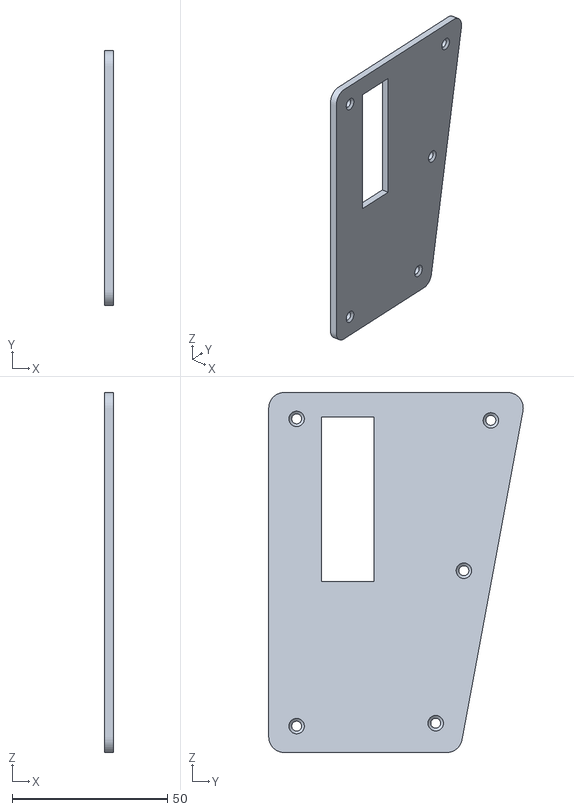
[picture p151: CAD file, 2020-08-05]
3D Print - Zynscreen 1.5 (V4)/STL files/Zynthian_left_side.stl
3.00 x 82.0 x 116.0
