zynthian/zynthian-case/3DPrint - Waveshare35/Zynhtian_Top_v1_rotated.stl

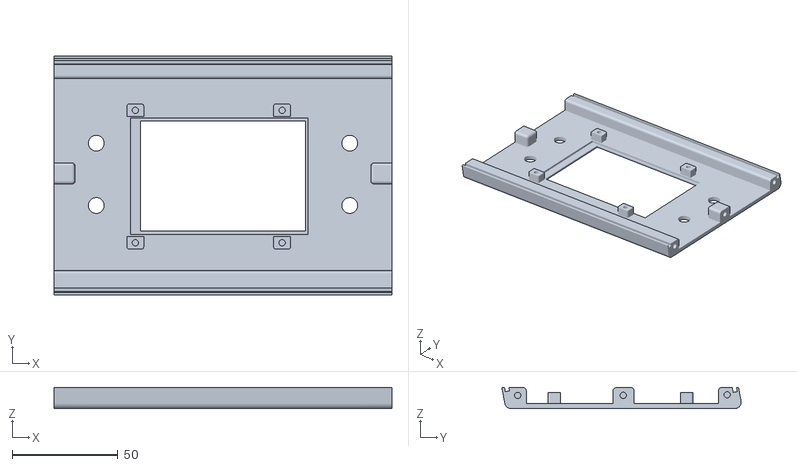
[picture p152: CAD file, 2020-08-05]
3DPrint - Waveshare35/Zynhtian_Top_v1_rotated.stl
160.0 x 113.3 x 10.0
