zynthian/zynthian-case/Aluminum - Zynscreen-v4/rubber_buttons/zynthian_box_botones_3.dxf

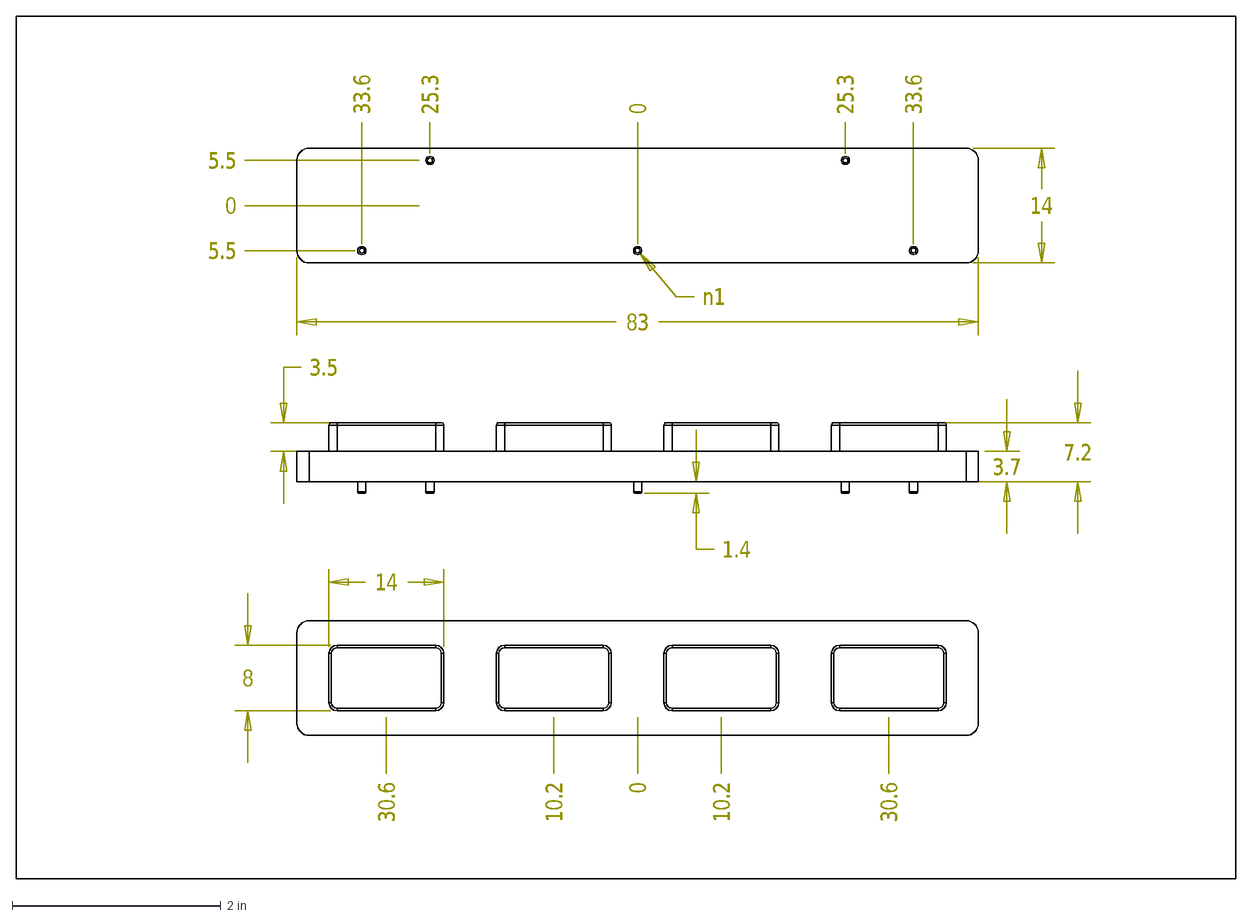
[picture p153: CAD file, 2020-08-05]
Aluminum - Zynscreen-v4/rubber_buttons/zynthian_box_botones_3.dxf
8
14
10.2
0
30.6
3.7
3.5
7.2
1.4
5.5
33.6
25.3
83
