zynthian/zynthian-case/Lasercut - Custom RBPi4 + Zynscreen/Pi4_side_right_inner.dxf

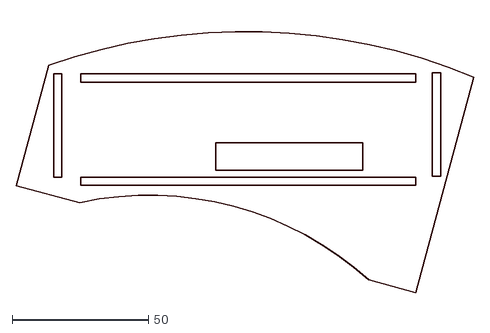
[picture p154: CAD file, 2020-01-10]
Lasercut - Custom RBPi4 + Zynscreen/Pi4_side_right_inner.dxf
168.0 x 101.5
