zynthian/zynthian-case/3D Print - Big/Right Side.stl

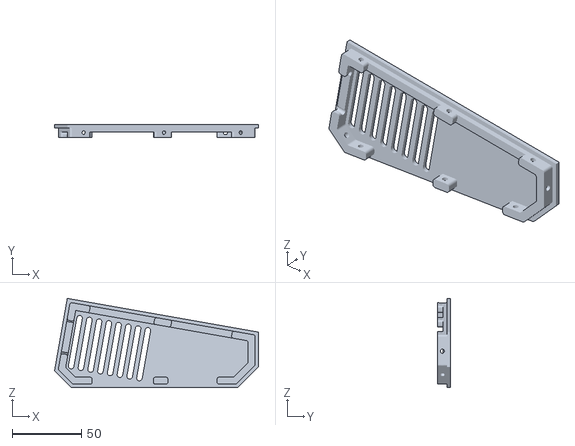
[picture p155: CAD file, 2017-04-04]
3D Print - Big/Right Side.stl
147.1 x 9.40 x 64.3
