zynthian/zynthian-case/3D Print - Lafranco/mascherina 4.3.stl

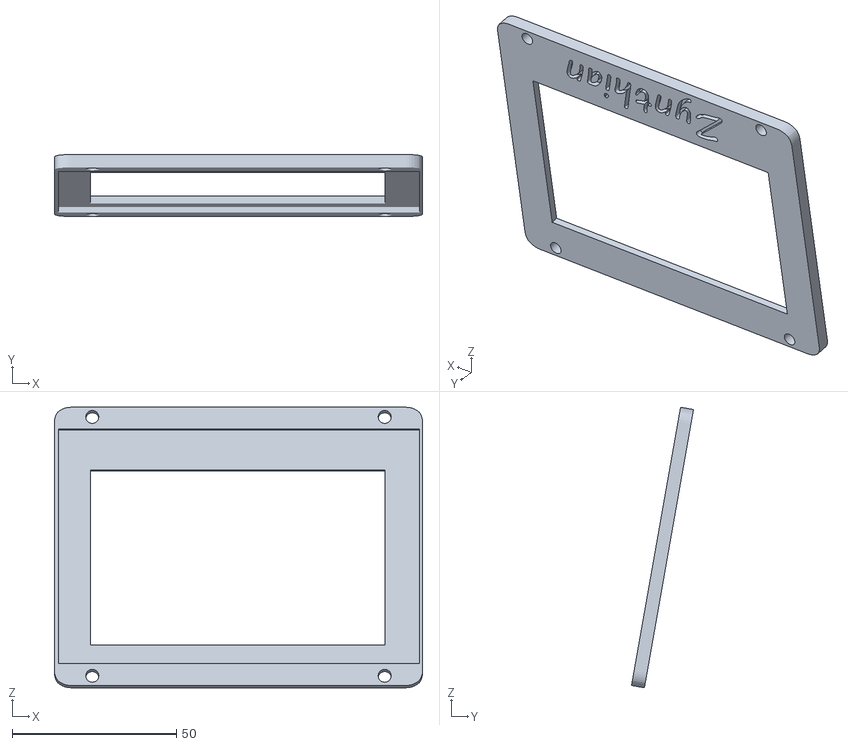
[picture p156: CAD file, 2023-07-19]
3D Print - Lafranco/mascherina 4.3.stl
112.0 x 18.9 x 85.4
