zynthian/zynthian-case/3D Print - Mini V2/zynthian-mini-PCB-v2-facia.step

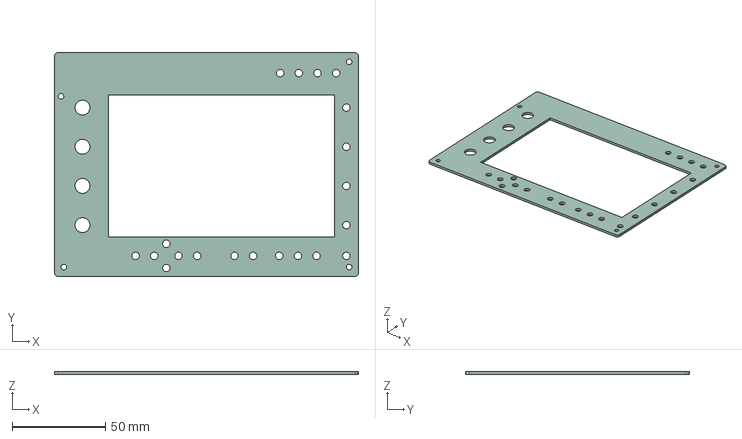
[picture p157: CAD file, 2024-05-14]
3D Print - Mini V2/zynthian-mini-PCB-v2-facia.step
163.0 x 120.0 x 1.60 mm
