zynthian/zynthian-case/3D Print - Parts models/raspberry-pi-4-model-b-1.snapshot.3/2X USB2.0 PORTS, RPi4ModelB.SLDPRT

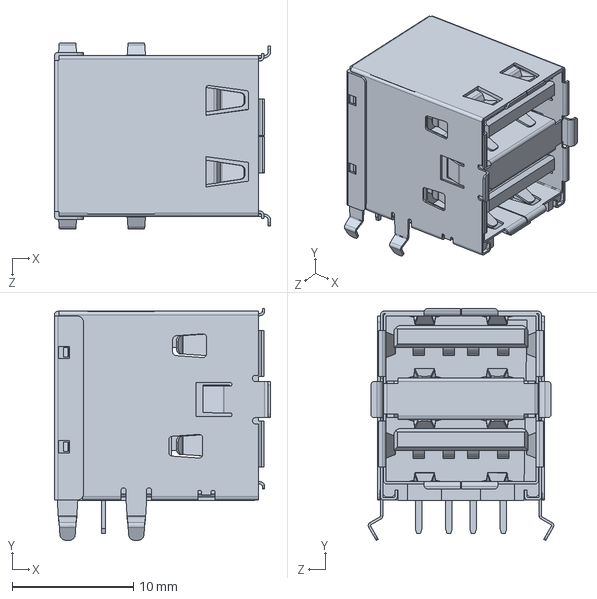
[picture p158: CAD file, 2019-09-04]
3D Print - Parts models/raspberry-pi-4-model-b-1.snapshot.3/2X USB2.0 PORTS, RPi4ModelB.SLDPRT
17.9 x 19.2 x 15.3 mm
