zynthian/zynthian-case/Lasercut - Custom RBPi4 + Zynscreen/Pi4_side_left_inner.dxf

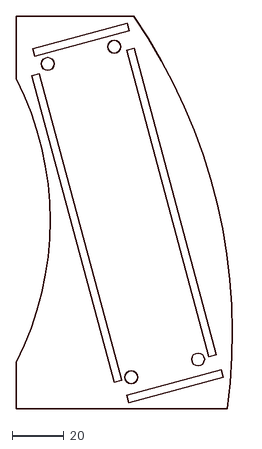
[picture p160: CAD file, 2020-01-10]
Lasercut - Custom RBPi4 + Zynscreen/Pi4_side_left_inner.dxf
89.1 x 152.0
