zynthian/zynthian-case/3D Print - Lafranco/Fronte.stl

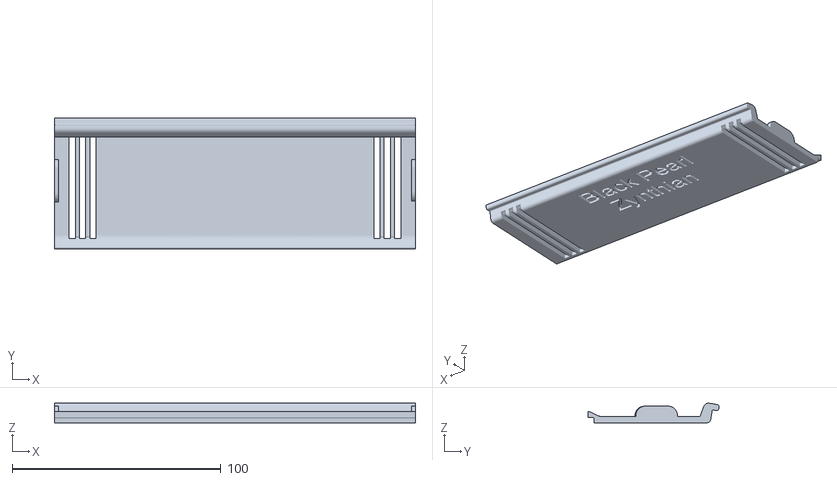
[picture p161: CAD file, 2023-07-19]
3D Print - Lafranco/Fronte.stl
173.0 x 62.9 x 9.42
