zynthian/zynthian-case/3D Print - Parts models/raspberry-pi-4-model-b-1.snapshot.3/Broadcom BCM54213PE Gigabit Ethernet Transceiver, RPi4ModelB.SLDPRT

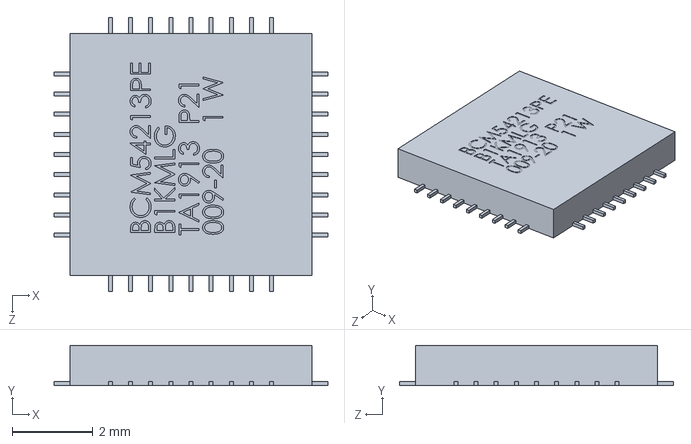
[picture p162: CAD file, 2019-09-04]
3D Print - Parts models/raspberry-pi-4-model-b-1.snapshot.3/Broadcom BCM54213PE Gigabit Ethernet Transceiver, RPi4ModelB.SLDPRT
6.80 x 1.00 x 6.80 mm
