zynthian/zynthian-case/3DPrint - Waveshare35/Zynthian_disp_beam_rotated.stl

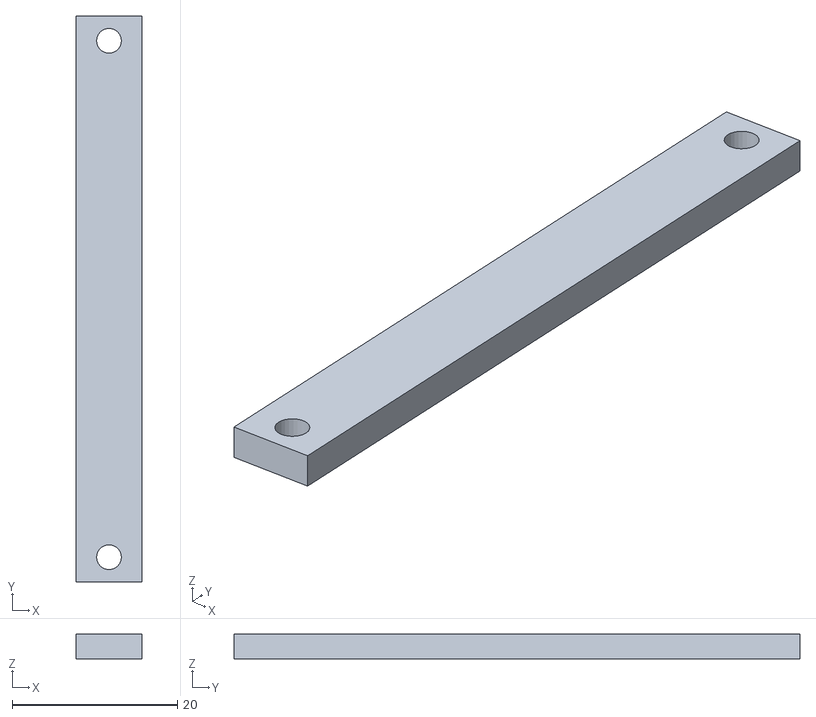
[picture p163: CAD file, 2020-08-05]
3DPrint - Waveshare35/Zynthian_disp_beam_rotated.stl
8.00 x 68.5 x 3.00
