zynthian/zynthian-case/Aluminum - Zynscreen-v4/rubber_buttons/botones_zynt_110520.stp

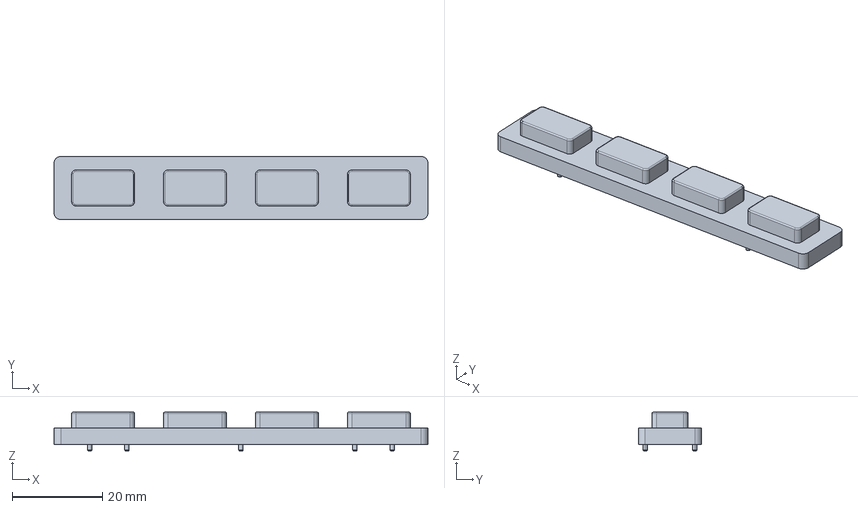
[picture p164: CAD file, 2020-08-05]
Aluminum - Zynscreen-v4/rubber_buttons/botones_zynt_110520.stp
83.0 x 14.0 x 8.60 mm
