zynthian/zynthian-case/Lasercut - Custom RBPi4 + Zynscreen/Pi4_side_outer.dxf

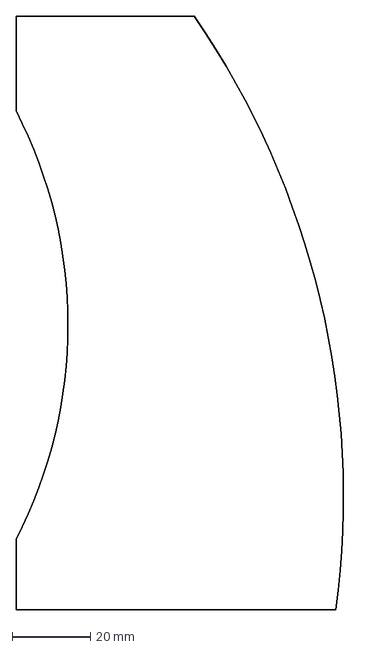
[picture p165: CAD file, 2020-01-10]
Lasercut - Custom RBPi4 + Zynscreen/Pi4_side_outer.dxf
89.1 x 152.0 mm
