zynthian/zynthian-case/3D Print - Big/Bottom Back.stl

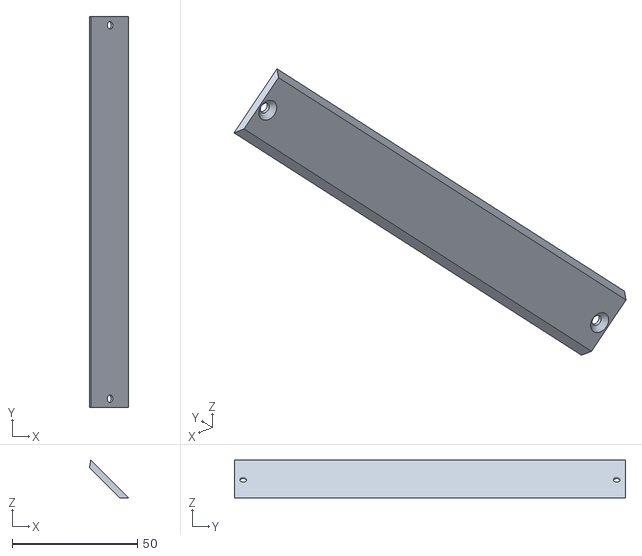
[picture p166: CAD file, 2017-04-04]
3D Print - Big/Bottom Back.stl
15.6 x 156.0 x 15.1
