zynthian/zynthian-case/3D Print - Mini V2/sd-card-door.stl

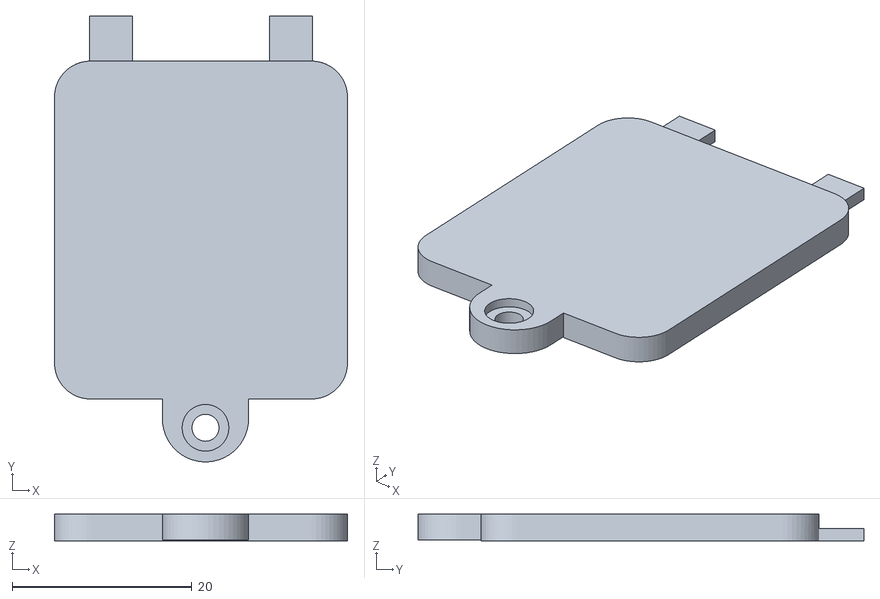
[picture p167: CAD file, 2024-05-14]
3D Print - Mini V2/sd-card-door.stl
32.6 x 49.6 x 3.00
