zynthian/zynthian-case/3D Print - Parts models/raspberry-pi-4-model-b-1.snapshot.3/VIA VL805 PCIe USB 3.0 controller, RPi4ModelB.SLDPRT

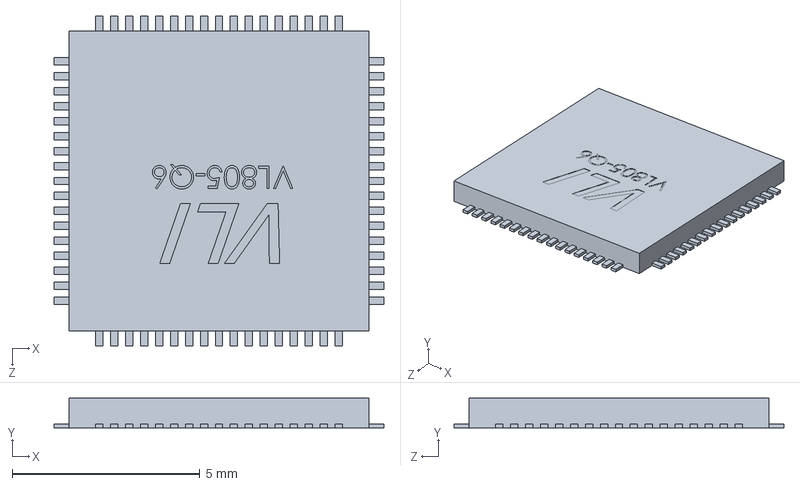
[picture p168: CAD file, 2019-09-04]
3D Print - Parts models/raspberry-pi-4-model-b-1.snapshot.3/VIA VL805 PCIe USB 3.0 controller, RPi4ModelB.SLDPRT
8.80 x 0.8 x 8.80 mm
