zynthian/zynthian-case/Lasercut - Custom RBPi4 + Zynscreen/Pi4_case_back.dxf

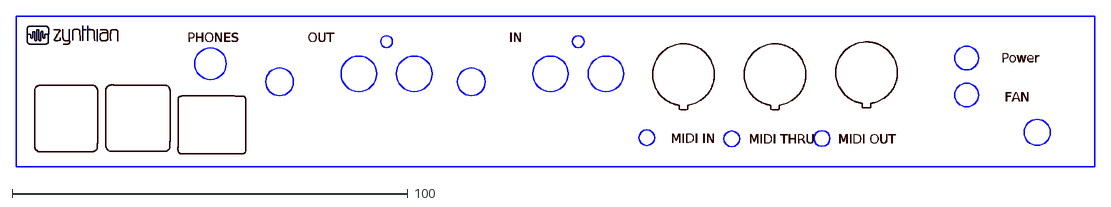
[picture p169: CAD file, 2020-01-10]
Lasercut - Custom RBPi4 + Zynscreen/Pi4_case_back.dxf
MIDI THRU
MIDI IN
MIDI OUT
PHONES
OUT
IN
Power
FAN
