zynthian/zynthian-case/3D Print - Big/Top Cover.stl

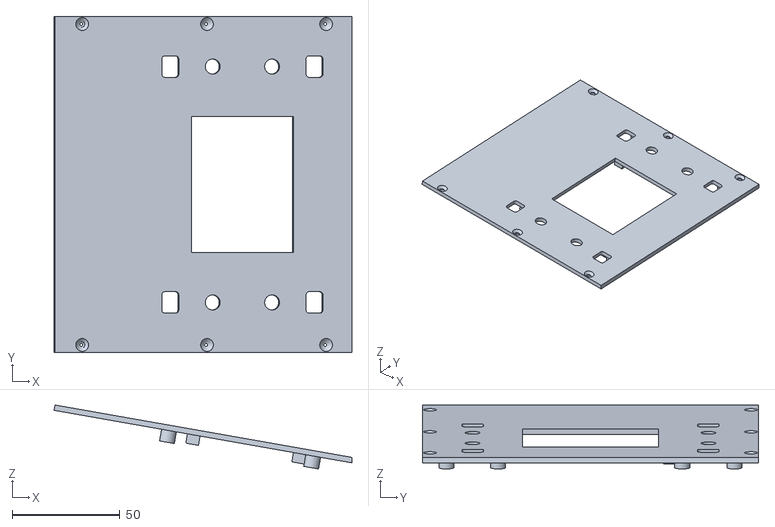
[picture p170: CAD file, 2017-04-04]
3D Print - Big/Top Cover.stl
138.3 x 156.0 x 29.7
