zynthian/zynthian-case/3D Print - Parts models/raspberry-pi-4-model-b-1.snapshot.3/2X USB3.0 PORTS, RPi4ModelB.SLDPRT

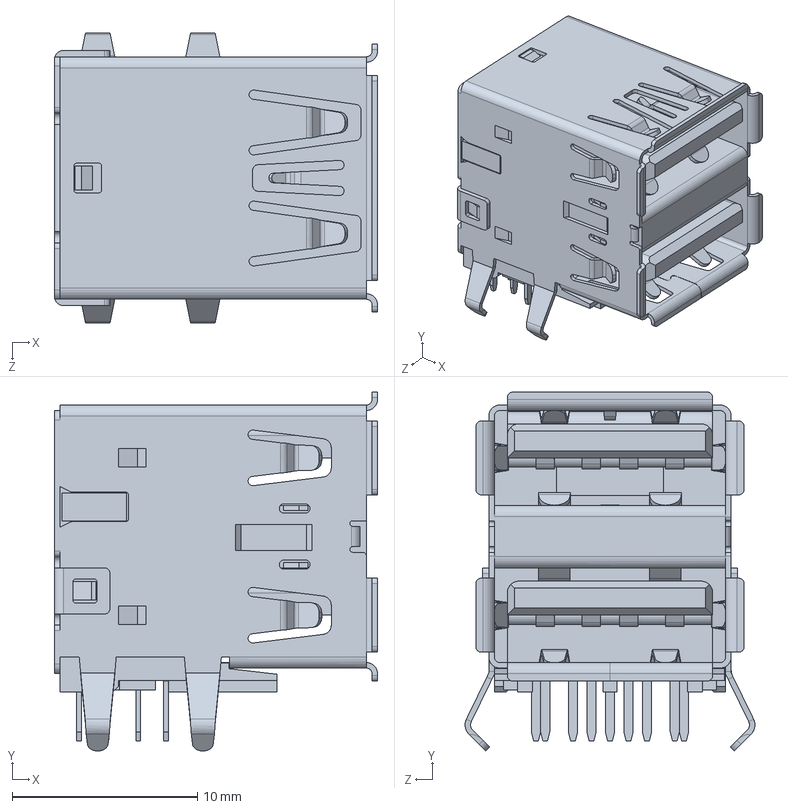
[picture p171: CAD file, 2019-09-04]
3D Print - Parts models/raspberry-pi-4-model-b-1.snapshot.3/2X USB3.0 PORTS, RPi4ModelB.SLDPRT
17.5 x 19.4 x 15.7 mm
