zynthian/zynthian-case/Lasercut - Custom RBPi4 + Zynscreen/Pi4_case_front.dxf

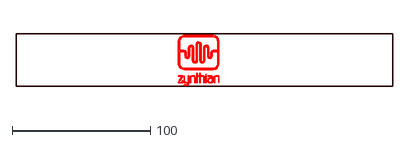
[picture p172: CAD file, 2020-01-10]
Lasercut - Custom RBPi4 + Zynscreen/Pi4_case_front.dxf
272.0 x 38.0
