zynthian/zynthian-case/3D Print - Big/Knob.stl

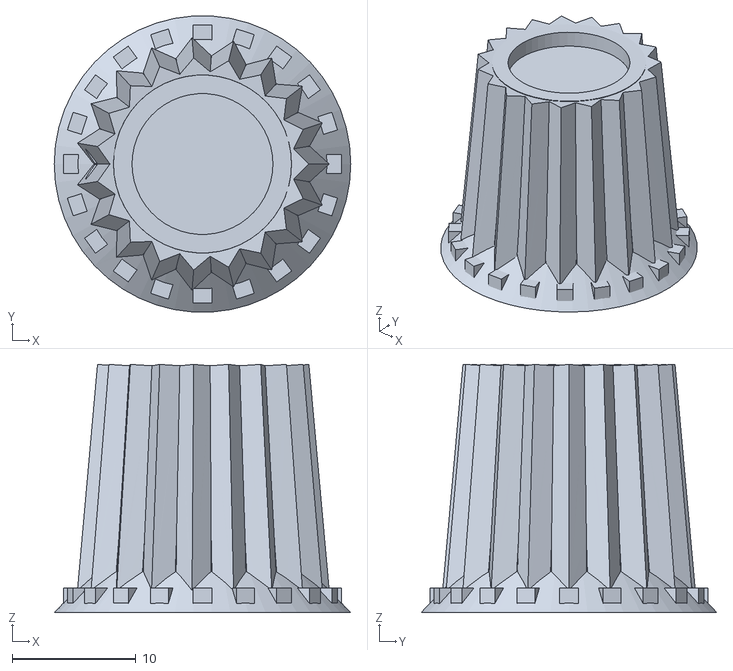
[picture p173: CAD file, 2017-04-04]
3D Print - Big/Knob.stl
24.0 x 24.0 x 20.1
