zynthian/zynthian-case/3D Print - Big/Underside.stl

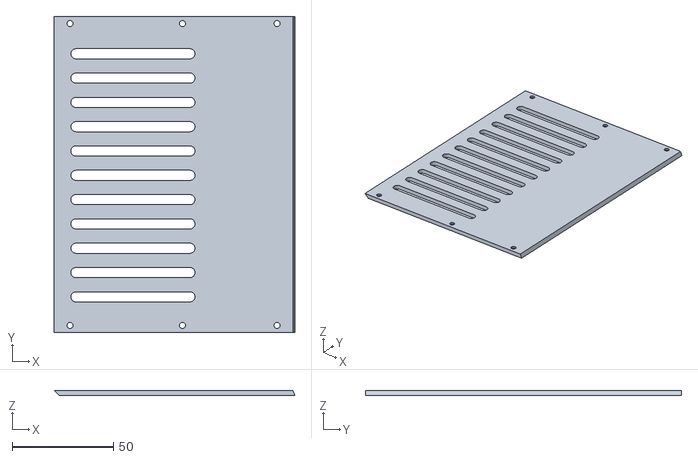
[picture p174: CAD file, 2017-04-04]
3D Print - Big/Underside.stl
119.0 x 156.0 x 2.50
