zynthian/zynthian-case/3D Print - Big/Case 2 v20.png

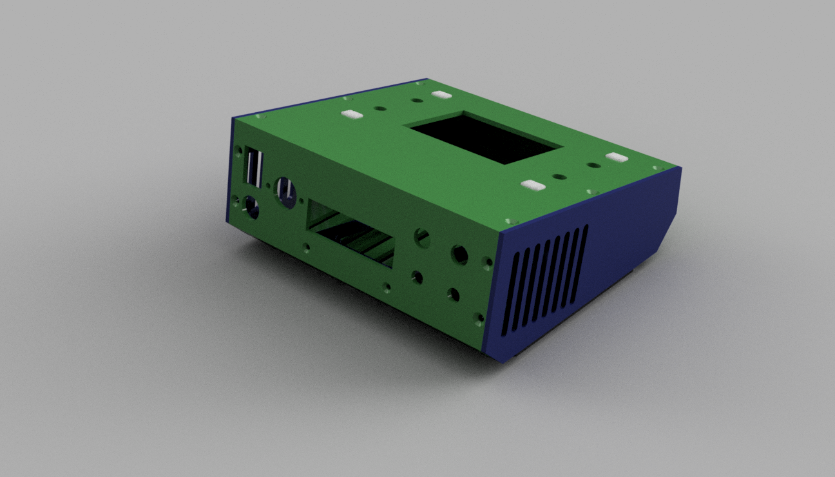
3D Print - Big/Case 2 v20.png
