zynthian/zynthian-case/3D Print - Lafranco/Case Zynthian.jpg

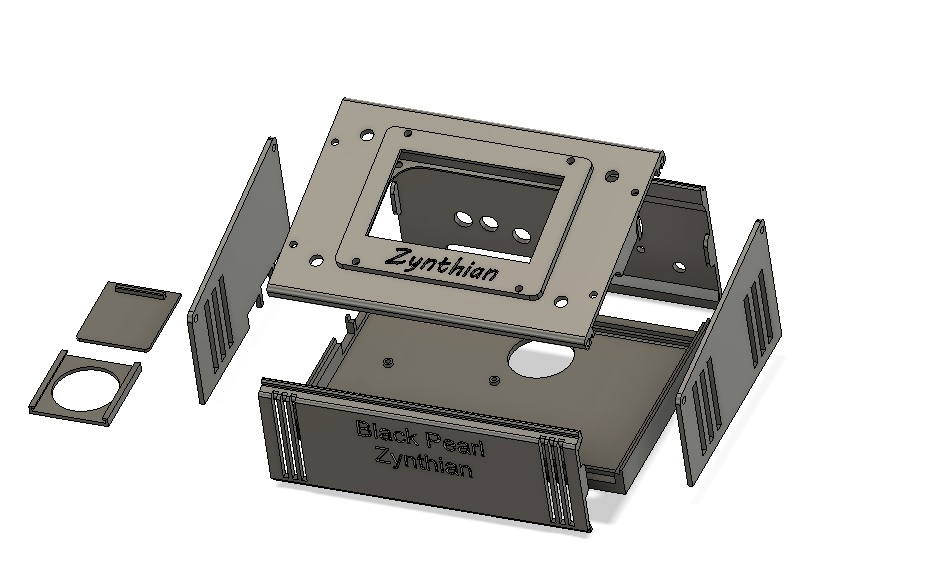
3D Print - Lafranco/Case Zynthian.jpg
