zynthian/zynthian-case/3D Print - Mini V2/resources/5.0-dimensions.png

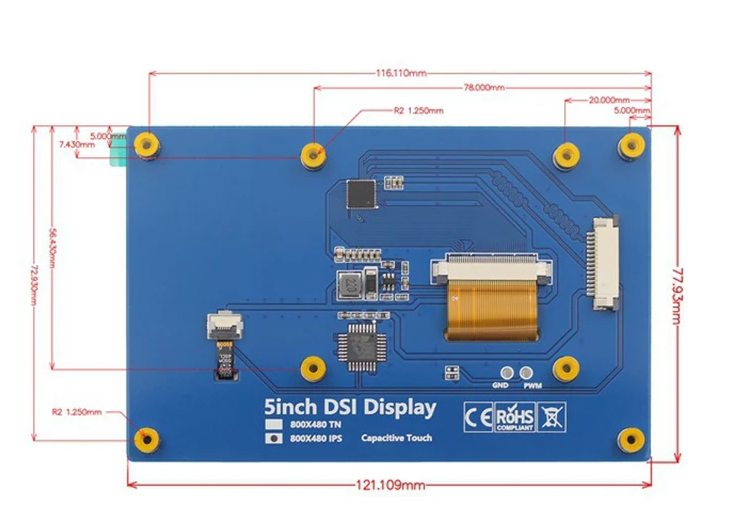
3D Print - Mini V2/resources/5.0-dimensions.png
