zynthian/zynthian-case/3D Print - Mini V2/resources/assembly-14.png

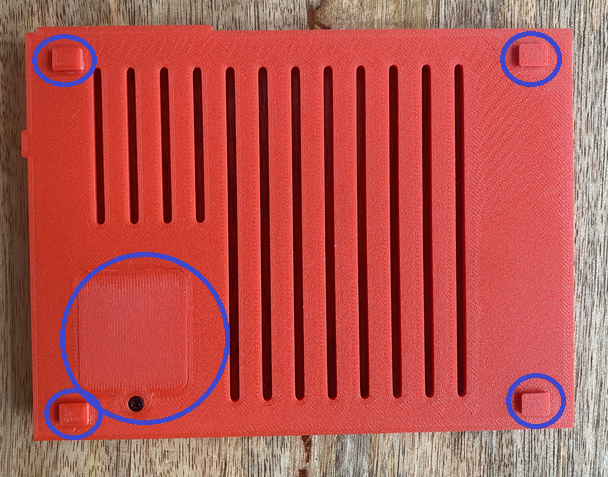
3D Print - Mini V2/resources/assembly-14.png
