zynthian/zynthian-case/3D Print - Mini V2/resources/case-rev2.png

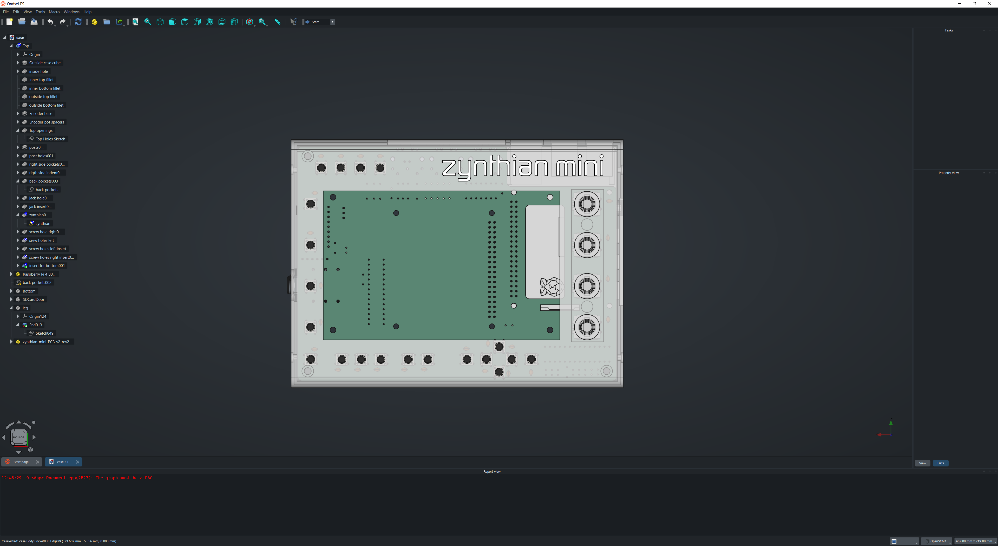
3D Print - Mini V2/resources/case-rev2.png
