zynthian/zynthian-case/3D Print - Mini V2/resources/zynthian_mini_v2_rear.png

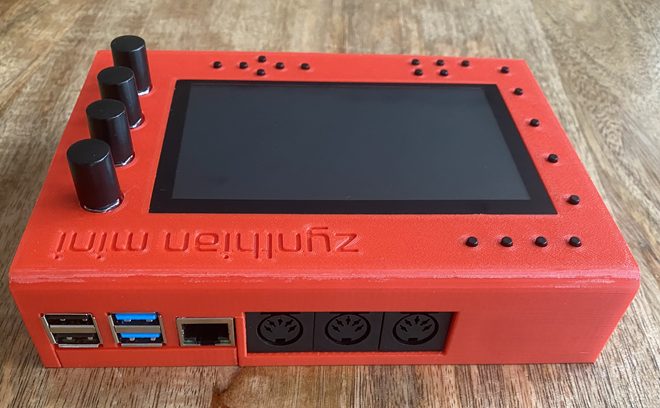
3D Print - Mini V2/resources/zynthian_mini_v2_rear.png
