zynthian/zynthian-case/3D Print - PiScreen2 + 3xMIDI/case_back.jpg

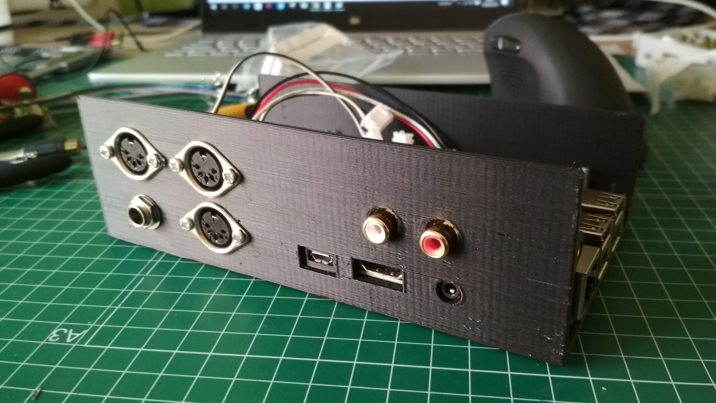
3D Print - PiScreen2 + 3xMIDI/case_back.jpg
