zynthian/zynthian-case/3D Print - PiScreen2 + 3xMIDI/case_finished.jpg

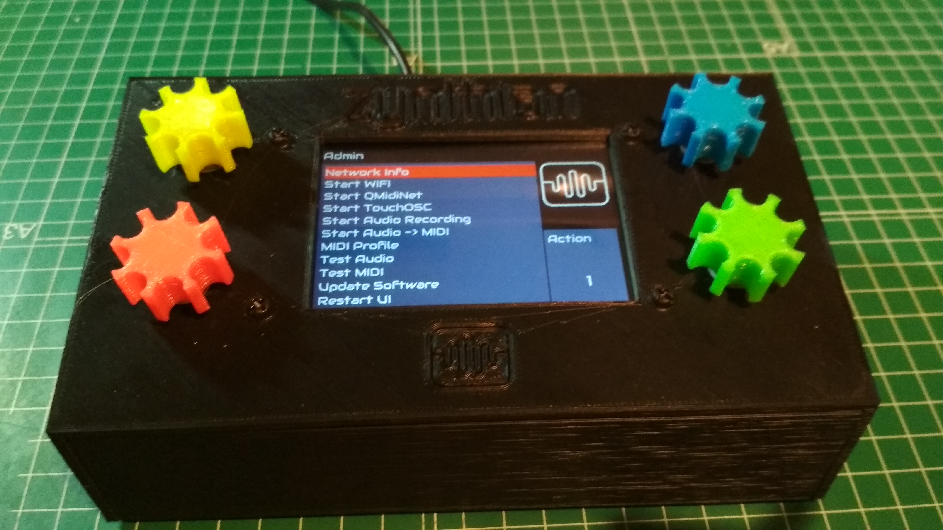
3D Print - PiScreen2 + 3xMIDI/case_finished.jpg
