zynthian/zynthian-case/3D Print - PiScreen2 + 3xMIDI/case_front.jpg

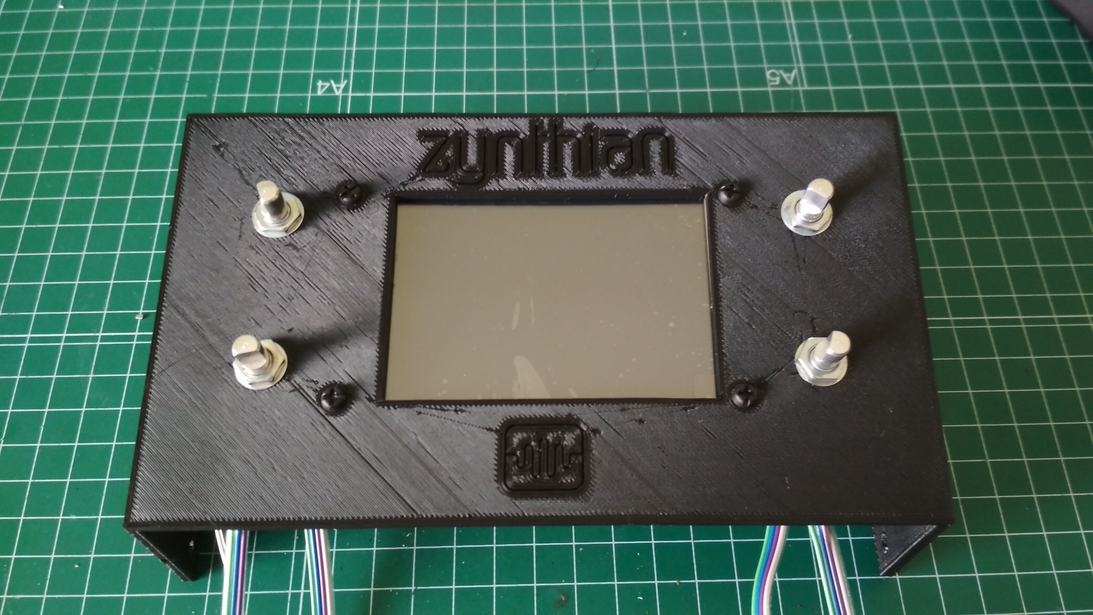
3D Print - PiScreen2 + 3xMIDI/case_front.jpg
