zynthian/zynthian-case/3D Print - PiScreen2 + 3xMIDI/case_inside.jpg

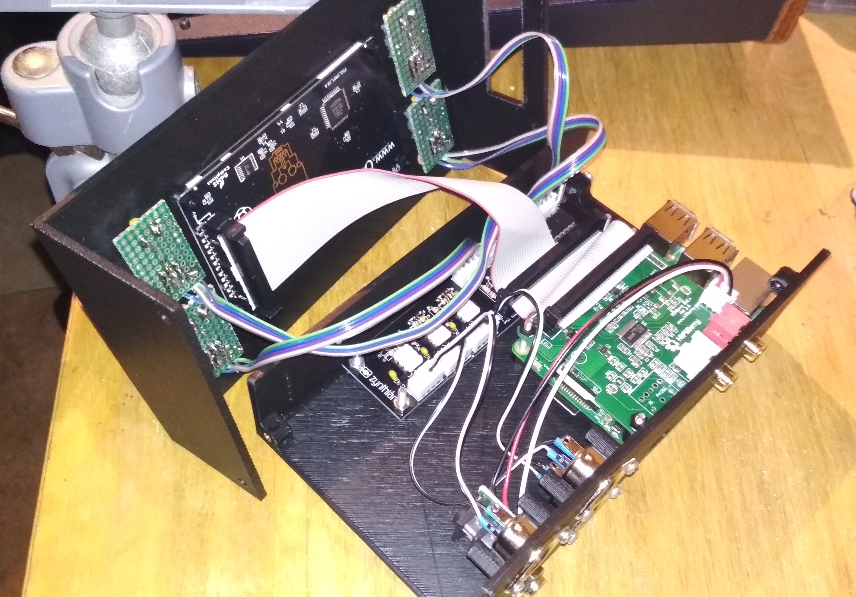
3D Print - PiScreen2 + 3xMIDI/case_inside.jpg
