zynthian/zynthian-case/3D Print - PiScreen2 + 3xMIDI/encoder.jpg

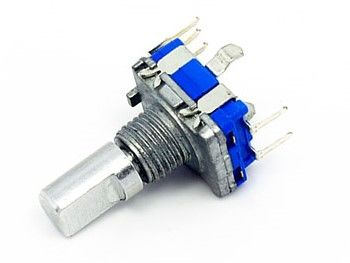
3D Print - PiScreen2 + 3xMIDI/encoder.jpg
