zynthian/zynthian-case/3D Print - PiScreen2 + 3xMIDI/insertnut_detail.jpg

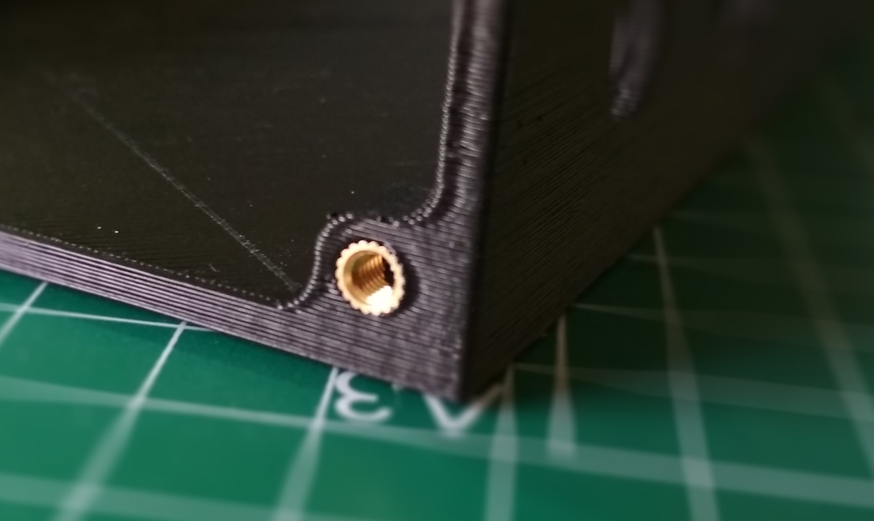
3D Print - PiScreen2 + 3xMIDI/insertnut_detail.jpg
