zynthian/zynthian-case/3D Print - PiScreen2 + 3xMIDI/midi_connector.jpg

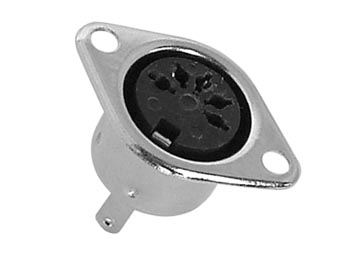
3D Print - PiScreen2 + 3xMIDI/midi_connector.jpg
