zynthian/zynthian-case/3D Print - Zynscreen 1.5 (V4)/Pictures/inside.jpg

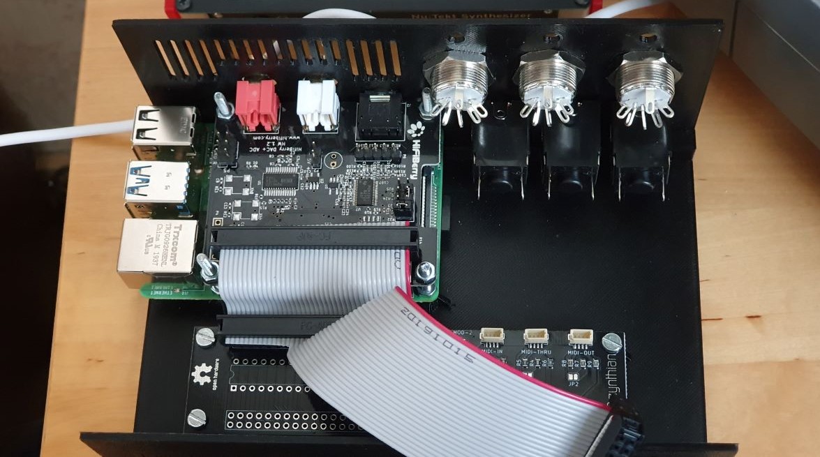
3D Print - Zynscreen 1.5 (V4)/Pictures/inside.jpg
