zynthian/zynthian-case/3D Print - Zynthian 4.3/Images/1673763126201.jpg

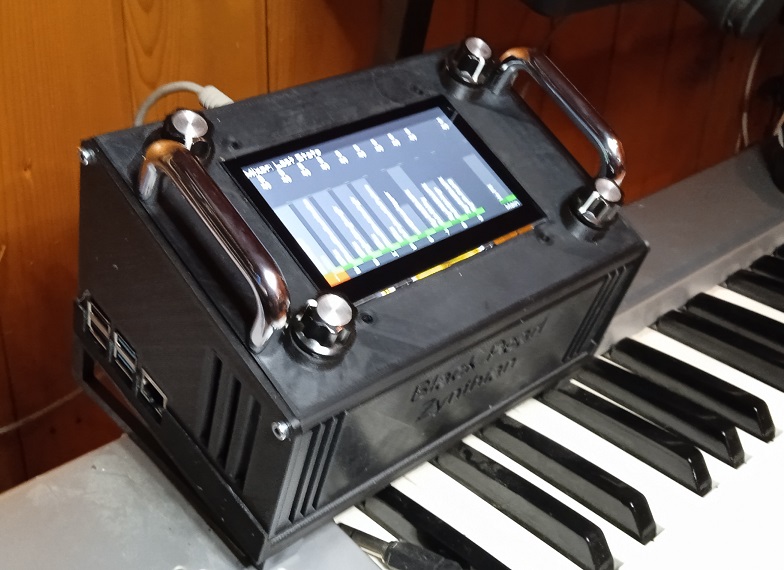
3D Print - Zynthian 4.3/Images/1673763126201.jpg
