zynthian/zynthian-case/V5 - Aluminum/printing/V5_printings_02.png

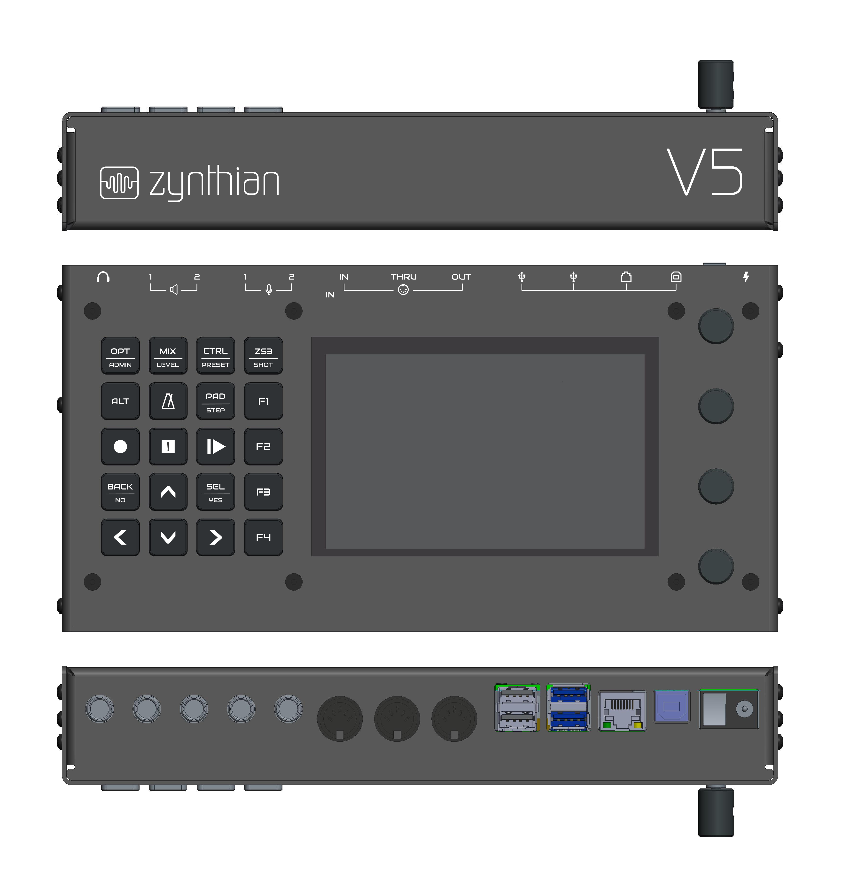
V5 - Aluminum/printing/V5_printings_02.png
