zynthian/zynthian-case/Aluminum - PiScreen-v2.2/zynthian_box_2p_3midi_v05-serigrafia_top.pdf

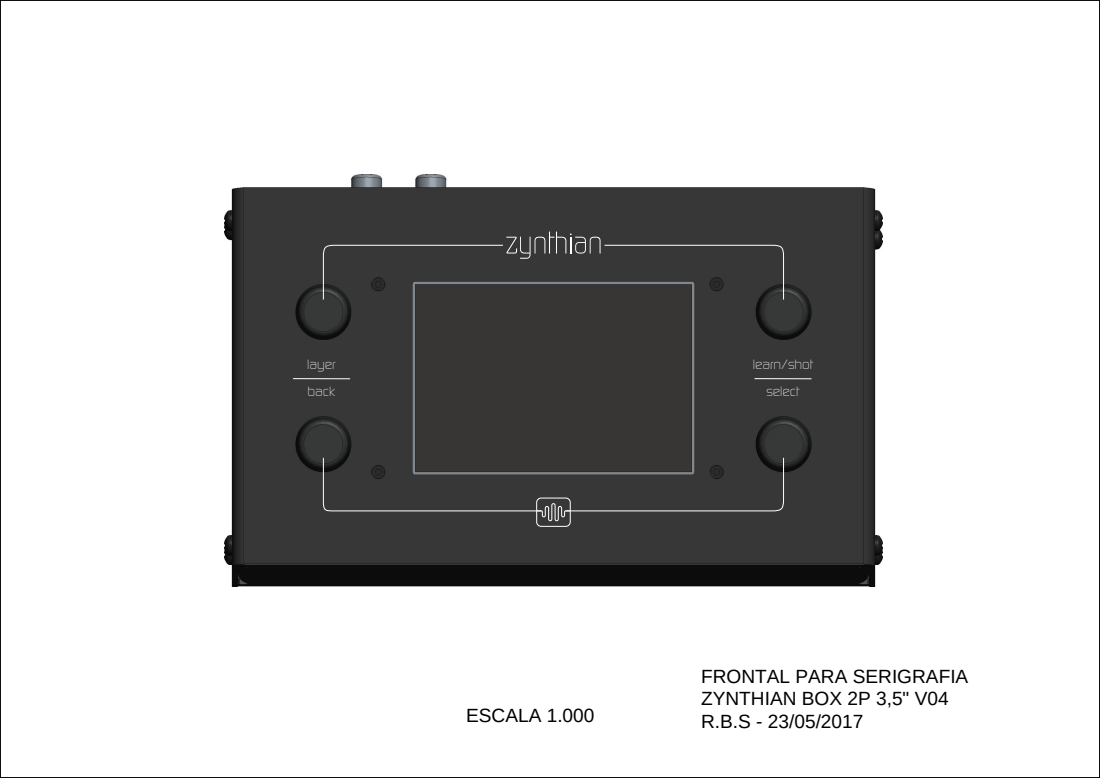
[picture p219: page 1]
ESCALA 1.000; select; learn/shot; back; layer

FRONTAL PARA SERIGRAFIA
ZYNTHIAN BOX 2P 3,5" V04
