zynthian/zynthian-case/Aluminum - PiTFT28/zynthian_box_aluminum_v04_back_BW.pdf

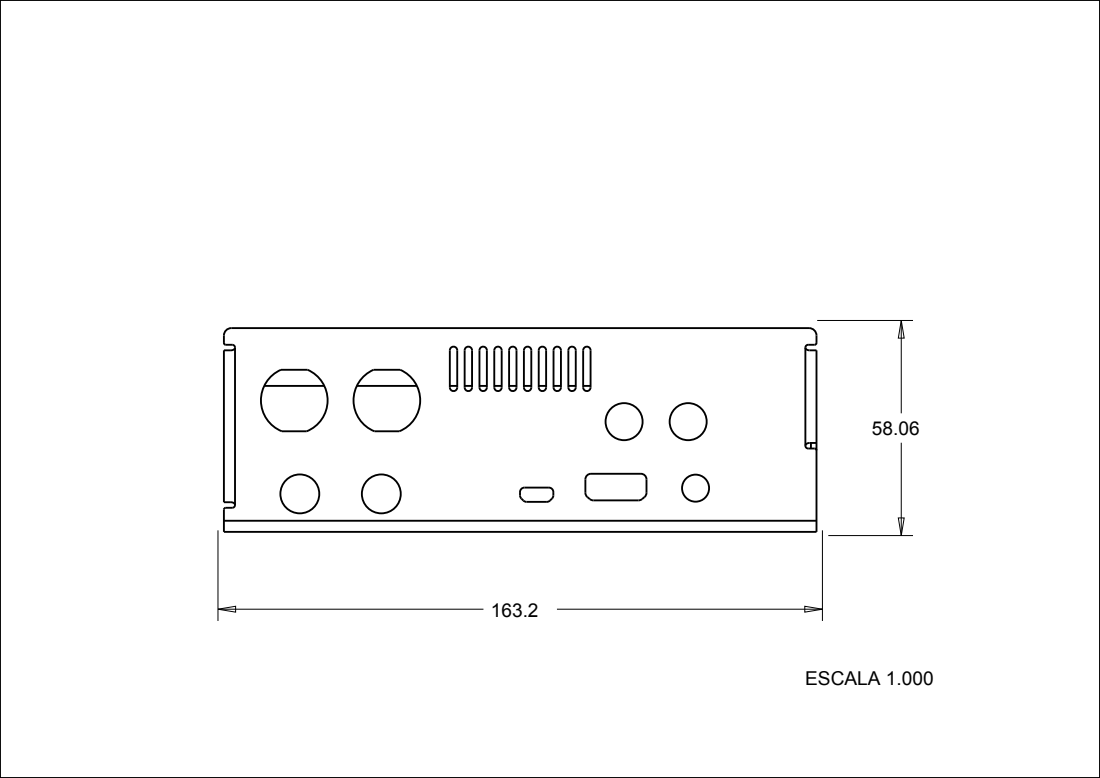
[picture p220: page 1]
ESCALA 1.000
