zynthian/zynthian-case/Aluminum - PiTFT28/zynthian_box_aluminum_v04_base_desp_fixed.pdf

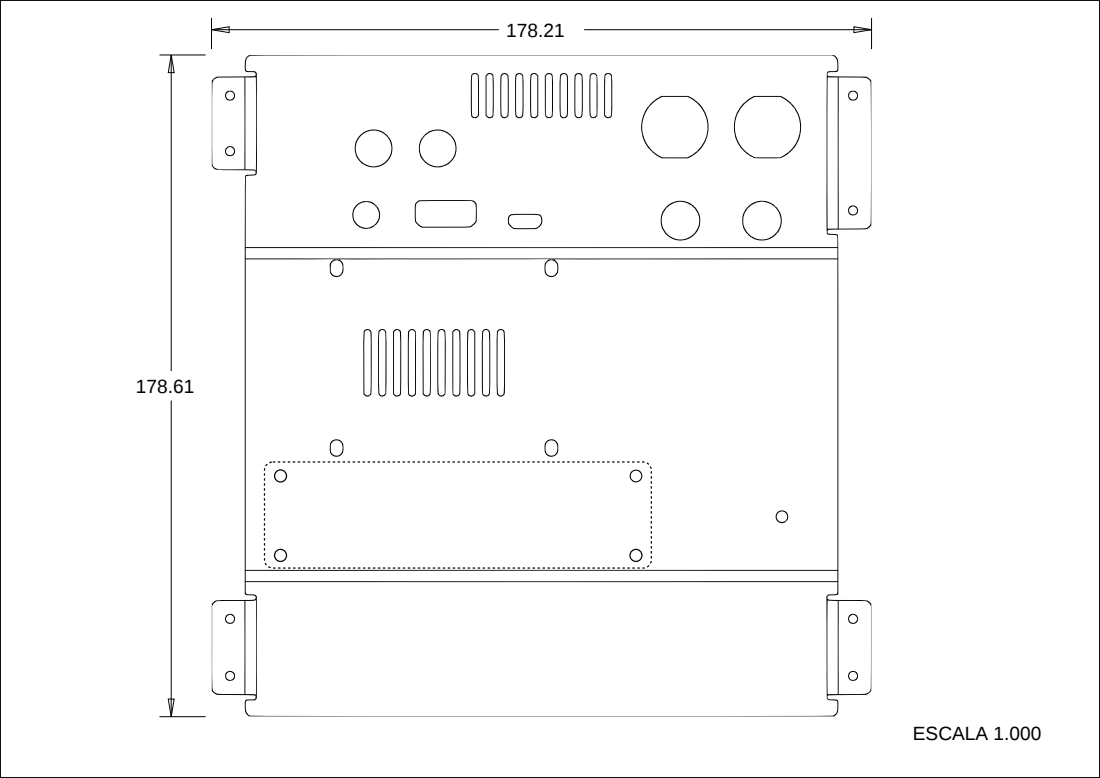
[picture p221: page 1]
ESCALA 1.000
