zynthian/zynthian-case/Aluminum - Zynscreen-v4/rubber_buttons/rubber_switches_serigraphy.pdf

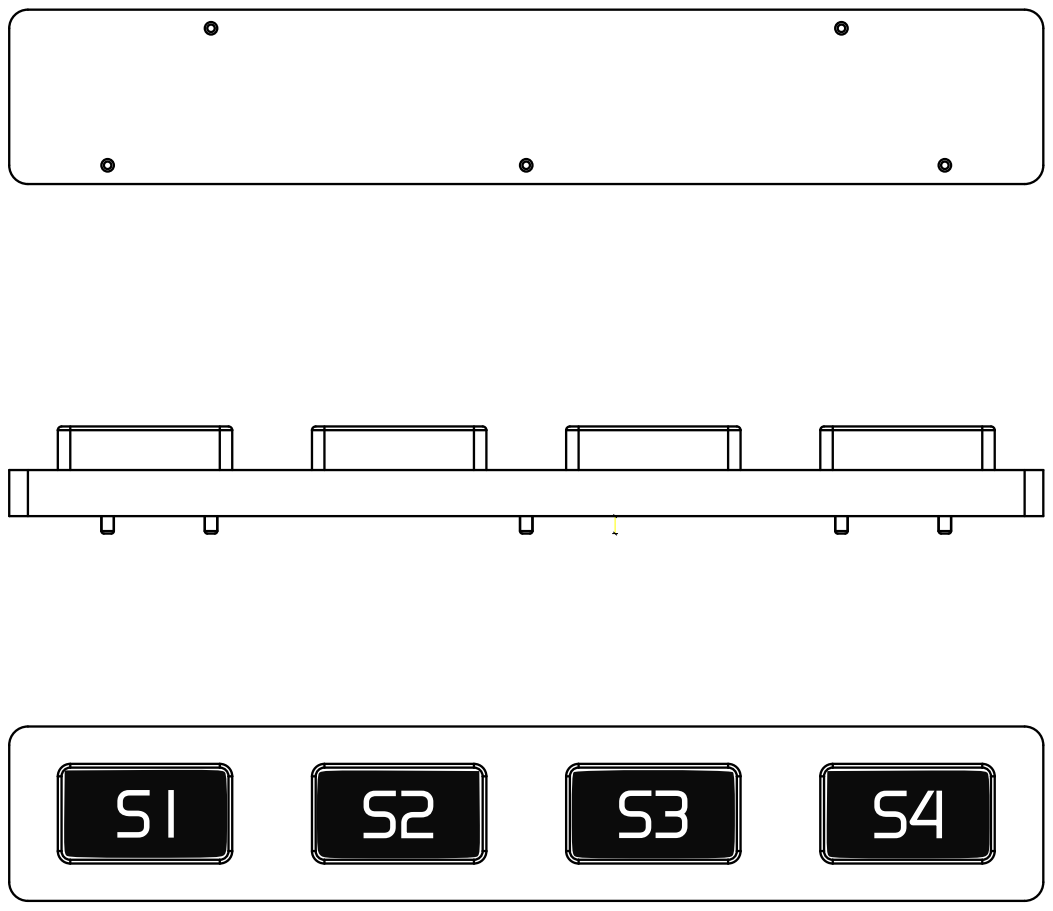
[picture p222: page 1]
