zynthian/zynthian-case/Aluminum - PiTFT28/rotulation/zynthian_box_rotulation_v1.pdf

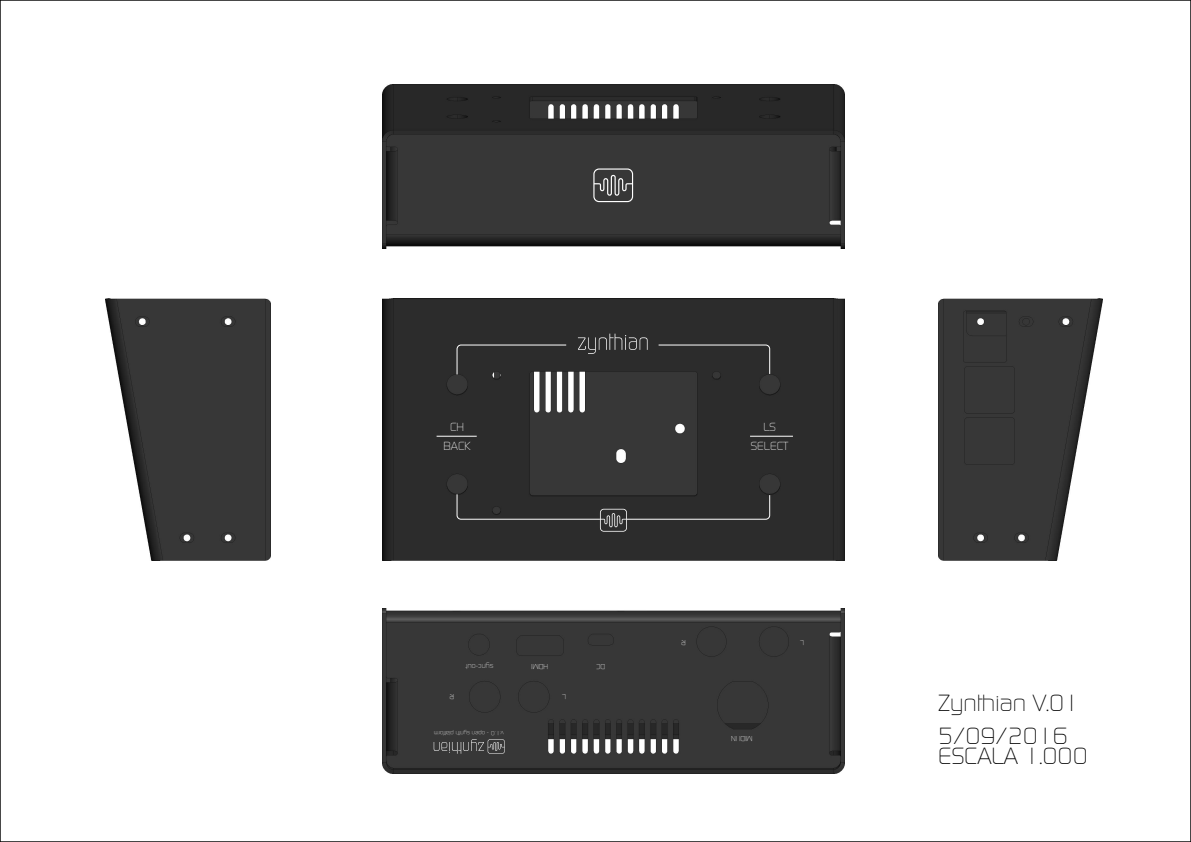
[picture p223: page 1]
Zynthian V.01; 5/09/2016 ESCALA 1.000; BACK; SELECT
