zynthian/zynthian-case/Aluminum - PiScreen-v2/zynthian_box_2p_3_5_v04-serigrafia_back-fix2.pdf

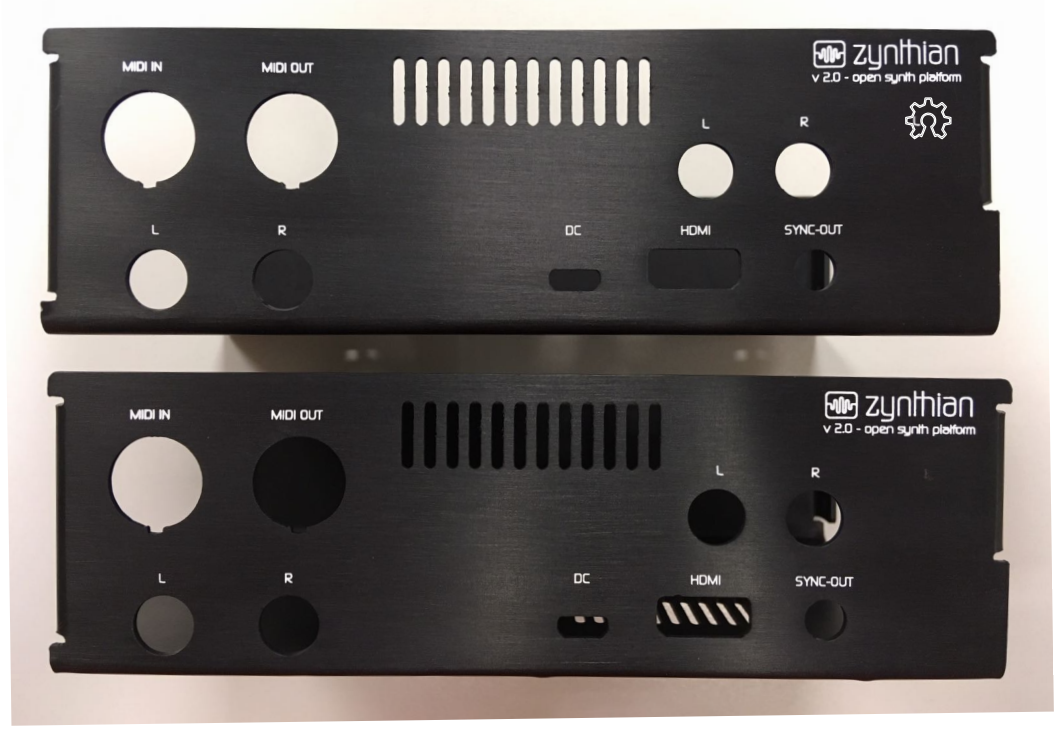
[picture p226: page 1]
