zynthian/zynthian-case/Aluminum - PiScreen-v2.1/zynthian_box_2p_3midi_v05-serigrafia_back.pdf

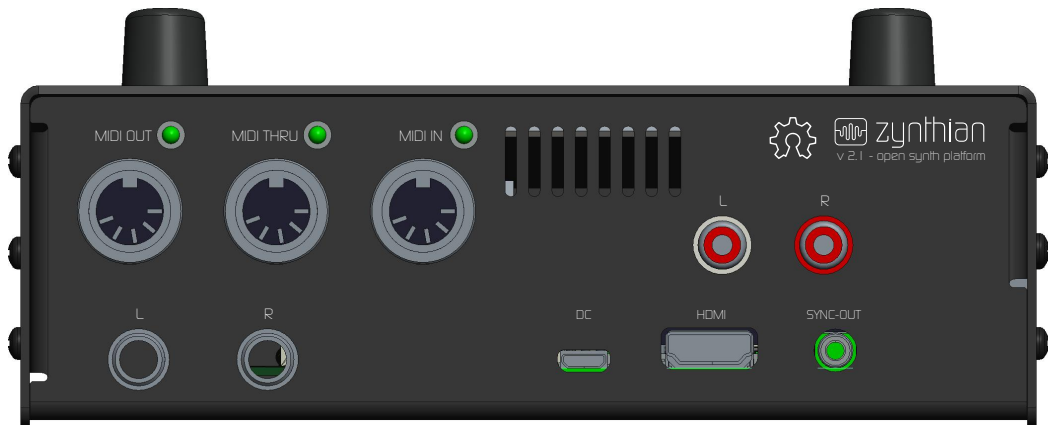
[picture p227: page 1]
MIDI OUT; HDMI; SYNC-OUT; MIDI THRU; MIDI IN

v 2.1 - open synth platform
