zynthian/zynthian-case/Aluminum - PiScreen-v2/zynthian_box_2p_3_5_v04-serigrafia_back.pdf

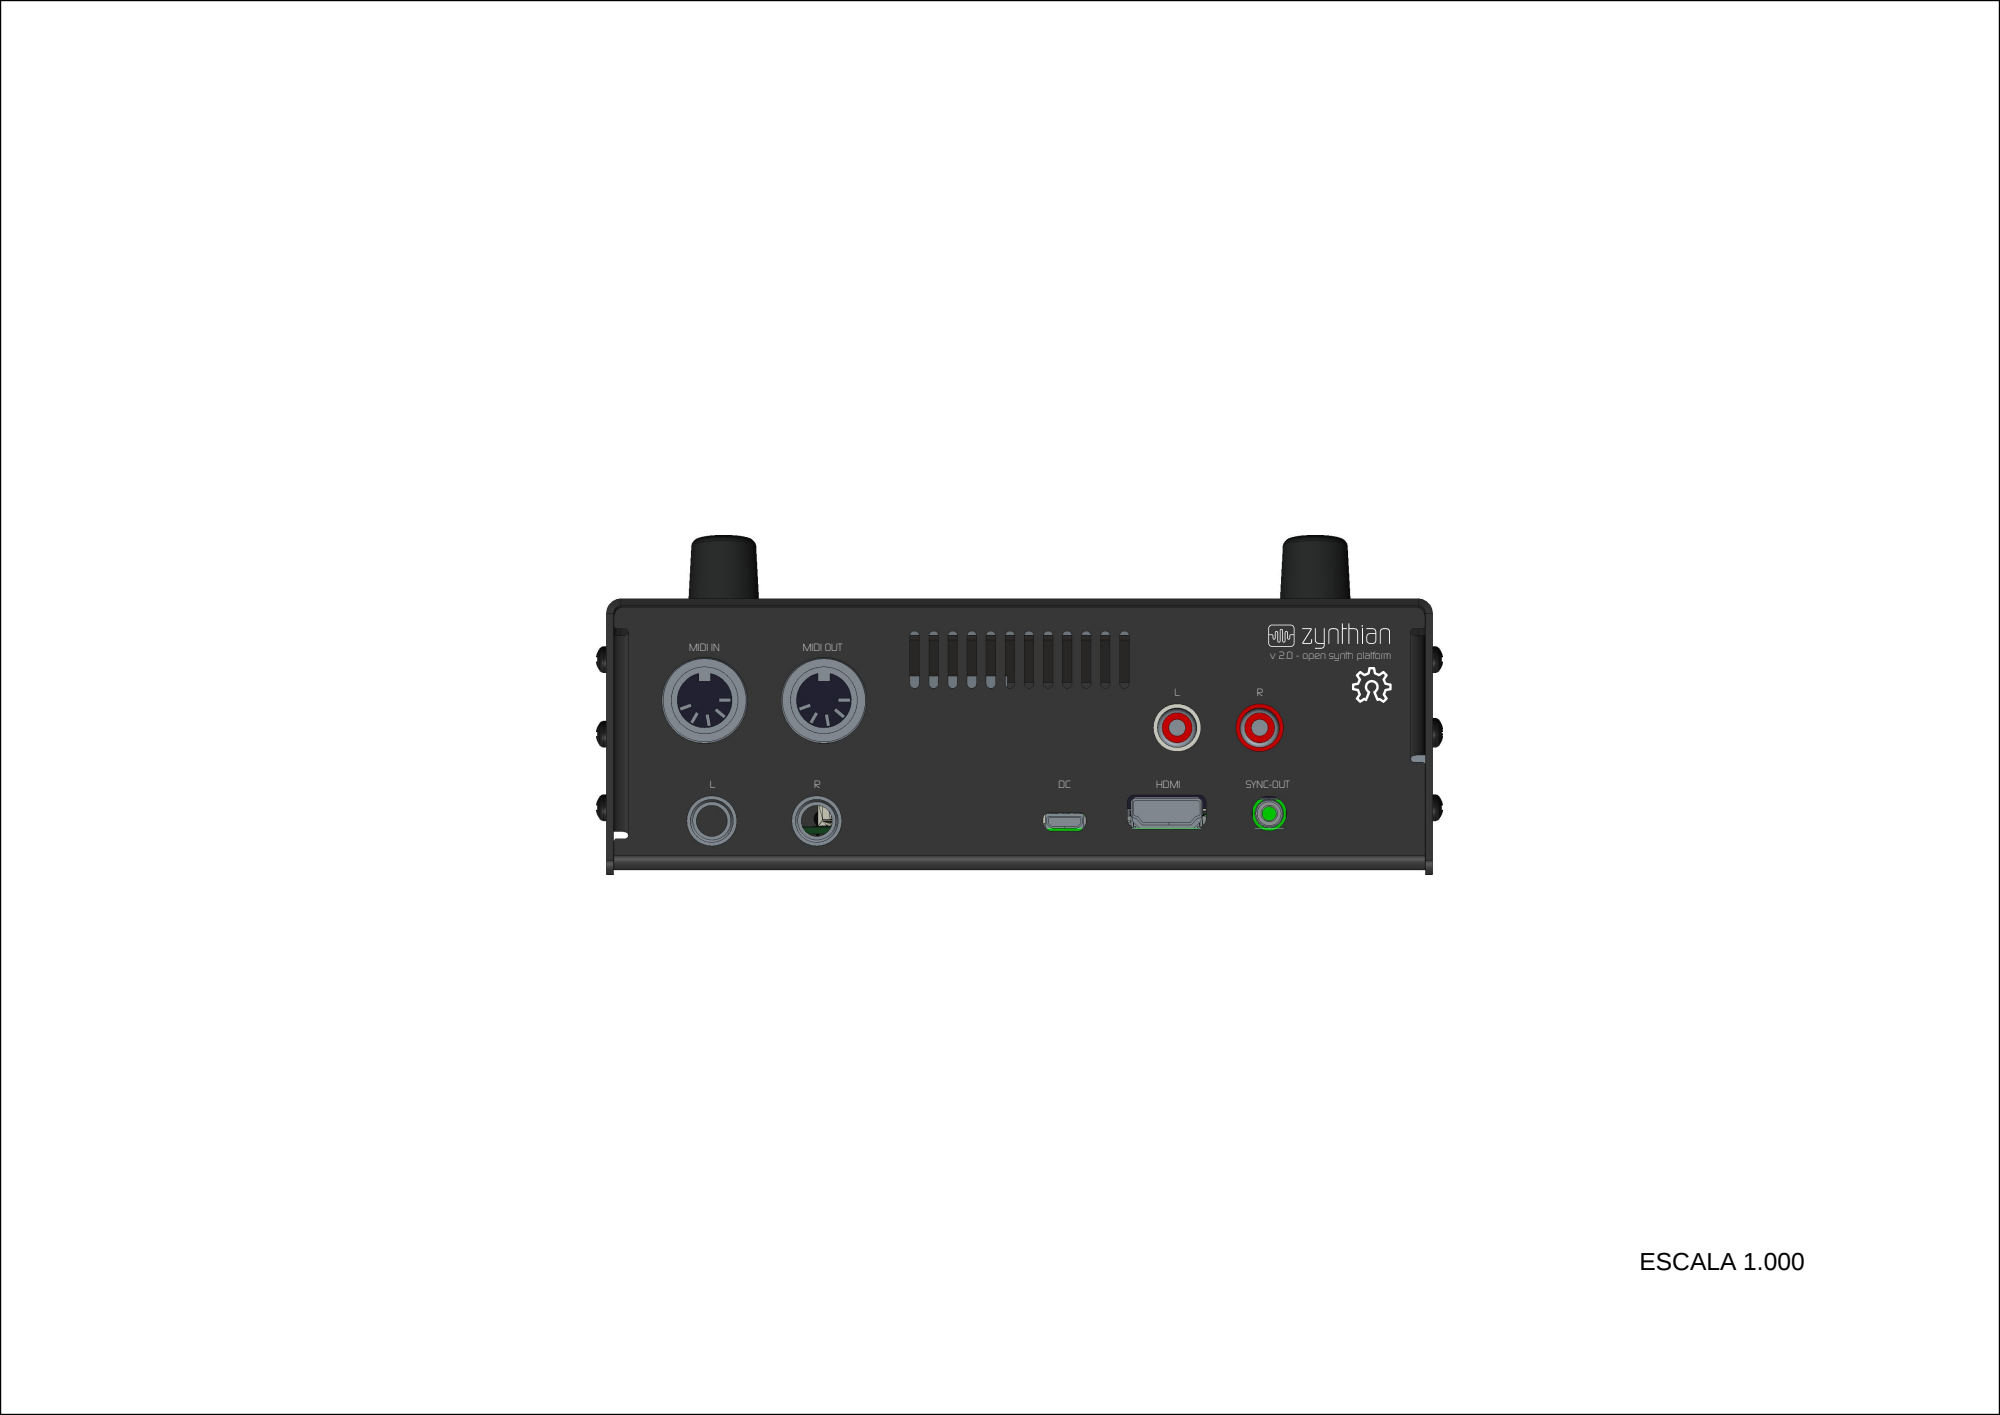
[picture p229: page 1]
ESCALA 1.000; MIDI IN; MIDI OUT; v 2.0 - open synth platform; HDMI; SYNC-OUT
